nazar-pc/NPW-1.0/renders/2-complexity.png

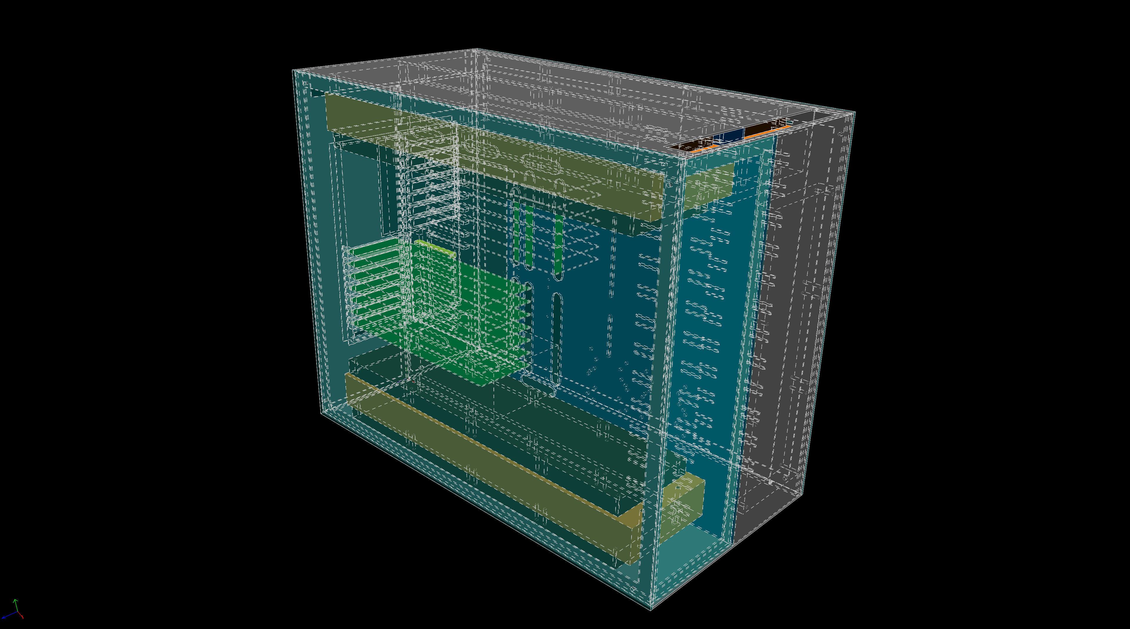
renders/2-complexity.png
