nazar-pc/NPW-1.0/renders/2-left.png

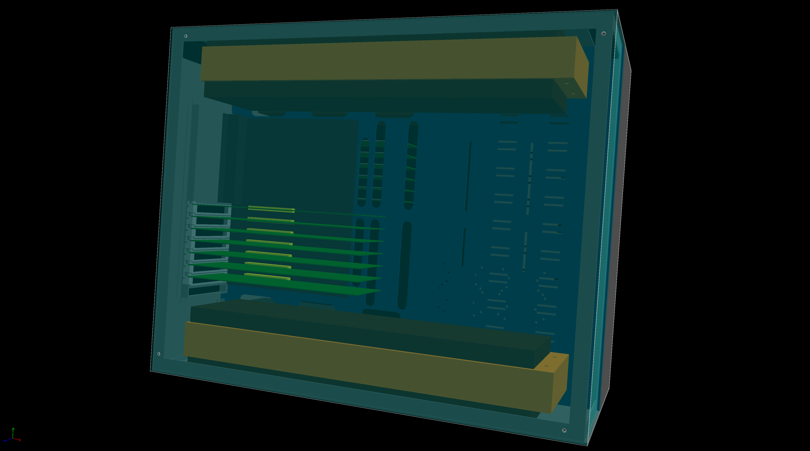
renders/2-left.png
