nazar-pc/NPW-1.0/renders/2-right.png

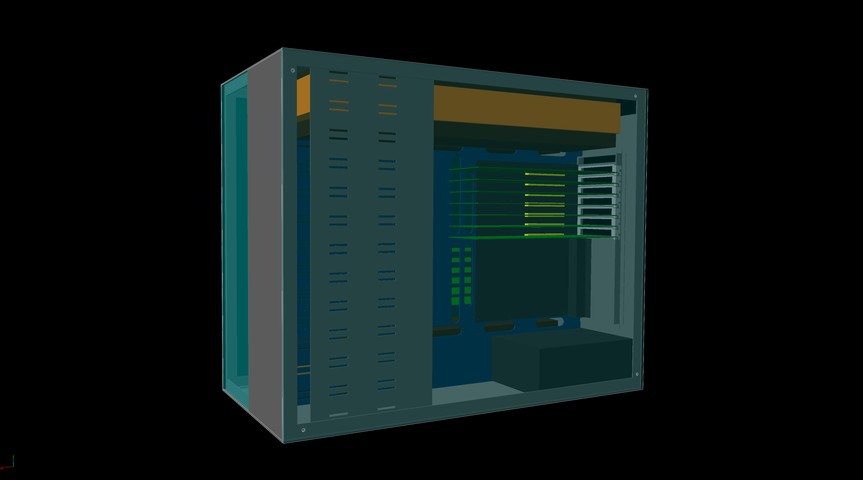
renders/2-right.png
