nazar-pc/NPW-1.0/renders/3-back-right.png

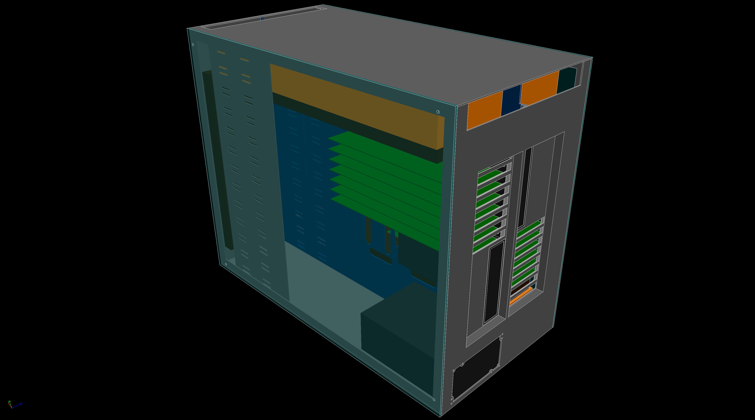
renders/3-back-right.png
