nazar-pc/NPW-1.0/renders/3-left.png

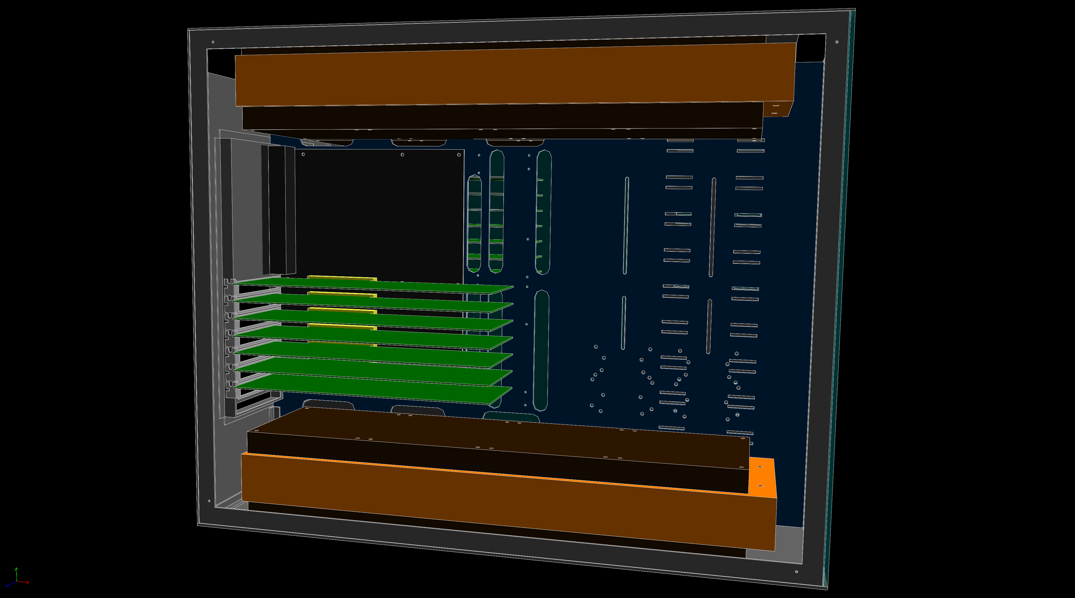
renders/3-left.png
