nazar-pc/NPW-1.0/renders/4-front-panel.png

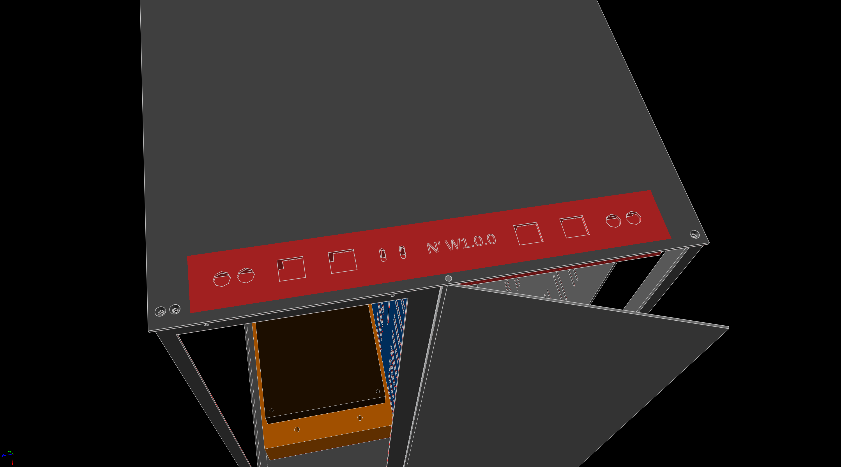
renders/4-front-panel.png
