nazar-pc/NPW-1.0/renders/5-back.png

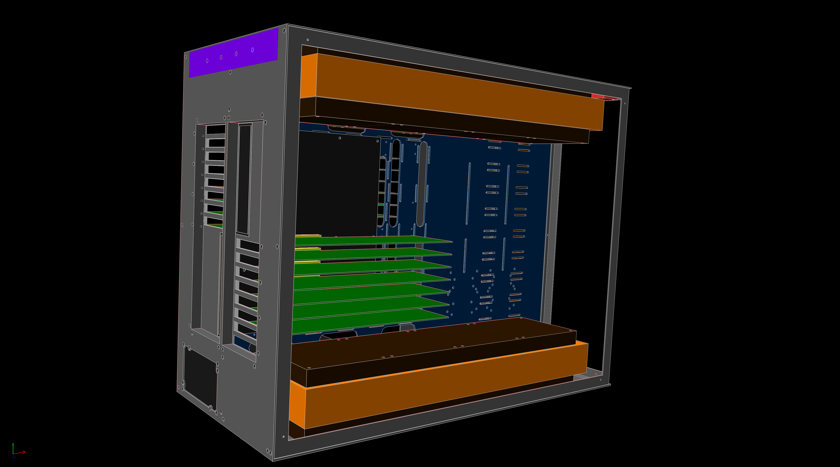
renders/5-back.png
