nazar-pc/NPW-1.0/renders/5-front.png

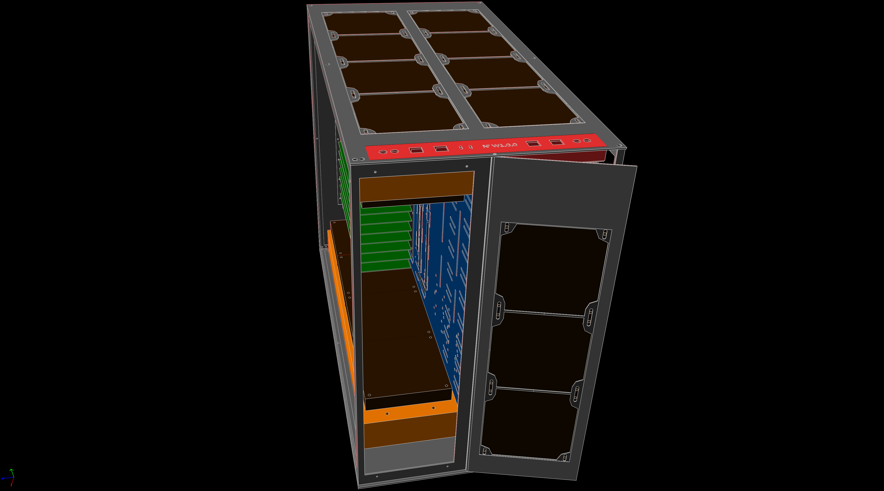
renders/5-front.png
