nazar-pc/NPW-1.0/renders/6-left-bottom.png

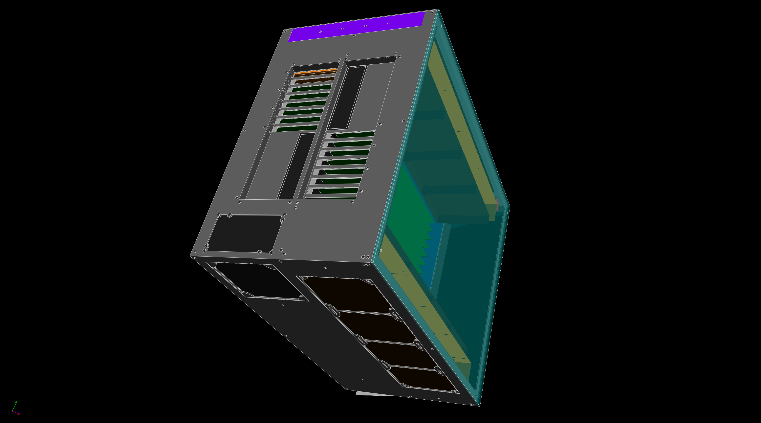
renders/6-left-bottom.png
