nazar-pc/NPW-1.0/renders/6-right-top.png

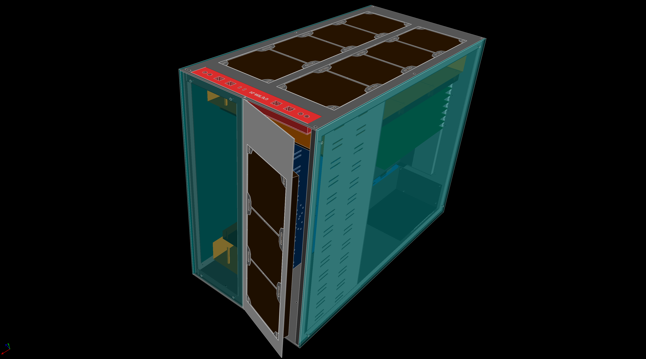
renders/6-right-top.png
