nazar-pc/NPW-1.0/renders/7-back-right.png

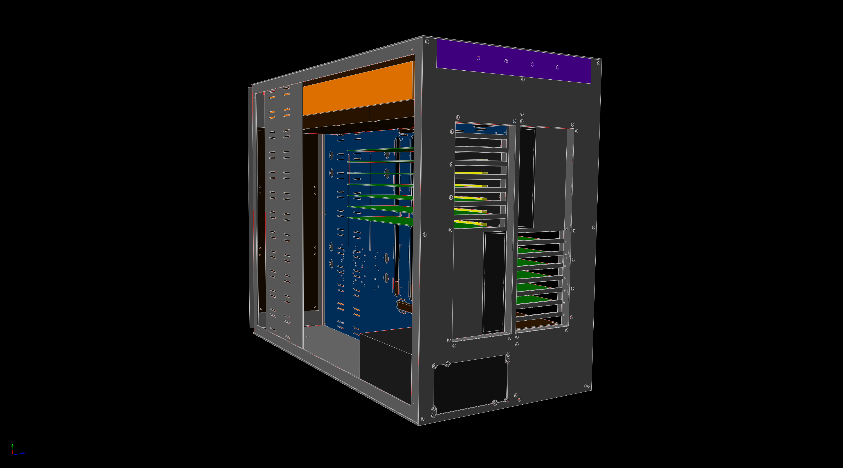
renders/7-back-right.png
