nazar-pc/NPW-1.0/renders/7-left-bottom.png

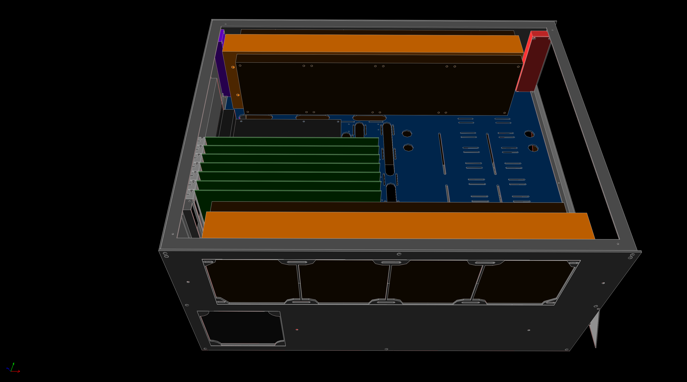
renders/7-left-bottom.png
