nazar-pc/NPW-1.0/renders/7-right-top.png

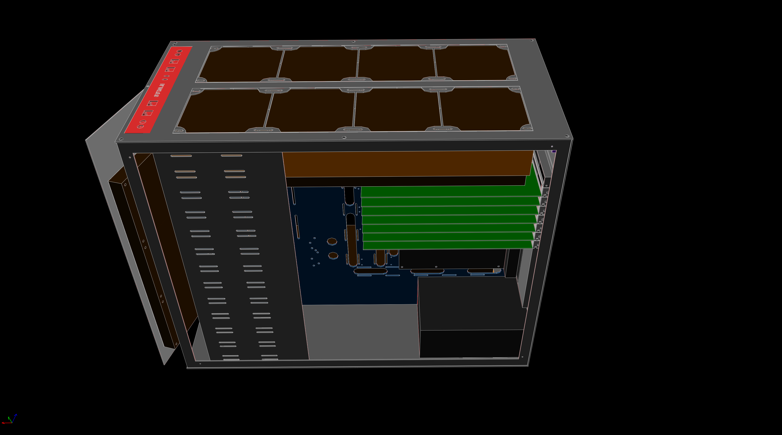
renders/7-right-top.png
