nazar-pc/NPW-1.0/renders/7-top-left.png

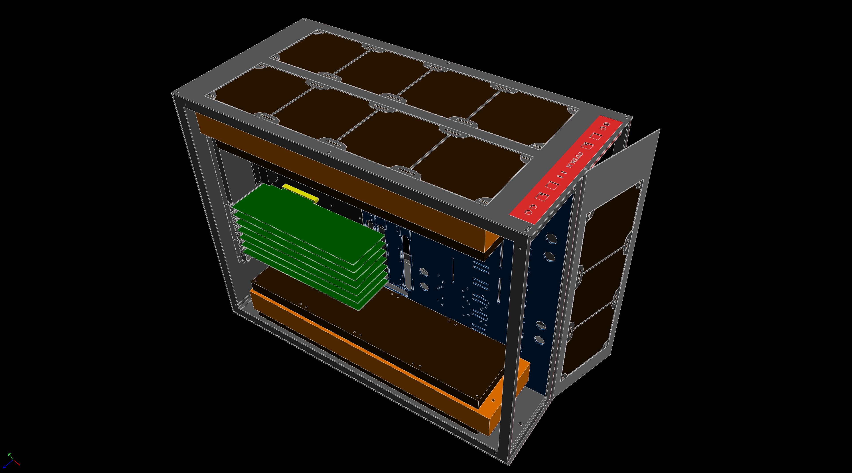
renders/7-top-left.png
