nazar-pc/NPW-1.0/renders/8-back-bottom.png

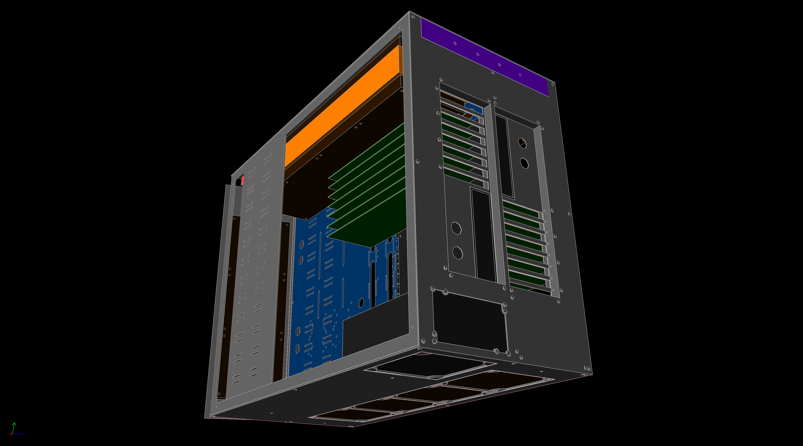
renders/8-back-bottom.png
