nazar-pc/NPW-1.0/renders/9-back-bottom.png

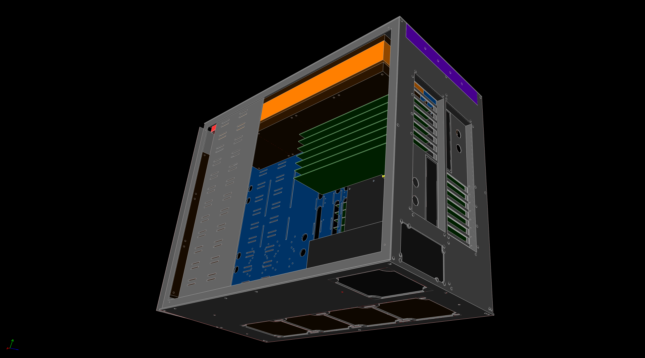
renders/9-back-bottom.png
