nazar-pc/NPW-1.0/renders/9-front-left.png

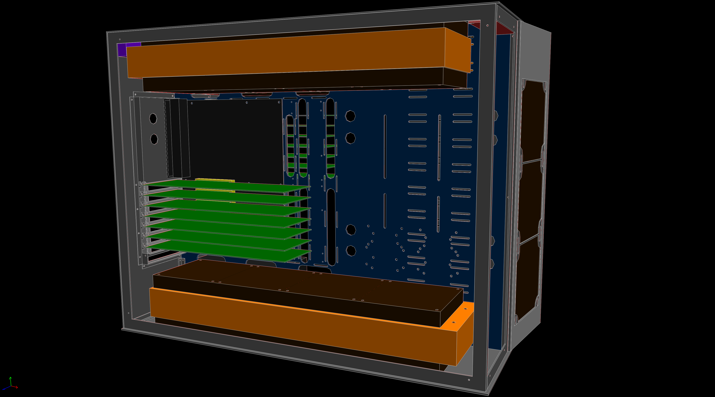
renders/9-front-left.png
