nazar-pc/NPW-1.0/renders/door-mounting-large-scale.png

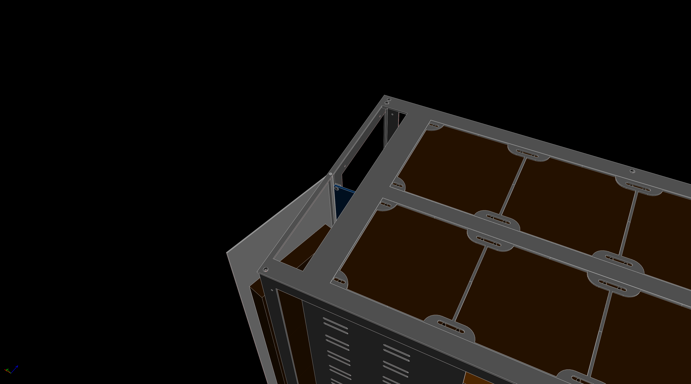
renders/door-mounting-large-scale.png
