nazar-pc/NPW-1.0/renders/door-mounting.png

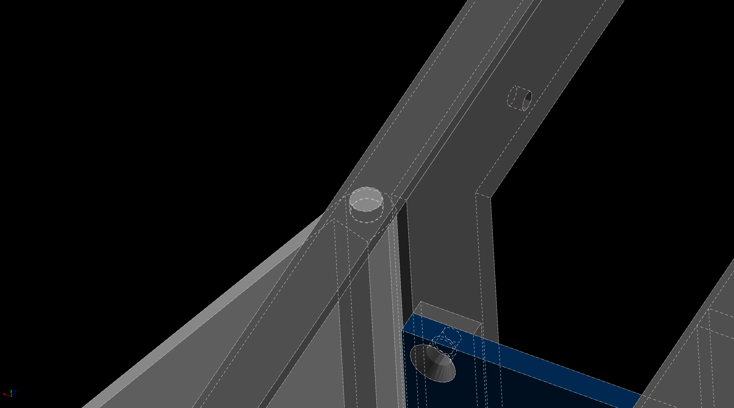
renders/door-mounting.png
