nazar-pc/NPW-1.0/renders/left-back.png

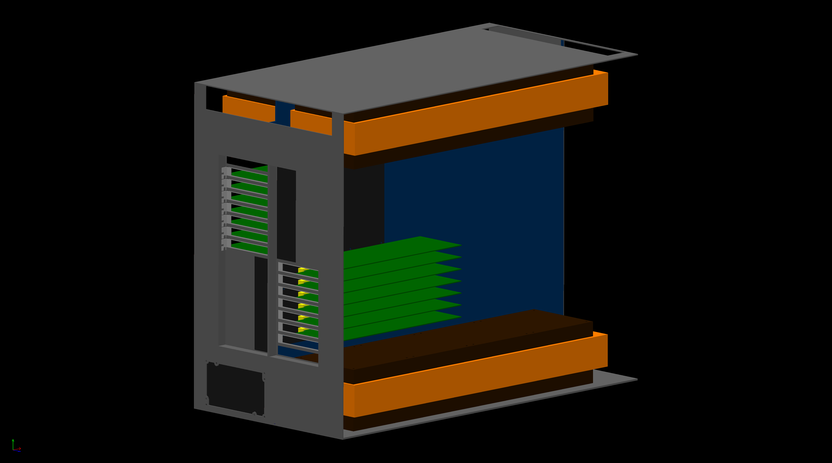
renders/left-back.png
