nazar-pc/NPW-1.0/renders/left-front.png

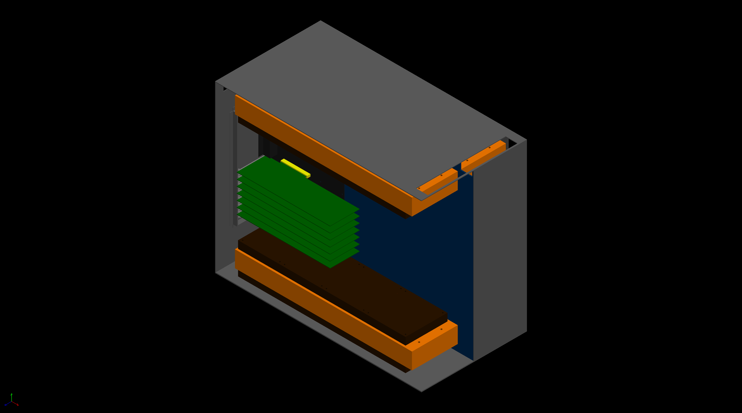
renders/left-front.png
