nazar-pc/NPW-1.0/renders/right-front.png

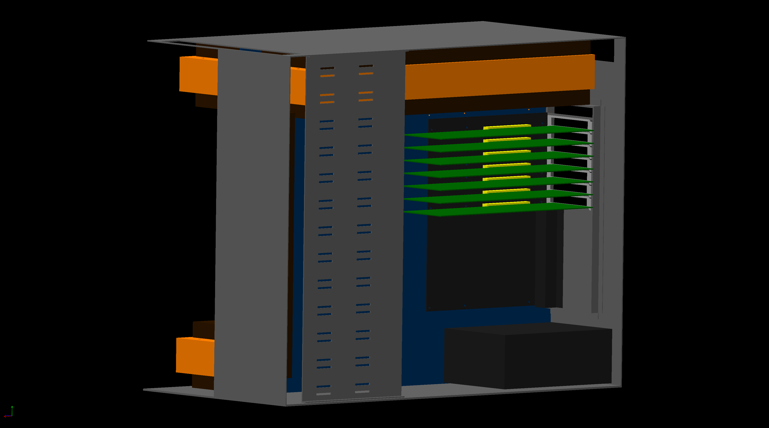
renders/right-front.png
