nazar-pc/NPW-1.0/manufacturing/random-stuff/3D convertion results/back-frame.step

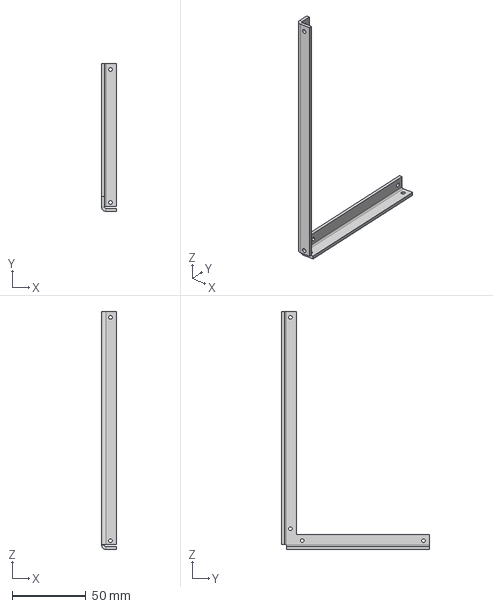
[picture p40: CAD file, 2022-12-24]
manufacturing/random-stuff/3D convertion results/back-frame.step
10.0 x 100.0 x 161.0 mm
