nazar-pc/NPW-1.0/manufacturing/random-stuff/3d-print/top.step

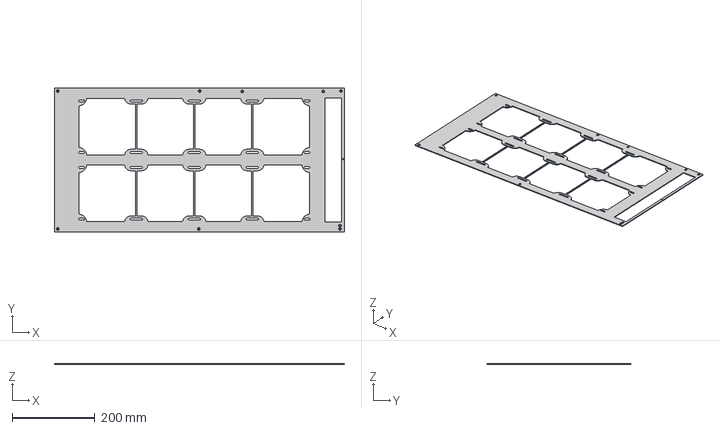
[picture p41: CAD file, 2022-12-24]
manufacturing/random-stuff/3d-print/top.step
700.0 x 347.0 x 2.00 mm
