nazar-pc/NPW-1.0/manufacturing/random-stuff/Assembly -2019.03.23/right-frame.SLDPRT

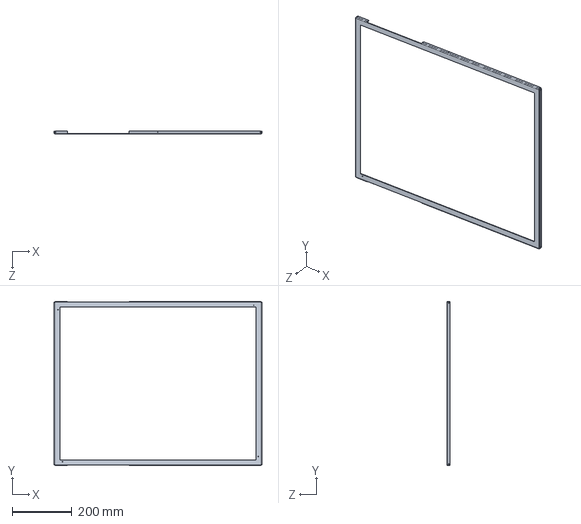
[picture p42: CAD file, 2022-12-24]
manufacturing/random-stuff/Assembly -2019.03.23/right-frame.SLDPRT
695.5 x 550.0 x 10.0 mm
