nazar-pc/NPW-1.0/manufacturing/random-stuff/Dual MB PC Case - sheet metal/Flat pattern - back.DXF

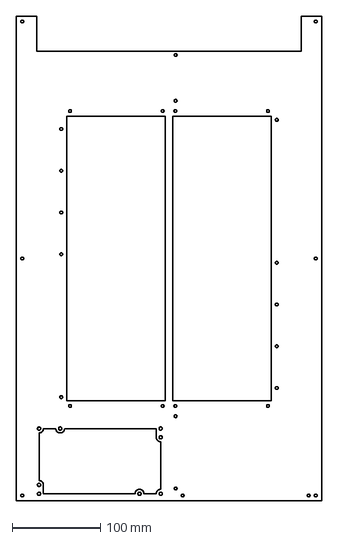
[picture p43: CAD file, 2022-12-24]
manufacturing/random-stuff/Dual MB PC Case - sheet metal/Flat pattern - back.DXF
347.0 x 550.0 mm
