nazar-pc/NPW-1.0/manufacturing/random-stuff/Dual MB PC Case - sheet metal/pc-case.dxf/3mm-bottom.DXF

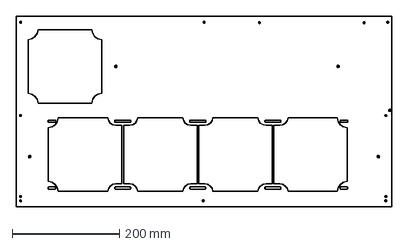
[picture p44: CAD file, 2022-12-24]
manufacturing/random-stuff/Dual MB PC Case - sheet metal/pc-case.dxf/3mm-bottom.DXF
700.0 x 355.0 mm
