nazar-pc/NPW-1.0/manufacturing/random-stuff/Dual mobo PC case full set/step/front-metal.step

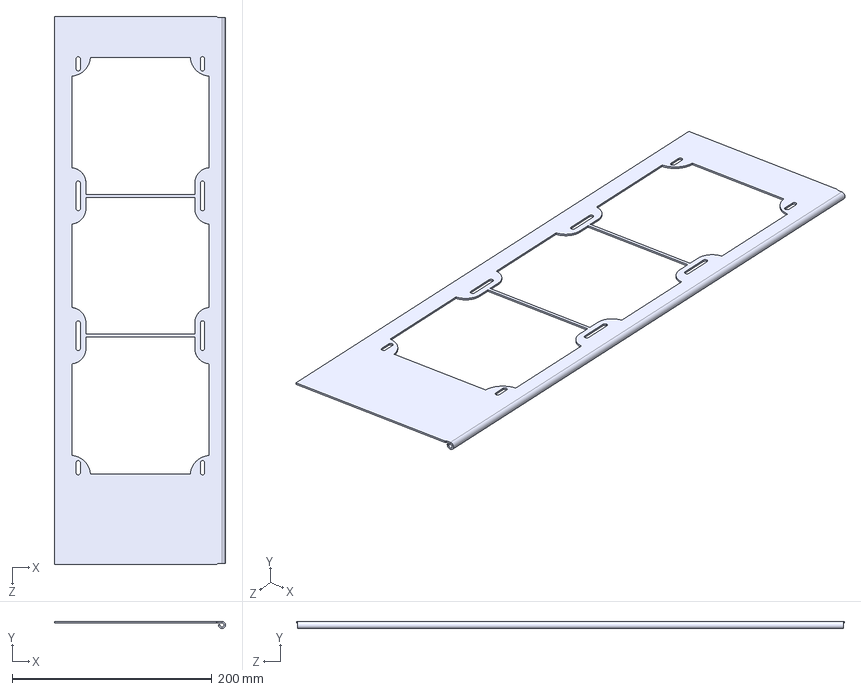
[picture p45: CAD file, 2022-12-24]
manufacturing/random-stuff/Dual mobo PC case full set/step/front-metal.step
171.2 x 7.00 x 549.0 mm
