nazar-pc/NPW-1.0/manufacturing/random-stuff/Hinge with hole.STL

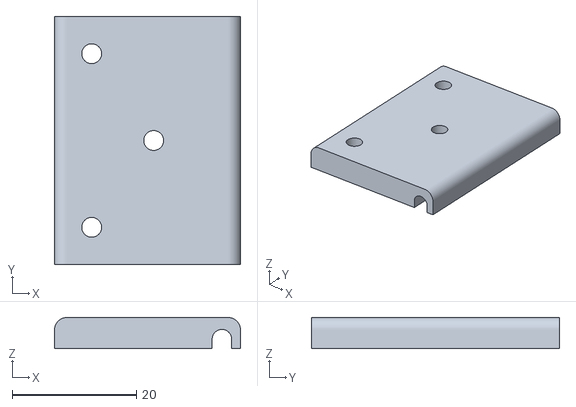
[picture p46: CAD file, 2022-12-24]
manufacturing/random-stuff/Hinge with hole.STL
30.0 x 40.0 x 5.00
