nazar-pc/NPW-1.0/manufacturing/random-stuff/laser-cut/fan-filter.dxf

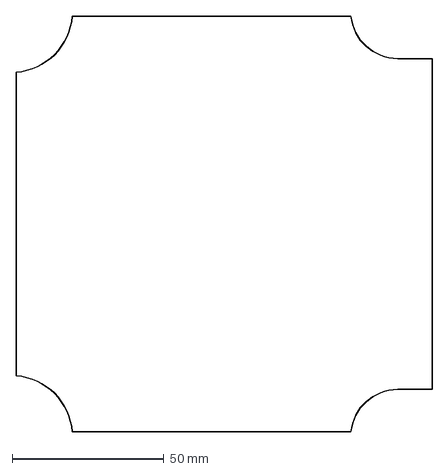
[picture p47: CAD file, 2022-12-24]
manufacturing/random-stuff/laser-cut/fan-filter.dxf
137.0 x 137.0 mm
