nazar-pc/NPW-1.0/manufacturing/step/back-frame-top.step

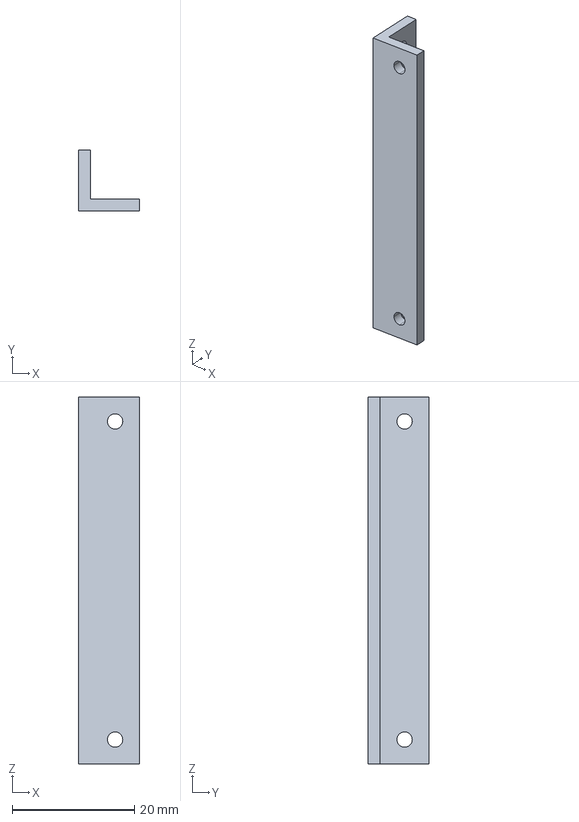
[picture p48: CAD file, 2022-12-24]
manufacturing/step/back-frame-top.step
10.0 x 10.0 x 60.0 mm
