nazar-pc/NPW-1.0/manufacturing/dxf/3d-odd-bay-side.dxf

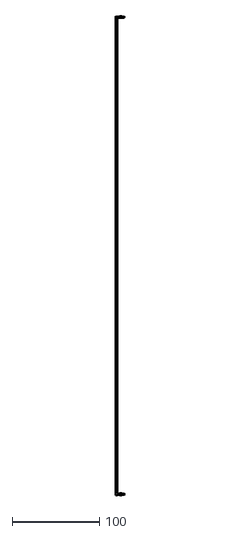
[picture p49: CAD file, 2022-12-24]
manufacturing/dxf/3d-odd-bay-side.dxf
10.0 x 550.0
