nazar-pc/NPW-1.0/manufacturing/random-stuff/3D convertion results/back-frame-top.step

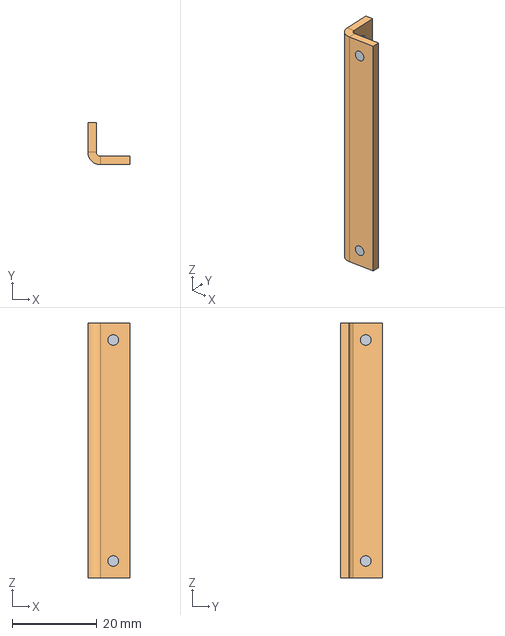
[picture p50: CAD file, 2022-12-24]
manufacturing/random-stuff/3D convertion results/back-frame-top.step
10.0 x 10.0 x 60.0 mm
