nazar-pc/NPW-1.0/manufacturing/random-stuff/3d-print/front-panel-top-base.stl

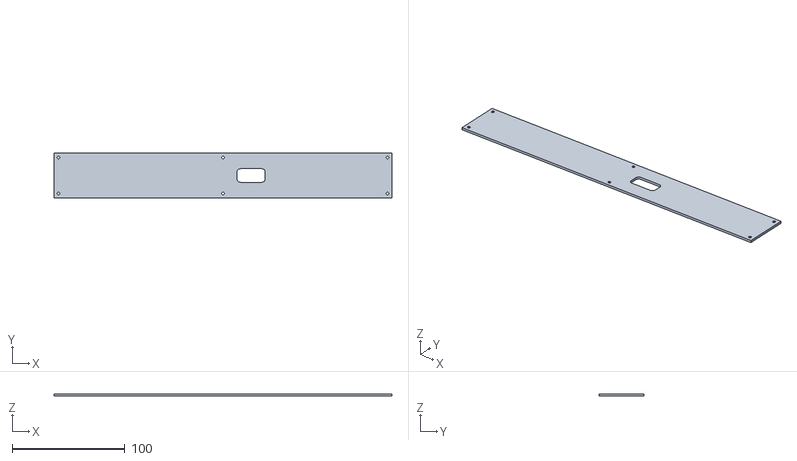
[picture p51: CAD file, 2022-12-24]
manufacturing/random-stuff/3d-print/front-panel-top-base.stl
300.0 x 40.0 x 2.00
