nazar-pc/NPW-1.0/manufacturing/random-stuff/Dual MB PC Case - sheet metal/pc-case.dxf/2mm-odd-bay-side.DXF

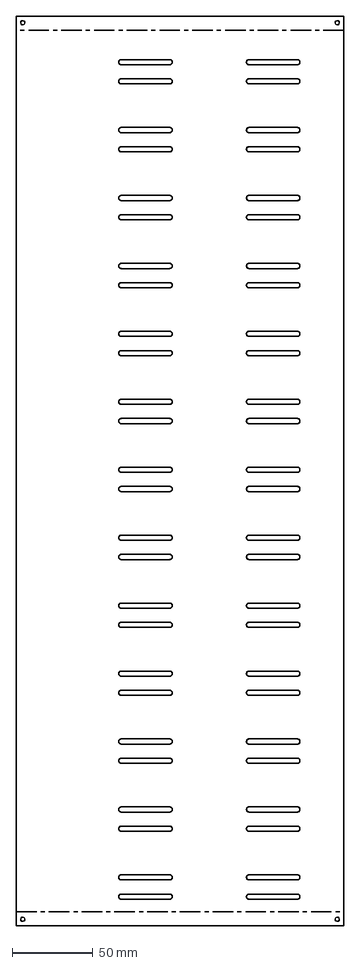
[picture p52: CAD file, 2022-12-24]
manufacturing/random-stuff/Dual MB PC Case - sheet metal/pc-case.dxf/2mm-odd-bay-side.DXF
203.2 x 564.3 mm
