nazar-pc/NPW-1.0/manufacturing/random-stuff/Dual mobo PC case full set/step/bottom.step

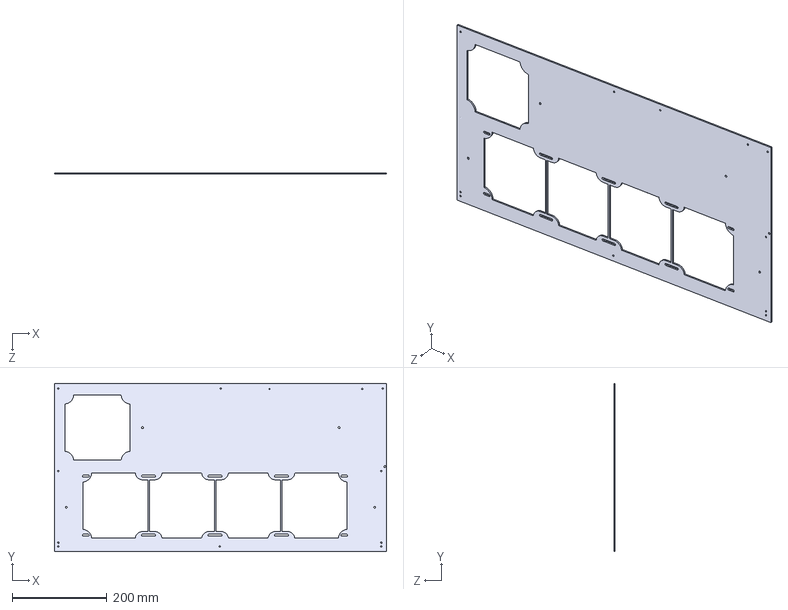
[picture p53: CAD file, 2022-12-24]
manufacturing/random-stuff/Dual mobo PC case full set/step/bottom.step
700.0 x 355.0 x 3.00 mm
