nazar-pc/NPW-1.0/manufacturing/random-stuff/laser-cut/fan-filter-middle.dxf

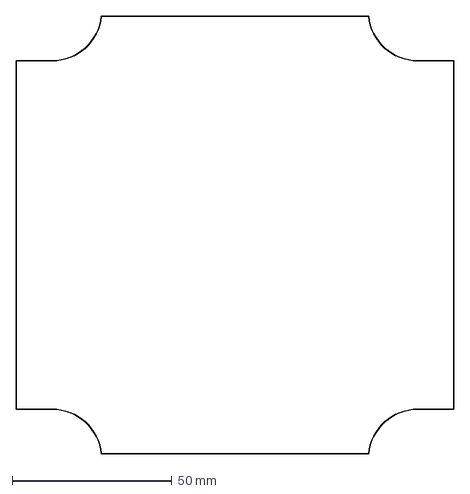
[picture p54: CAD file, 2022-12-24]
manufacturing/random-stuff/laser-cut/fan-filter-middle.dxf
137.0 x 137.0 mm
