nazar-pc/NPW-1.0/manufacturing/step/front-metal.step

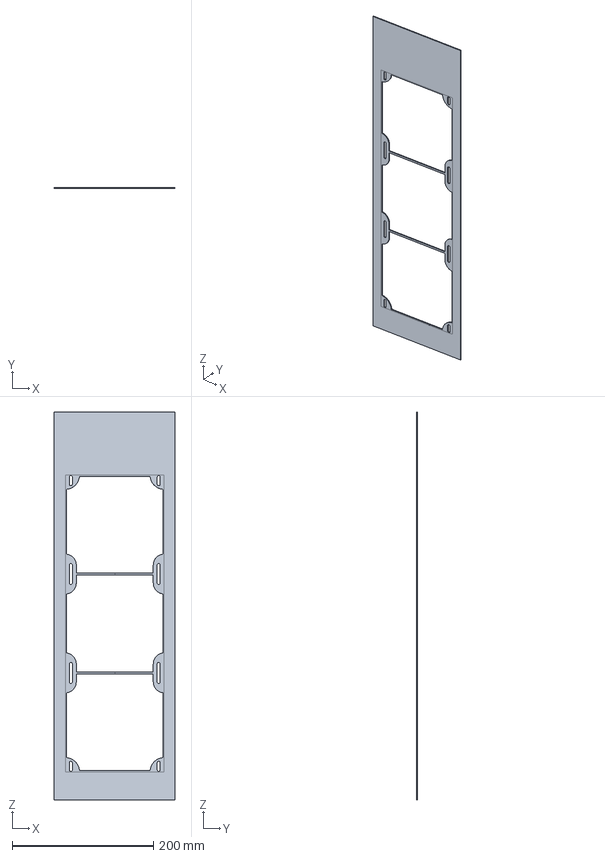
[picture p55: CAD file, 2022-12-24]
manufacturing/step/front-metal.step
171.2 x 1.50 x 549.5 mm
