nazar-pc/NPW-1.0/manufacturing/dxf/3mm-motherboard-tray.dxf

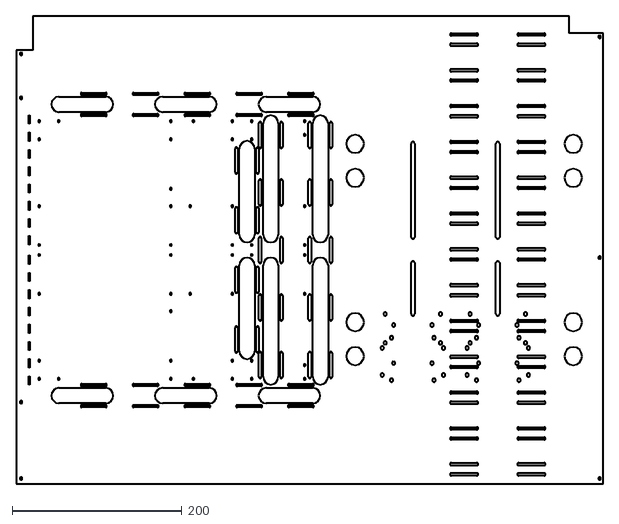
[picture p56: CAD file, 2022-12-24]
manufacturing/dxf/3mm-motherboard-tray.dxf
691.0 x 550.0
