nazar-pc/NPW-1.0/manufacturing/random-stuff/3D convertion results/front-frame.step

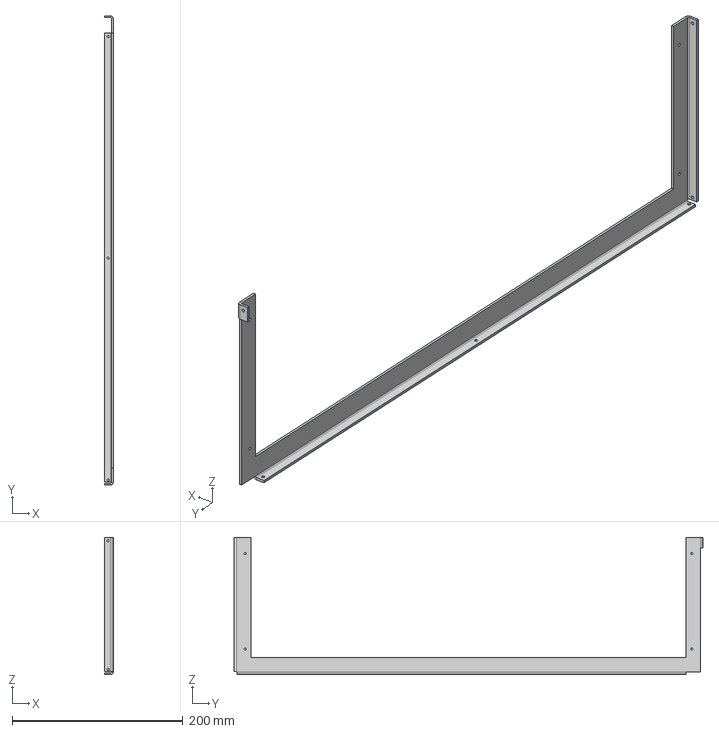
[picture p57: CAD file, 2022-12-24]
manufacturing/random-stuff/3D convertion results/front-frame.step
10.0 x 550.0 x 161.0 mm
