nazar-pc/NPW-1.0/manufacturing/random-stuff/left.step

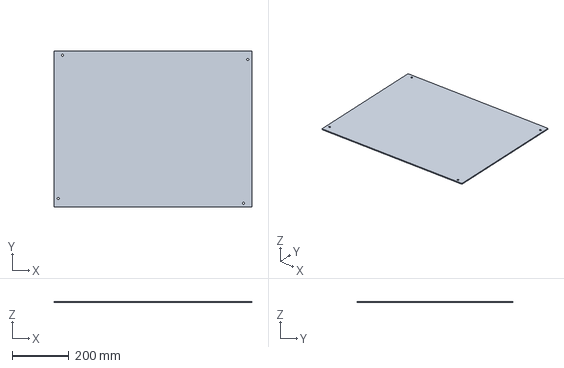
[picture p59: CAD file, 2022-12-24]
manufacturing/random-stuff/left.step
700.0 x 551.0 x 4.00 mm
