nazar-pc/NPW-1.0/manufacturing/step/right-frame.step

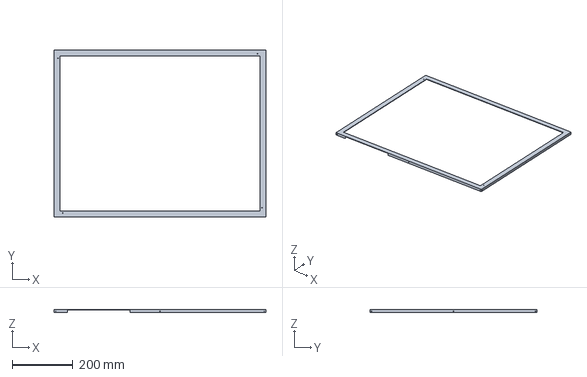
[picture p60: CAD file, 2022-12-24]
manufacturing/step/right-frame.step
696.5 x 550.0 x 10.0 mm
