nazar-pc/NPW-1.0/manufacturing/dxf/2mm-top.dxf

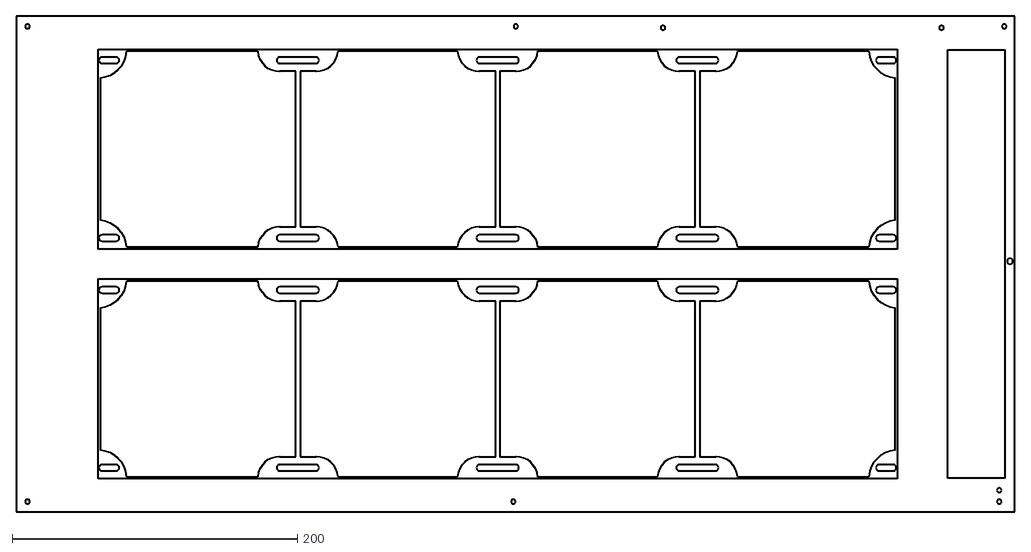
[picture p61: CAD file, 2022-12-24]
manufacturing/dxf/2mm-top.dxf
700.0 x 347.0
