nazar-pc/NPW-1.0/manufacturing/random-stuff/Assembly -2019.03.23/bottom.SLDPRT

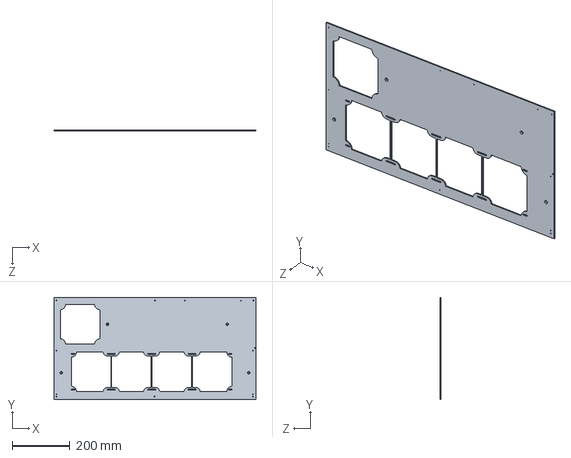
[picture p63: CAD file, 2022-12-24]
manufacturing/random-stuff/Assembly -2019.03.23/bottom.SLDPRT
700.0 x 355.0 x 3.00 mm
