nazar-pc/NPW-1.0/manufacturing/random-stuff/Dual MB PC Case - sheet metal/back.STEP

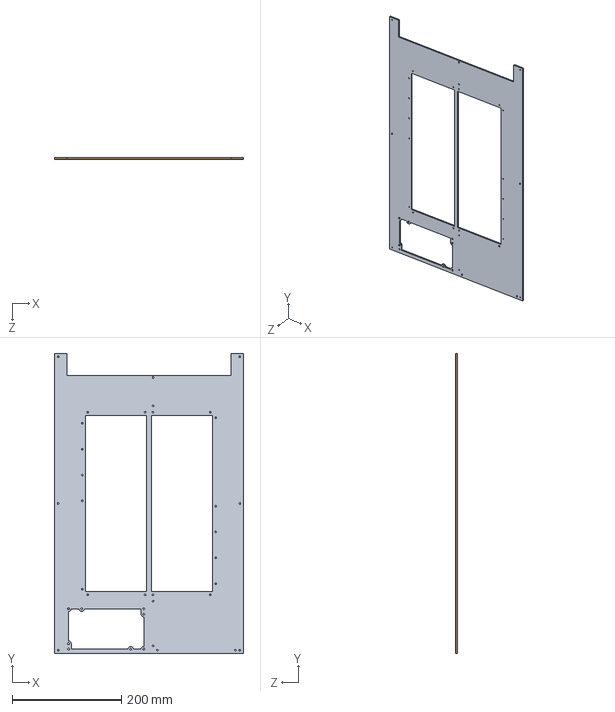
[picture p64: CAD file, 2022-12-24]
manufacturing/random-stuff/Dual MB PC Case - sheet metal/back.STEP
347.0 x 550.0 x 3.00 mm
