nazar-pc/NPW-1.0/manufacturing/random-stuff/Dual mobo PC case full set/step/odd-bay-side.step

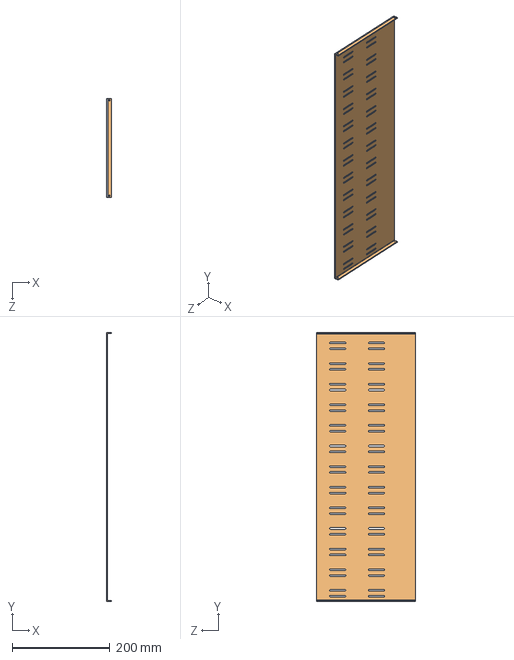
[picture p65: CAD file, 2022-12-24]
manufacturing/random-stuff/Dual mobo PC case full set/step/odd-bay-side.step
10.0 x 550.0 x 203.2 mm
