nazar-pc/NPW-1.0/manufacturing/step/odd-bay-side.step

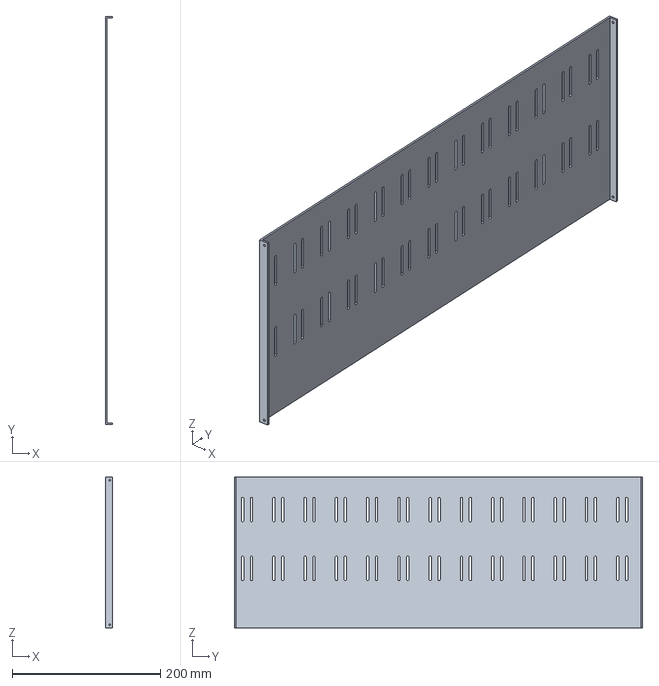
[picture p66: CAD file, 2022-12-24]
manufacturing/step/odd-bay-side.step
10.0 x 550.0 x 203.2 mm
