nazar-pc/NPW-1.0/manufacturing/dxf/2mm-back.dxf

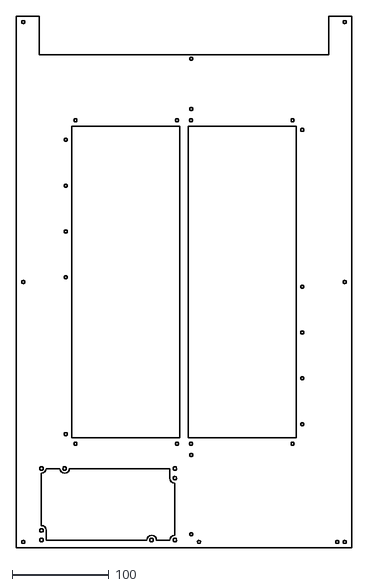
[picture p67: CAD file, 2022-12-24]
manufacturing/dxf/2mm-back.dxf
347.0 x 550.0
