nazar-pc/NPW-1.0/manufacturing/random-stuff/Assembly -2019.03.23/back.SLDPRT

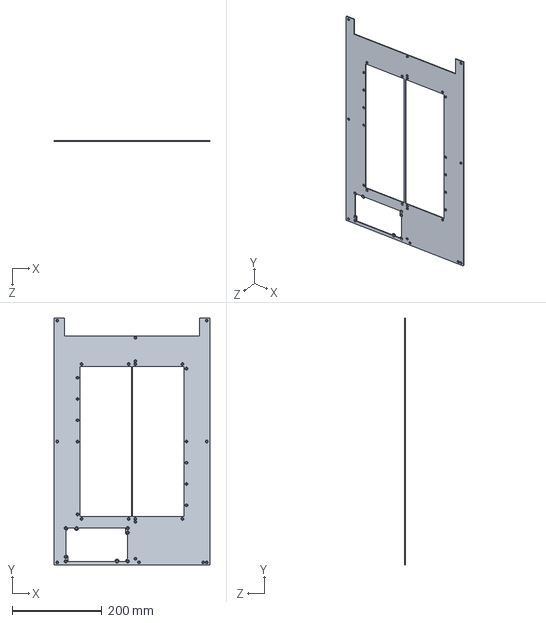
[picture p69: CAD file, 2022-12-24]
manufacturing/random-stuff/Assembly -2019.03.23/back.SLDPRT
347.0 x 550.0 x 2.00 mm
