nazar-pc/NPW-1.0/manufacturing/random-stuff/Dual MB PC Case - sheet metal/pc-case.dxf/1.5mm-front-metal.DXF

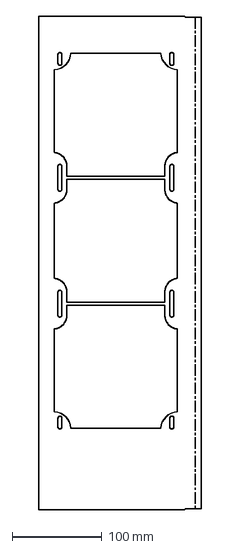
[picture p70: CAD file, 2022-12-24]
manufacturing/random-stuff/Dual MB PC Case - sheet metal/pc-case.dxf/1.5mm-front-metal.DXF
181.2 x 549.0 mm
