nazar-pc/NPW-1.0/manufacturing/step/bottom.step

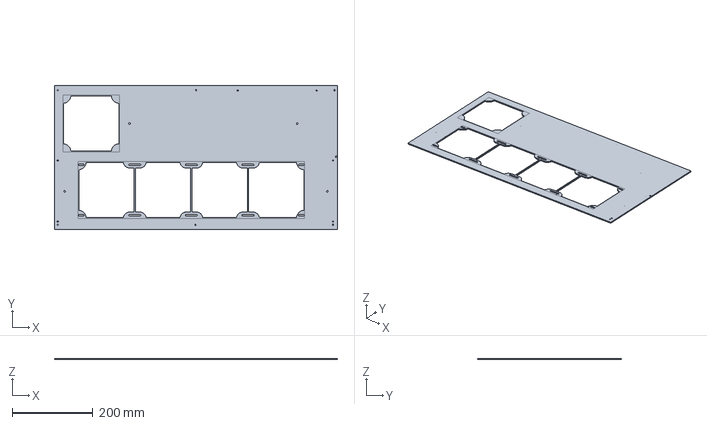
[picture p71: CAD file, 2022-12-24]
manufacturing/step/bottom.step
700.0 x 355.0 x 3.00 mm
