nazar-pc/NPW-1.0/manufacturing/dxf/3d-io-tray-x2.dxf

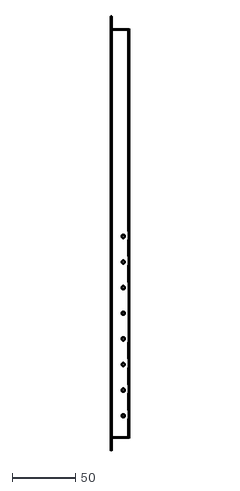
[picture p72: CAD file, 2022-12-24]
manufacturing/dxf/3d-io-tray-x2.dxf
15.0 x 344.8
