nazar-pc/NPW-1.0/manufacturing/random-stuff/3d-print/fan-hole-insert-3mm.step

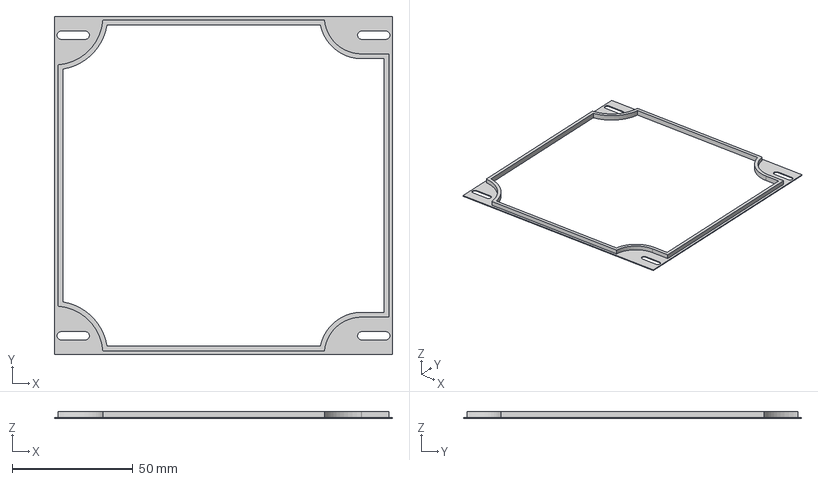
[picture p73: CAD file, 2022-12-24]
manufacturing/random-stuff/3d-print/fan-hole-insert-3mm.step
140.0 x 140.0 x 3.00 mm
