nazar-pc/NPW-1.0/manufacturing/random-stuff/Assembly -2019.03.23/back-frame-top.SLDPRT

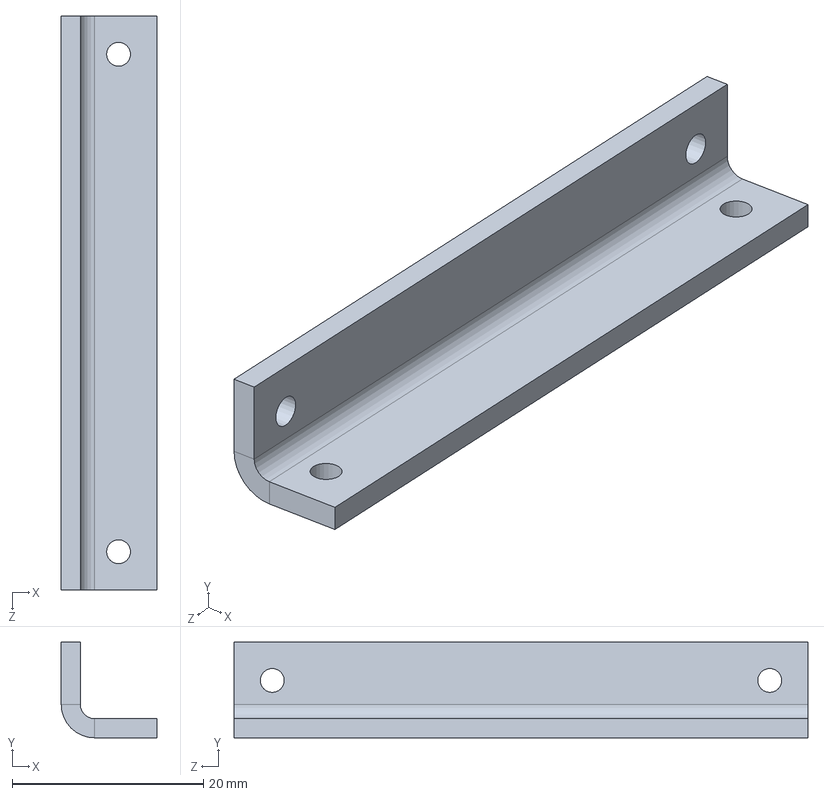
[picture p74: CAD file, 2022-12-24]
manufacturing/random-stuff/Assembly -2019.03.23/back-frame-top.SLDPRT
10.0 x 10.0 x 60.0 mm
