nazar-pc/NPW-1.0/manufacturing/random-stuff/Dual MB PC Case - sheet metal/pc-case.dxf/1mm-io-tray-x2.DXF

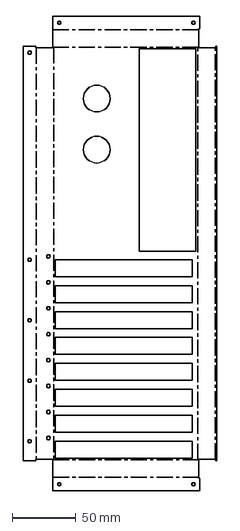
[picture p75: CAD file, 2022-12-24]
manufacturing/random-stuff/Dual MB PC Case - sheet metal/pc-case.dxf/1mm-io-tray-x2.DXF
151.7 x 371.4 mm
