nazar-pc/NPW-1.0/manufacturing/random-stuff/3d-print/fan-hole-insert-2mm-middle v2.step

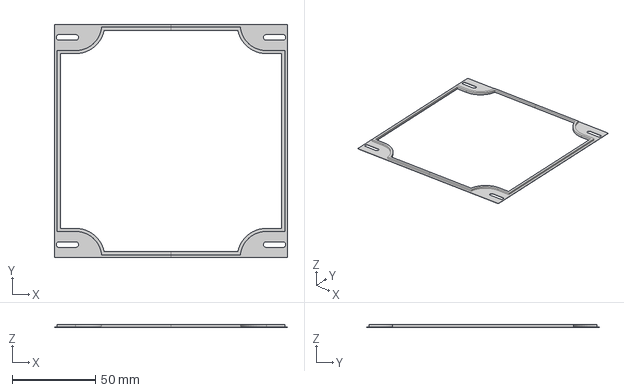
[picture p76: CAD file, 2022-12-24]
manufacturing/random-stuff/3d-print/fan-hole-insert-2mm-middle v2.step
140.0 x 140.0 x 2.00 mm
