nazar-pc/NPW-1.0/manufacturing/random-stuff/Assembly -2019.03.23/IO-frame.SLDPRT

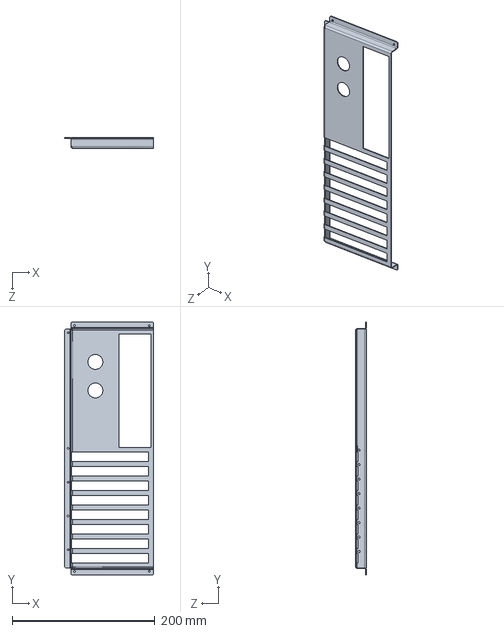
[picture p77: CAD file, 2022-12-24]
manufacturing/random-stuff/Assembly -2019.03.23/IO-frame.SLDPRT
124.8 x 354.8 x 15.0 mm
