nazar-pc/NPW-1.0/manufacturing/random-stuff/Hinge.STL

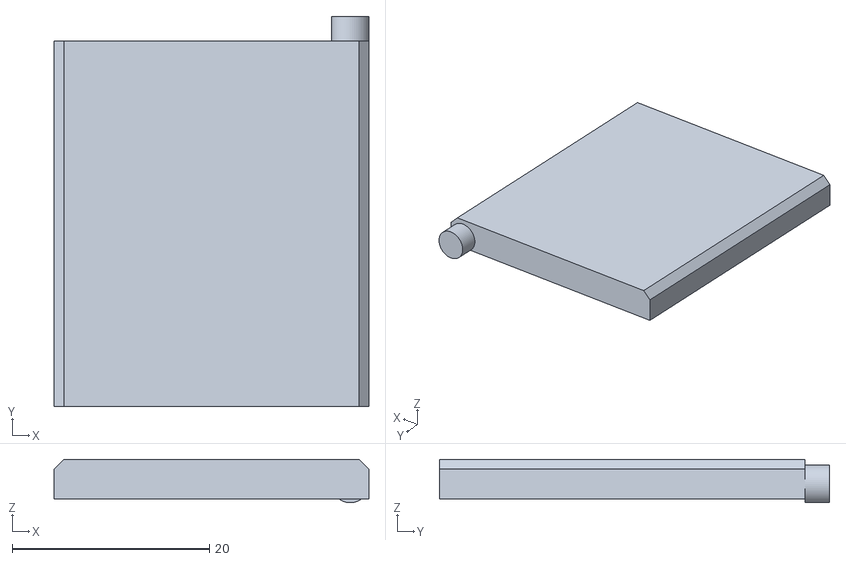
[picture p78: CAD file, 2022-12-24]
manufacturing/random-stuff/Hinge.STL
31.9 x 39.5 x 4.40
