nazar-pc/NPW-1.0/manufacturing/random-stuff/3d-print/3mm insert.step

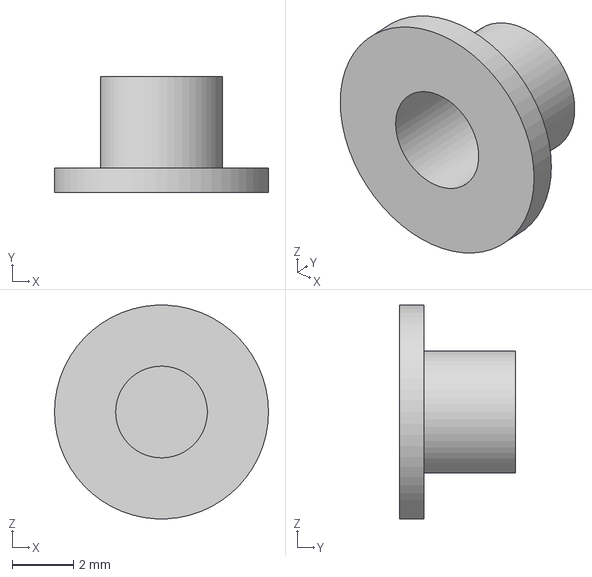
[picture p79: CAD file, 2022-12-24]
manufacturing/random-stuff/3d-print/3mm insert.step
7.00 x 3.80 x 6.99 mm
