nazar-pc/NPW-1.0/manufacturing/step/top.step

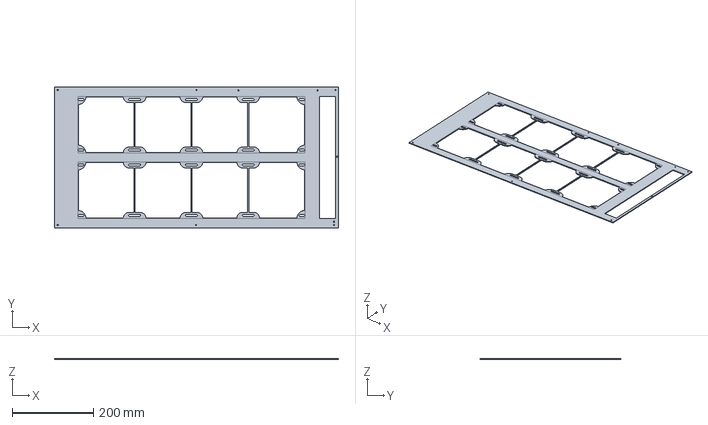
[picture p80: CAD file, 2022-12-24]
manufacturing/step/top.step
700.0 x 347.0 x 2.00 mm
