nazar-pc/NPW-1.0/manufacturing/random-stuff/3d-print/glass-mount-top.step

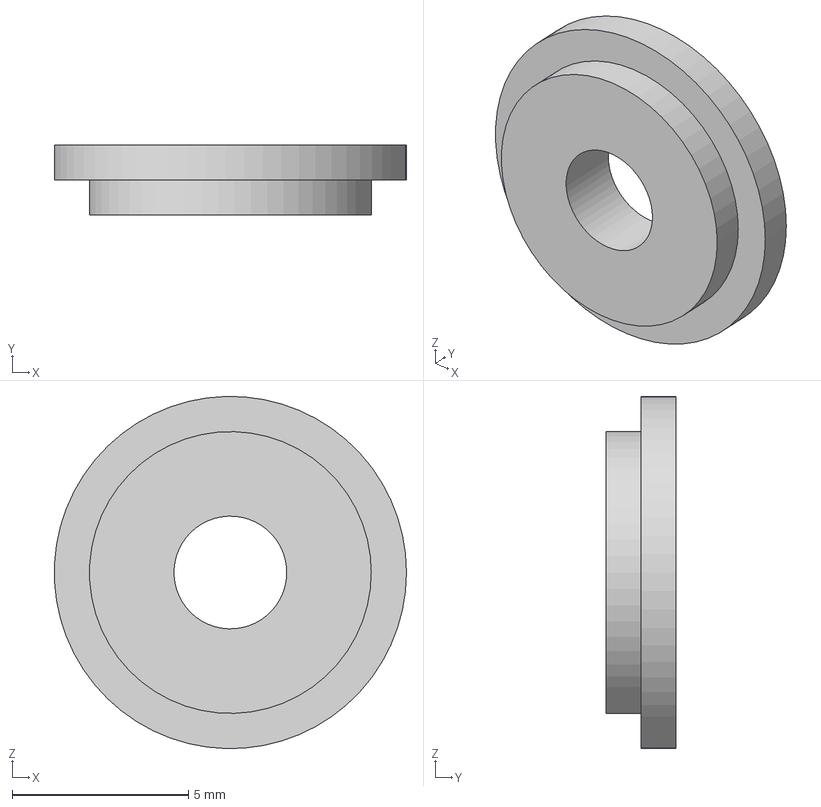
[picture p81: CAD file, 2022-12-24]
manufacturing/random-stuff/3d-print/glass-mount-top.step
9.99 x 2.00 x 10.00 mm
