nazar-pc/NPW-1.0/manufacturing/random-stuff/Assembly -2019.03.23/io-tray-x2_SM.SLDPRT

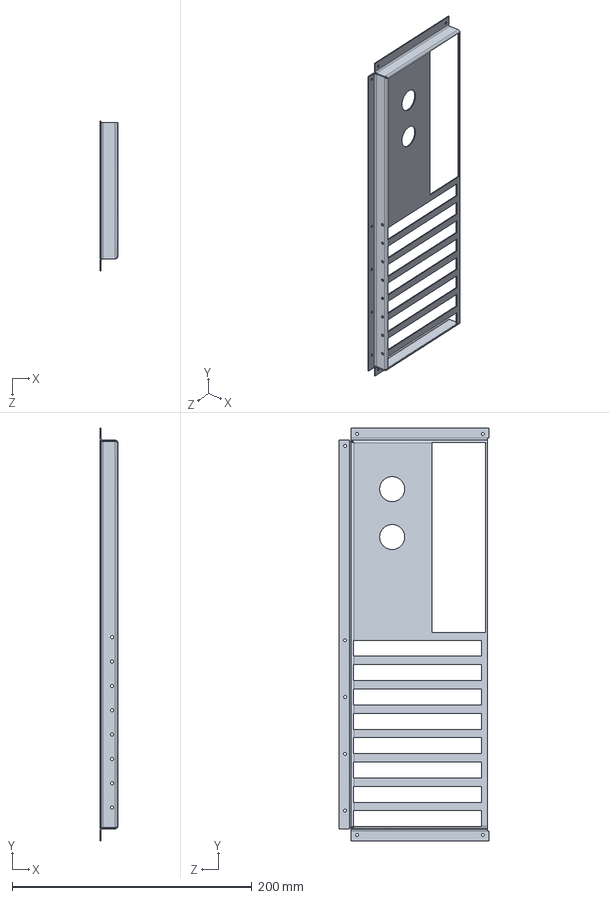
[picture p82: CAD file, 2022-12-24]
manufacturing/random-stuff/Assembly -2019.03.23/io-tray-x2_SM.SLDPRT
15.0 x 344.8 x 125.1 mm
