nazar-pc/NPW-1.0/manufacturing/random-stuff/glass-mount-v2.stl

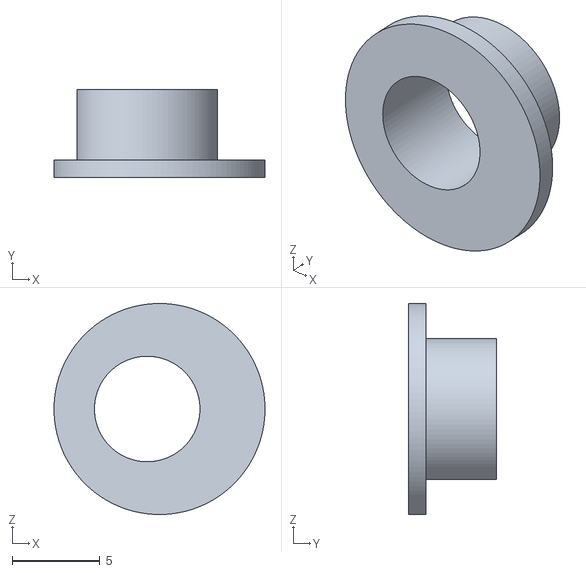
[picture p83: CAD file, 2022-12-24]
manufacturing/random-stuff/glass-mount-v2.stl
12.0 x 5.00 x 12.0
