nazar-pc/NPW-1.0/manufacturing/random-stuff/multi-ssd-cage-7x.stl

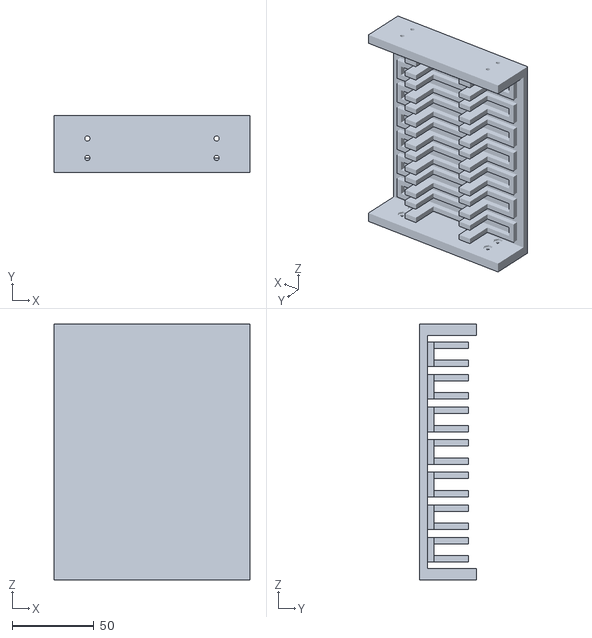
[picture p84: CAD file, 2022-12-24]
manufacturing/random-stuff/multi-ssd-cage-7x.stl
120.0 x 35.0 x 157.1
