nazar-pc/NPW-1.0/manufacturing/random-stuff/3d-print/front-panel-lock.step

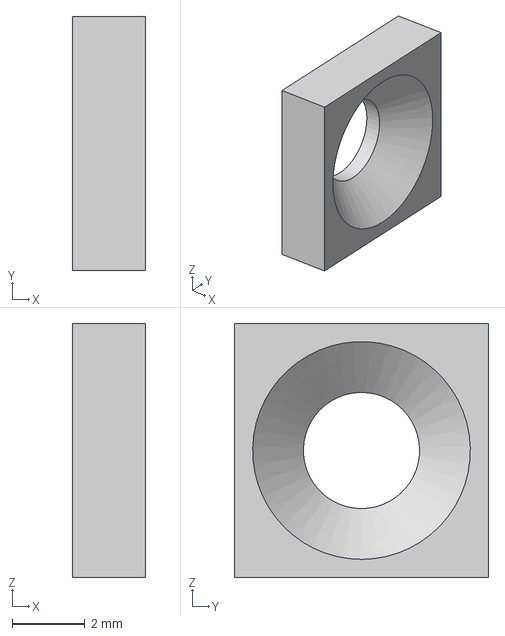
[picture p85: CAD file, 2022-12-24]
manufacturing/random-stuff/3d-print/front-panel-lock.step
2.00 x 7.00 x 7.00 mm
