nazar-pc/NPW-1.0/manufacturing/random-stuff/Assembly -2019.03.23/front-metal.SLDPRT

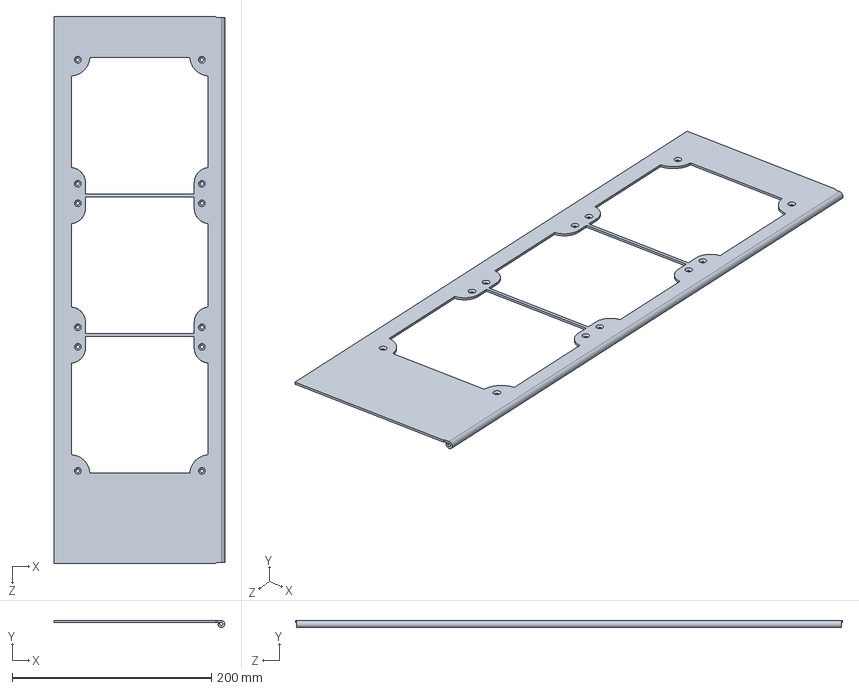
[picture p86: CAD file, 2022-12-24]
manufacturing/random-stuff/Assembly -2019.03.23/front-metal.SLDPRT
171.2 x 6.99 x 549.0 mm
