nazar-pc/NPW-1.0/manufacturing/random-stuff/side.dxf

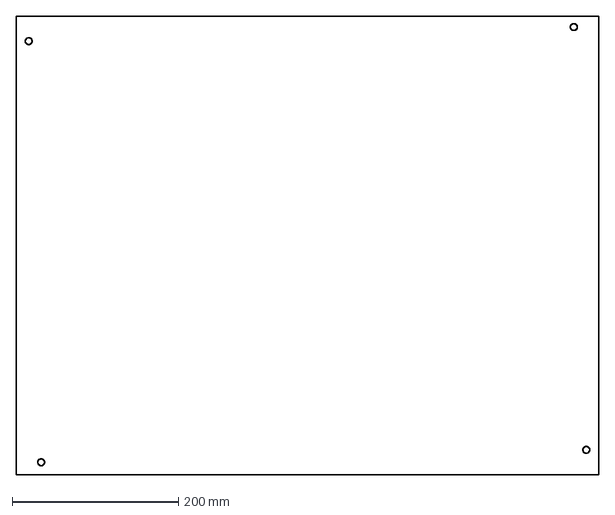
[picture p87: CAD file, 2022-12-24]
manufacturing/random-stuff/side.dxf
700.0 x 551.0 mm
