nazar-pc/NPW-1.0/manufacturing/random-stuff/front-glass.dxf

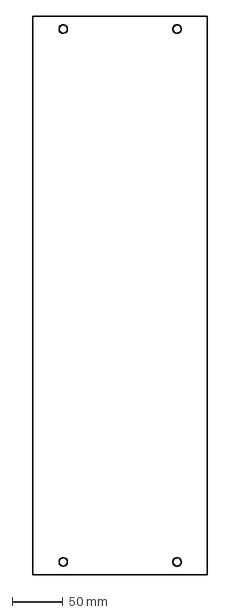
[picture p88: CAD file, 2022-12-24]
manufacturing/random-stuff/front-glass.dxf
171.8 x 549.5 mm
