nazar-pc/NPW-1.0/manufacturing/random-stuff/front-metal.step

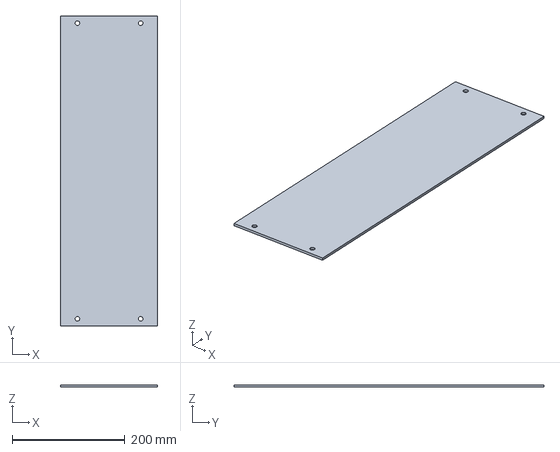
[picture p89: CAD file, 2022-12-24]
manufacturing/random-stuff/front-metal.step
171.8 x 549.5 x 4.00 mm
