nazar-pc/NPW-1.0/manufacturing/pdf/odd-bay-side.pdf

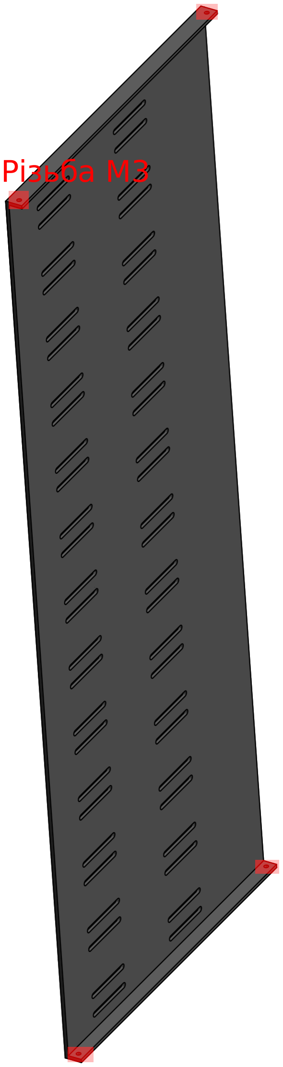
[picture p96: page 1]

Різьба М3
