nazar-pc/NPW-1.0/manufacturing/pdf/right-frame.pdf

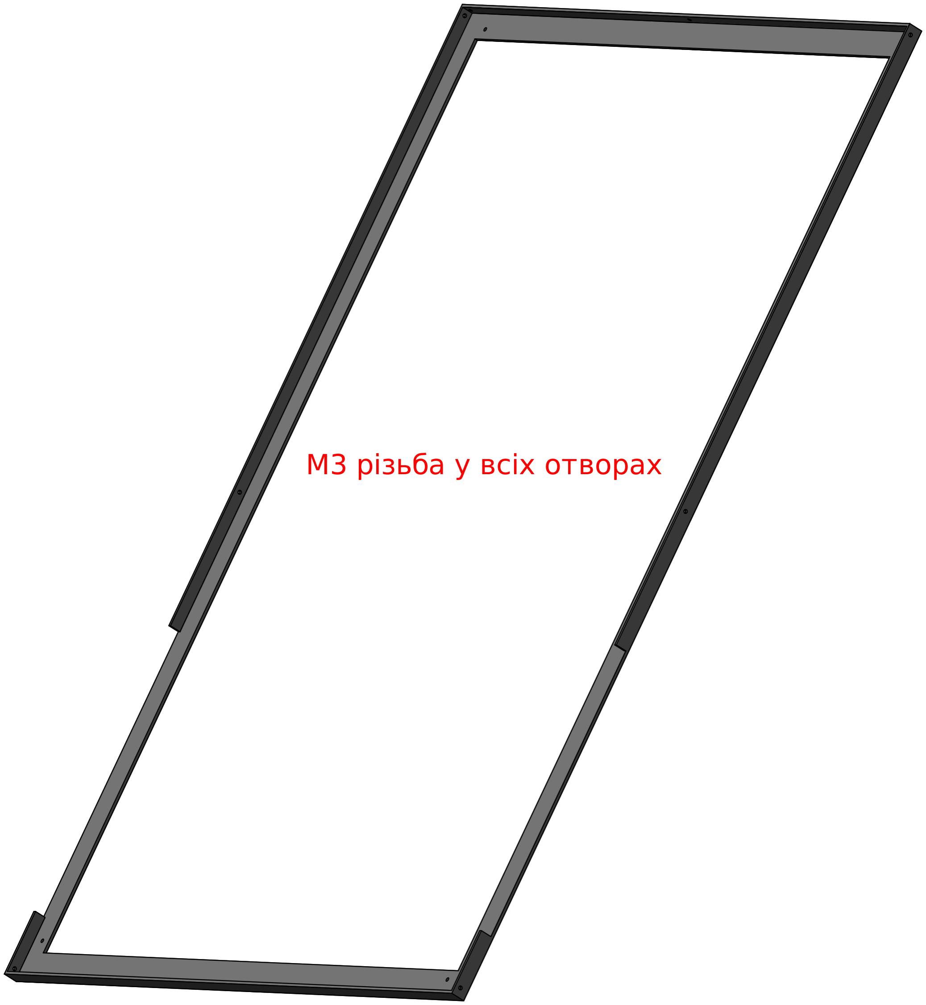
[picture p97: page 1]

М3 різьба у всіх отворах
