nazar-pc/NPW-1.0/manufacturing/pdf/top.pdf

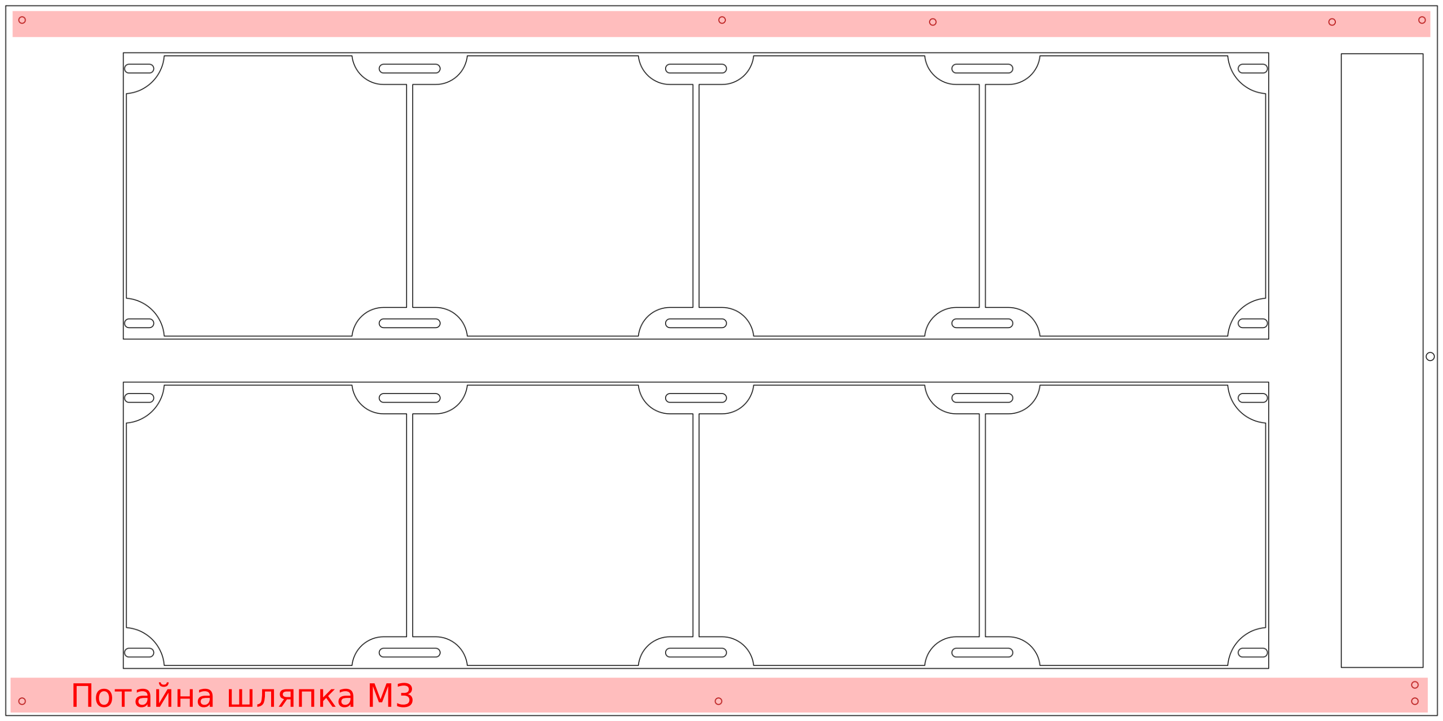
[picture p98: page 1]

Потайна шляпка М3
