nazar-pc/NPW-1.0/initial-build-pictures/IMG_20191107_225444.jpg

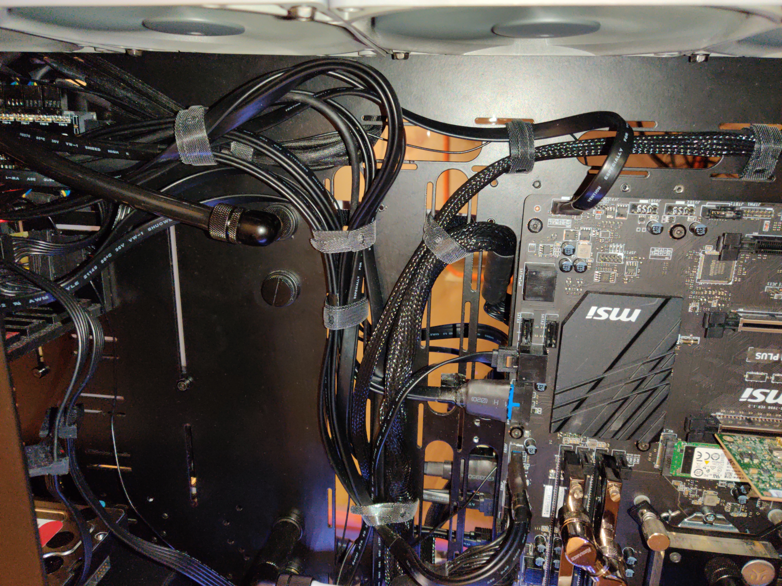
initial-build-pictures/IMG_20191107_225444.jpg
