nazar-pc/NPW-1.0/initial-build-pictures/IMG_20191107_230017.jpg

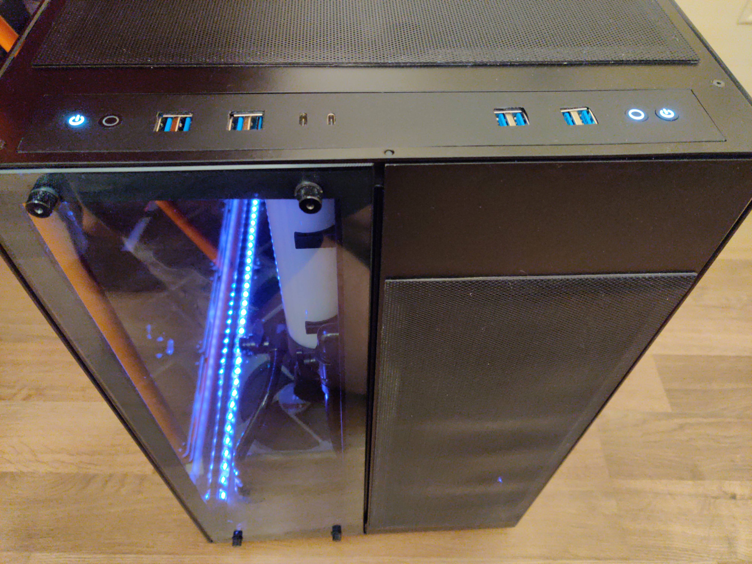
initial-build-pictures/IMG_20191107_230017.jpg
