nazar-pc/NPW-1.0/manufacturing/random-stuff/Assembly.SLDASM.png

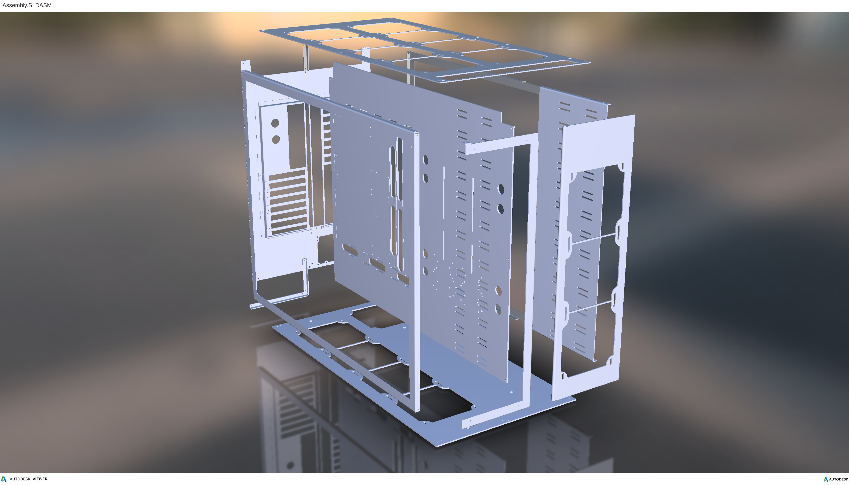
manufacturing/random-stuff/Assembly.SLDASM.png
