nazar-pc/NPW-1.0/manufacturing/random-stuff/Dual MB PC Case - sheet metal/Screenshots/2018-10-27_163635.png

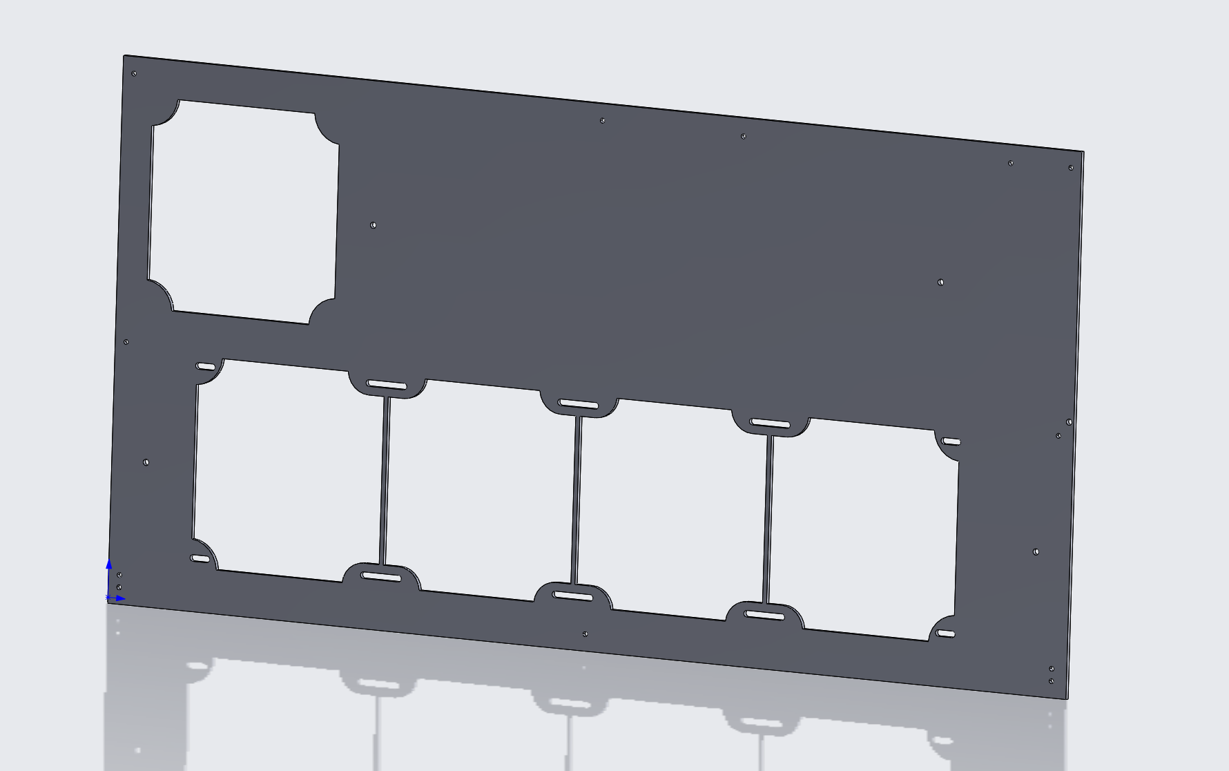
manufacturing/random-stuff/Dual MB PC Case - sheet metal/Screenshots/2018-10-27_163635.png
