nazar-pc/NPW-1.0/manufacturing/random-stuff/DualMB sheet metal drawings 2019.01.16.PDF

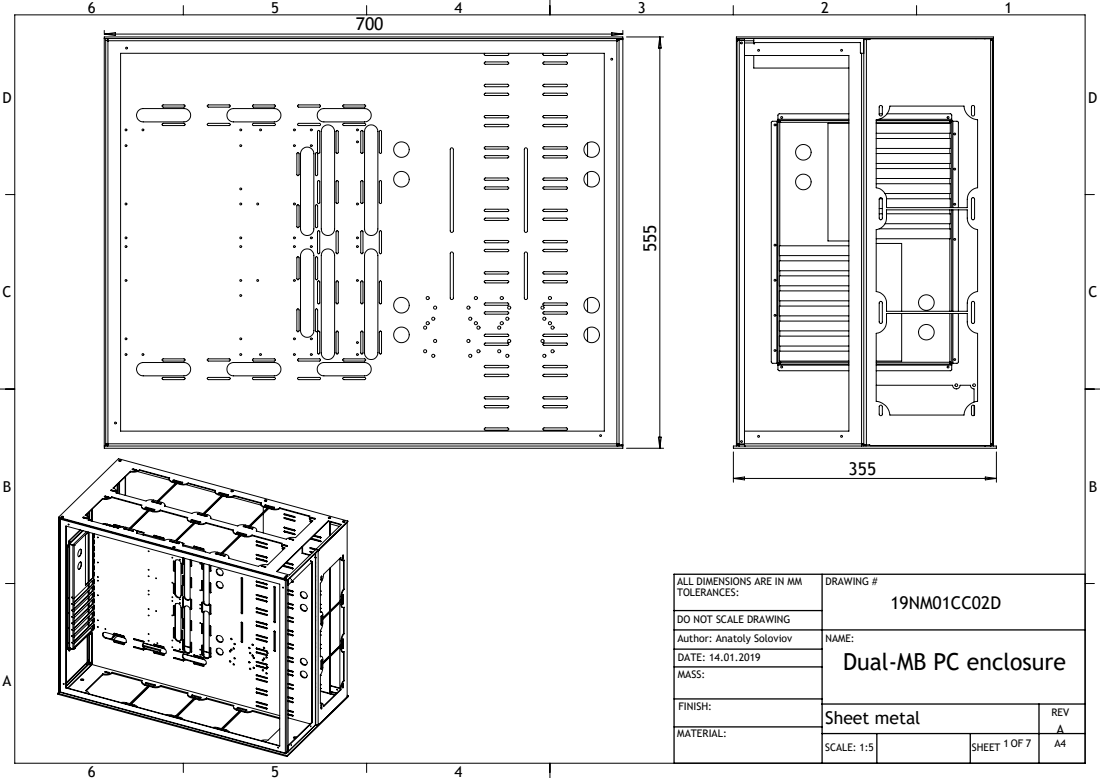
[picture p136: page 1]
SCALE: 1:5; SHEET; Sheet metal

ALL DIMENSIONS ARE IN MM
TOLERANCES:

DRAWING #
Dual-MB PC enclosure

DO NOT SCALE DRAWING
Author: Anatoly Soloviov
DATE: 14.01.2019
MASS:

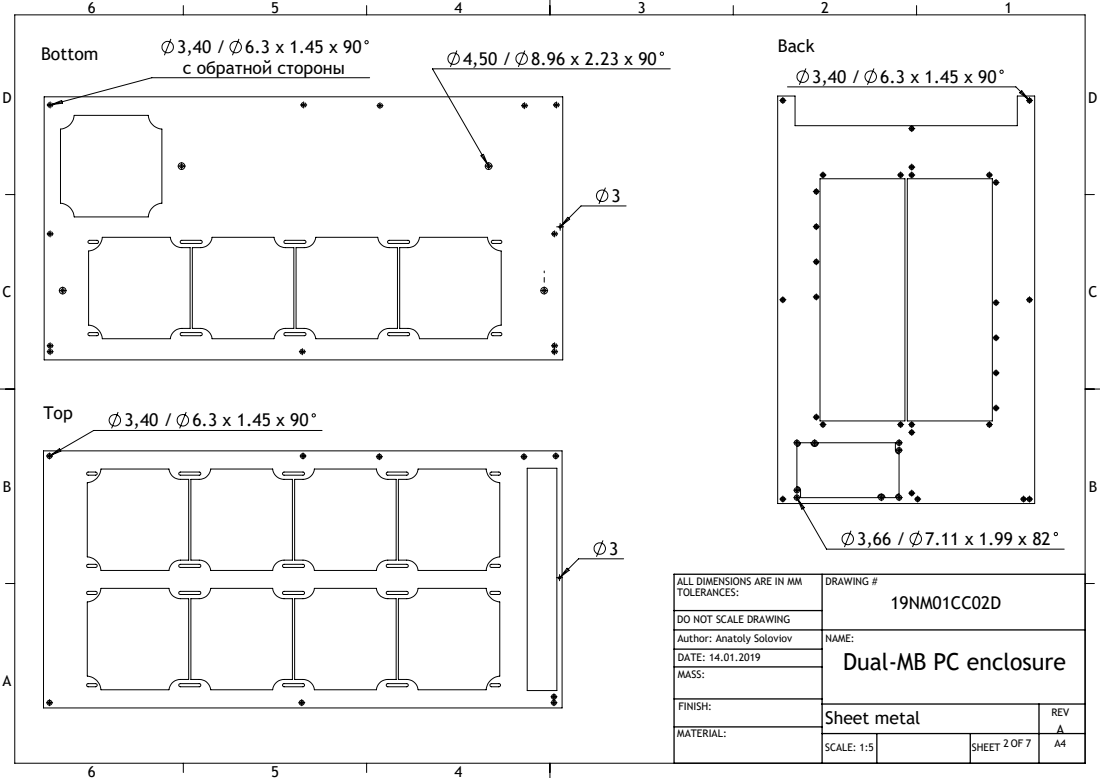
[picture p137: page 2]
Back; с обратной стороны; Sheet metal

ALL DIMENSIONS ARE IN MM
TOLERANCES:

DRAWING #
Dual-MB PC enclosure

DO NOT SCALE DRAWING
Author: Anatoly Soloviov
DATE: 14.01.2019
MASS:

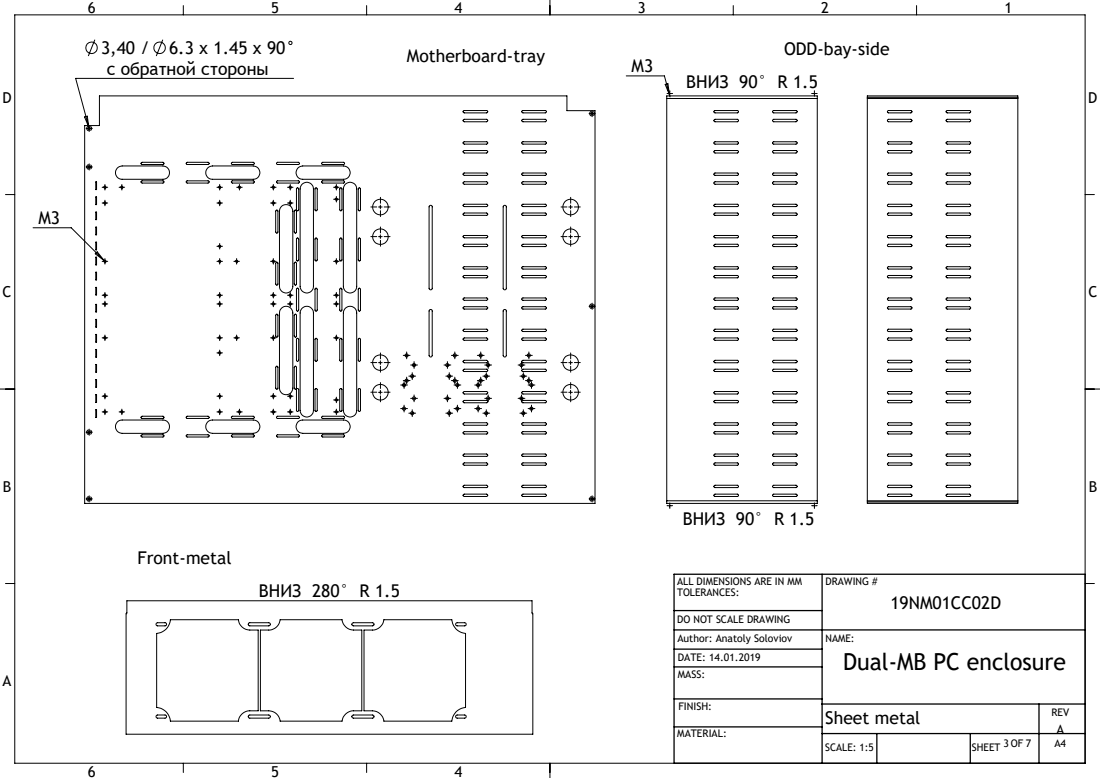
[picture p138: page 3]
3,40 / 6.3 х 1.45 x 90 с обратной стороны; ВНИЗ 280° R 1.5; ВНИЗ 90° R 1.5; Sheet metal

ODD-bay-side

ALL DIMENSIONS ARE IN MM
TOLERANCES:

DRAWING #
Dual-MB PC enclosure

DO NOT SCALE DRAWING
Author: Anatoly Soloviov
DATE: 14.01.2019
MASS:

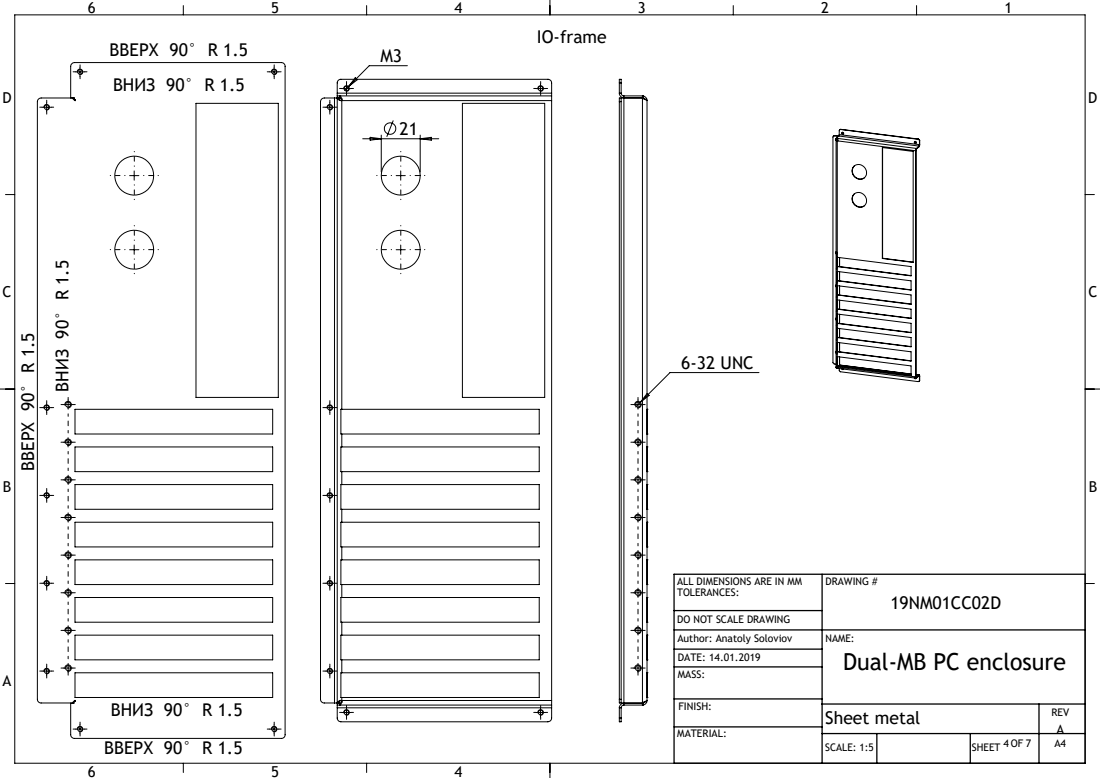
[picture p139: page 4]
ВВЕРХ 90° R 1.5; ВНИЗ 90° R 1.5; 6-32 UNC; Sheet metal

ALL DIMENSIONS ARE IN MM
TOLERANCES:

DRAWING #
Dual-MB PC enclosure

DO NOT SCALE DRAWING
Author: Anatoly Soloviov
DATE: 14.01.2019
MASS:

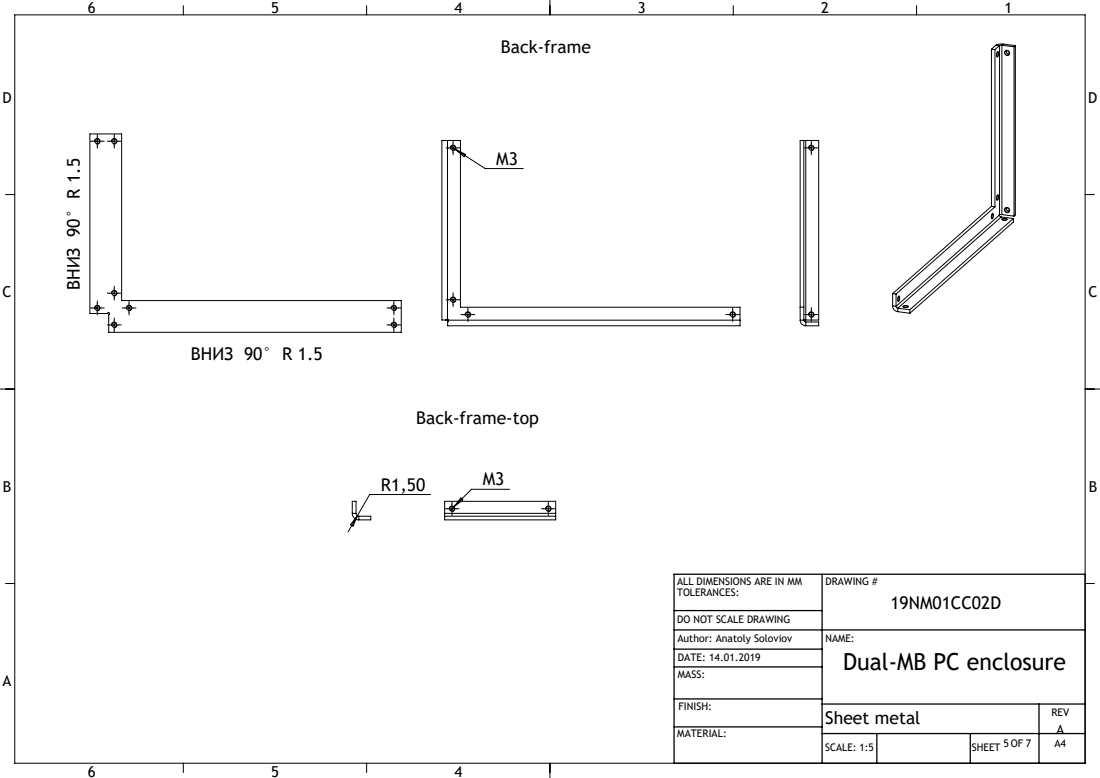
[picture p140: page 5]
ВНИЗ 90° R 1.5; Sheet metal

Back-frame-top

ALL DIMENSIONS ARE IN MM
TOLERANCES:

DRAWING #
Dual-MB PC enclosure

DO NOT SCALE DRAWING
Author: Anatoly Soloviov
DATE: 14.01.2019
MASS:

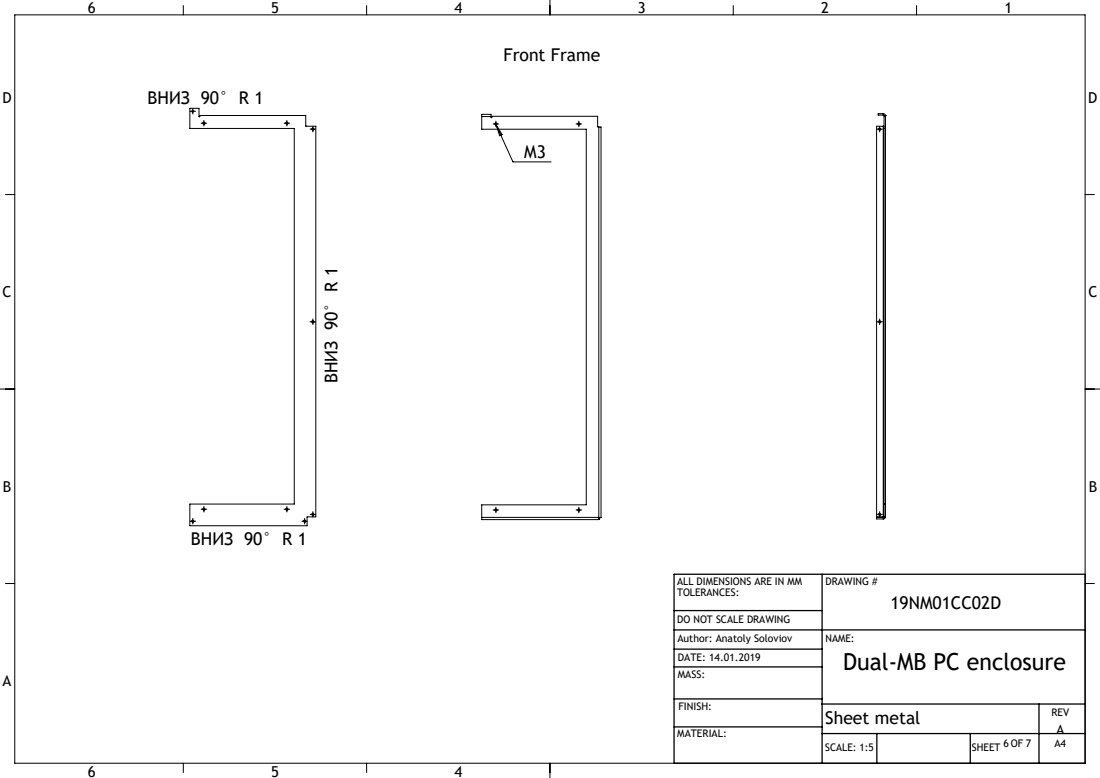
[picture p141: page 6]
ВНИЗ 90° R 1; Front Frame; Sheet metal

ALL DIMENSIONS ARE IN MM
TOLERANCES:

DRAWING #
Dual-MB PC enclosure

DO NOT SCALE DRAWING
Author: Anatoly Soloviov
DATE: 14.01.2019
MASS:

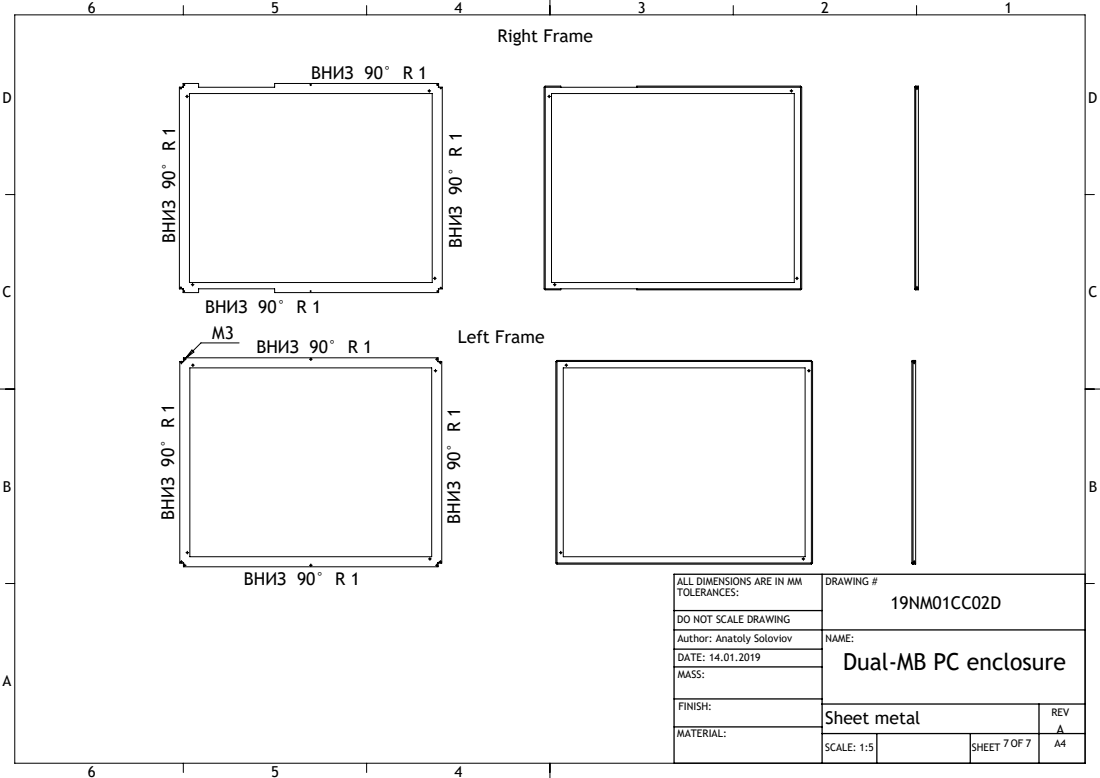
[picture p142: page 7]
ВНИЗ 90° R 1; Right Frame; Left Frame; Sheet metal

ALL DIMENSIONS ARE IN MM
TOLERANCES:

DRAWING #
Dual-MB PC enclosure

DO NOT SCALE DRAWING
Author: Anatoly Soloviov
DATE: 14.01.2019
MASS:
