nazar-pc/NPW-1.0/manufacturing/random-stuff/DualMB sheet metal drawings 2019.01.30.PDF

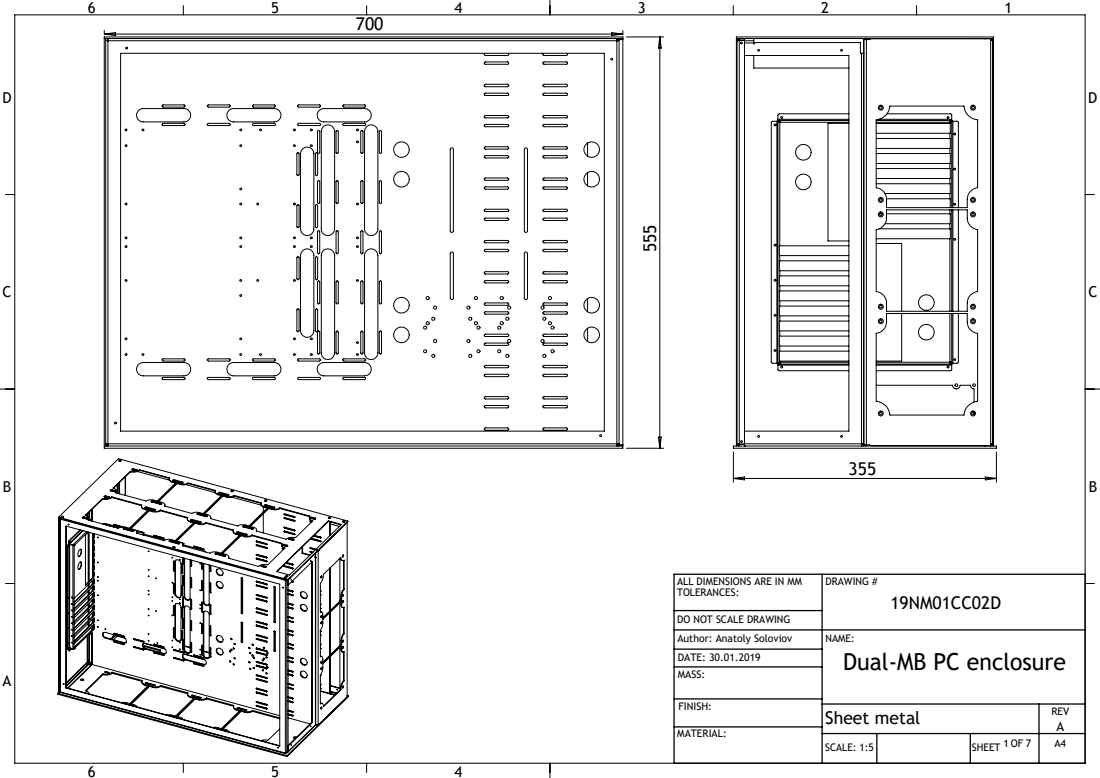
[picture p143: page 1]

ALL DIMENSIONS ARE IN MM
TOLERANCES:

DRAWING #
Dual-MB PC enclosure

DO NOT SCALE DRAWING
Author: Anatoly Soloviov
DATE: 30.01.2019
MASS:

Sheet metal | REV A MATERIAL:

SCALE: 1:5 | | 1 OF 7 SHEET | A4

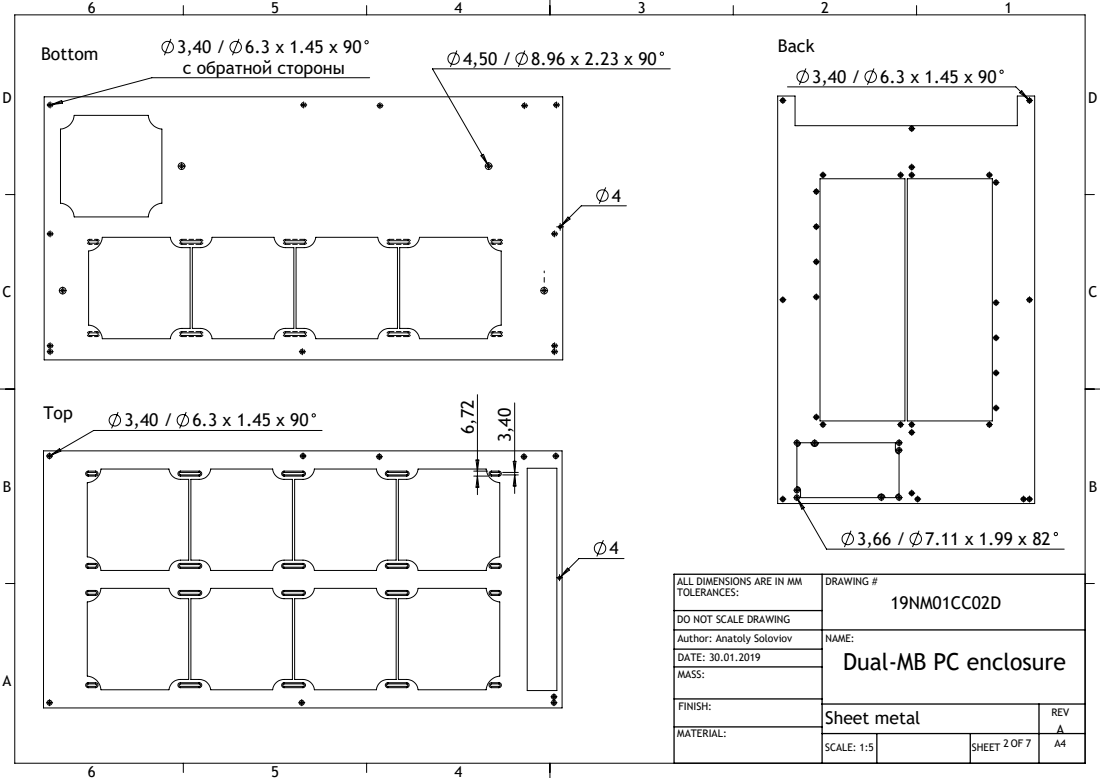
[picture p144: page 2]
Back; с обратной стороны; Sheet metal

ALL DIMENSIONS ARE IN MM
TOLERANCES:

DRAWING #
Dual-MB PC enclosure

DO NOT SCALE DRAWING
Author: Anatoly Soloviov
DATE: 30.01.2019
MASS:

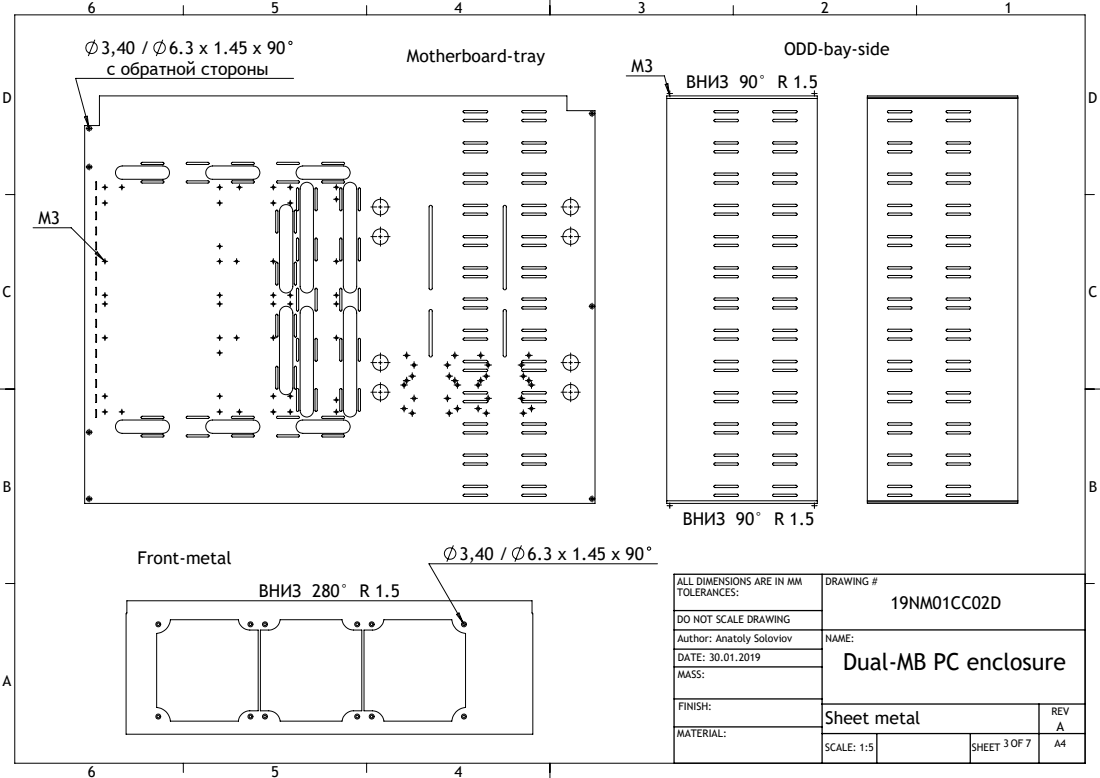
[picture p145: page 3]
3,40 / 6.3 х 1.45 x 90 с обратной стороны; ВНИЗ 280° R 1.5; ВНИЗ 90° R 1.5; Sheet metal

ODD-bay-side

ALL DIMENSIONS ARE IN MM
TOLERANCES:

DRAWING #
Dual-MB PC enclosure

DO NOT SCALE DRAWING
Author: Anatoly Soloviov
DATE: 30.01.2019
MASS:

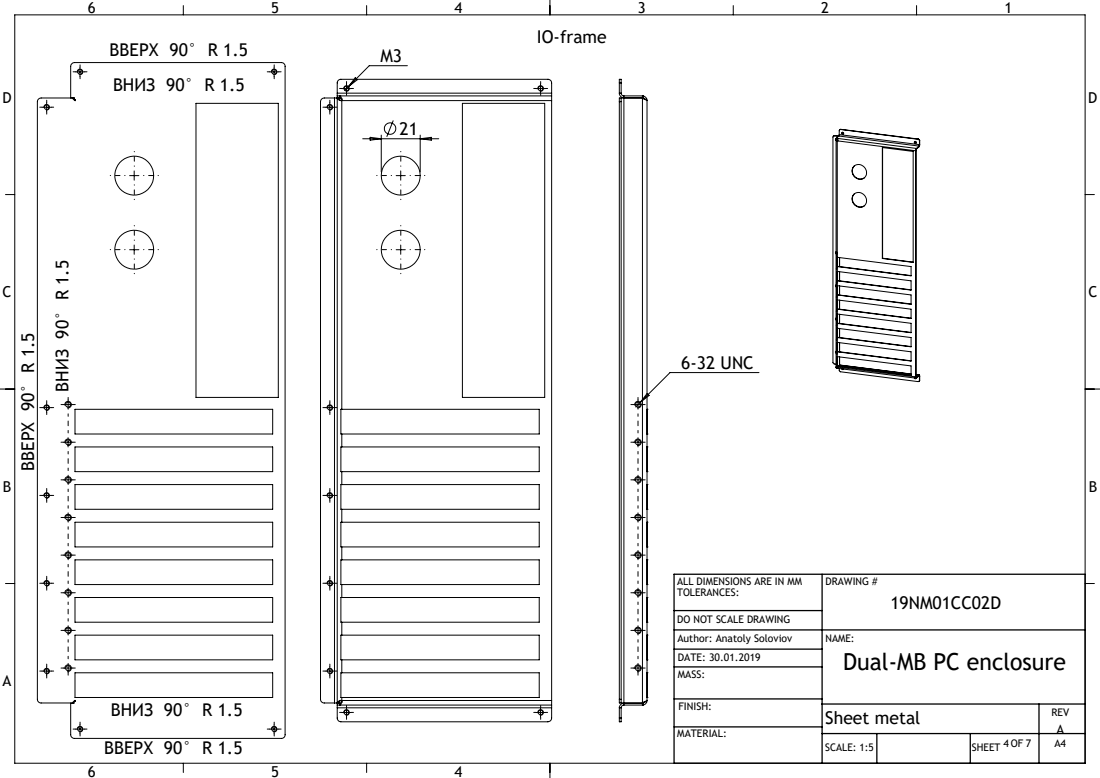
[picture p146: page 4]
ВВЕРХ 90° R 1.5; ВНИЗ 90° R 1.5; 6-32 UNC; Sheet metal

ALL DIMENSIONS ARE IN MM
TOLERANCES:

DRAWING #
Dual-MB PC enclosure

DO NOT SCALE DRAWING
Author: Anatoly Soloviov
DATE: 30.01.2019
MASS:

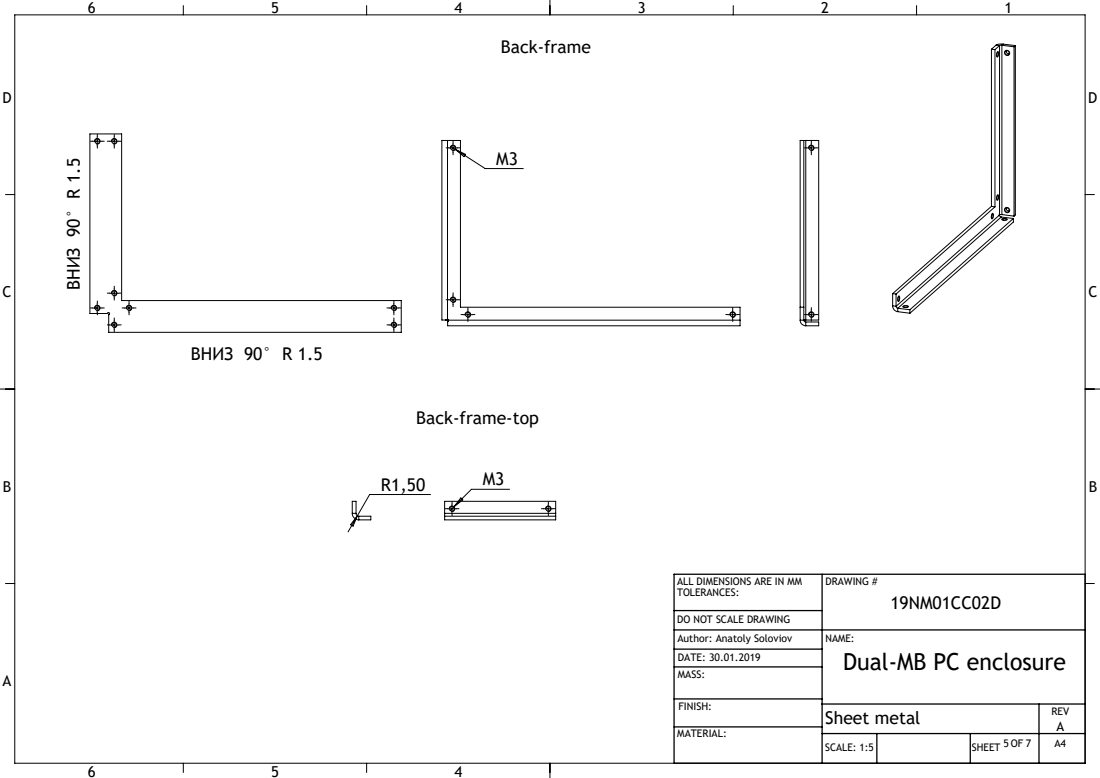
[picture p147: page 5]
ВНИЗ 90° R 1.5; Sheet metal

Back-frame-top

ALL DIMENSIONS ARE IN MM
TOLERANCES:

DRAWING #
Dual-MB PC enclosure

DO NOT SCALE DRAWING
Author: Anatoly Soloviov
DATE: 30.01.2019
MASS:

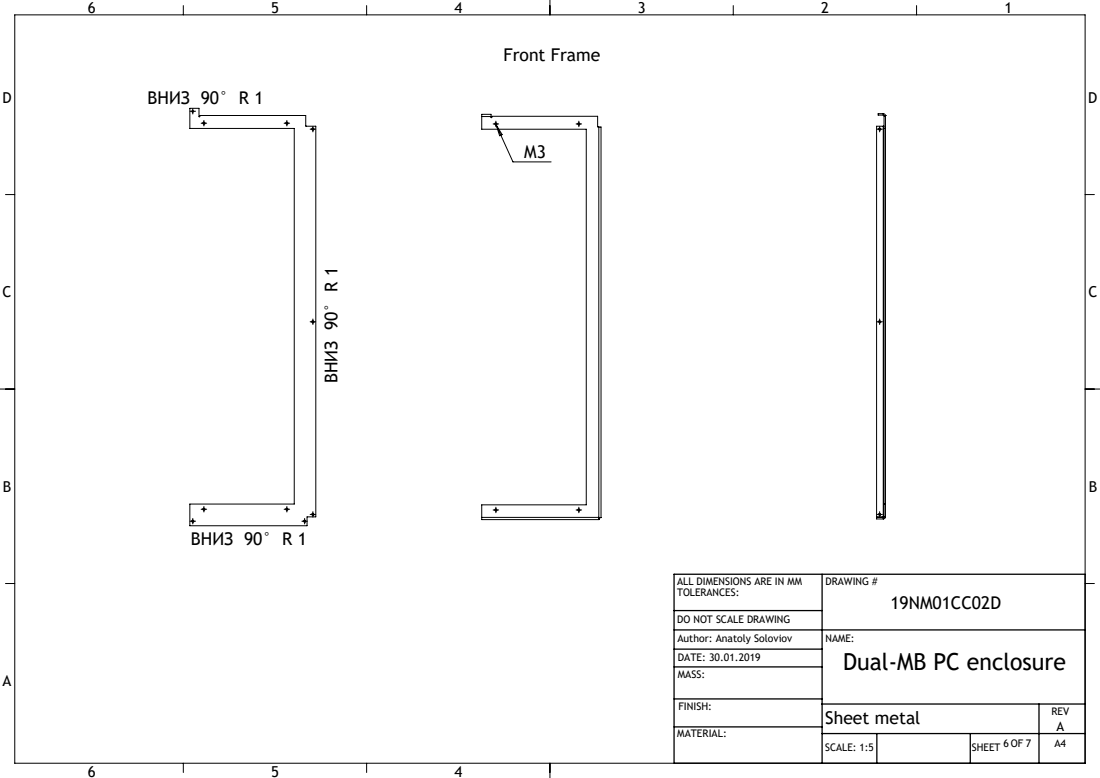
[picture p148: page 6]
ВНИЗ 90° R 1; Front Frame; Sheet metal

ALL DIMENSIONS ARE IN MM
TOLERANCES:

DRAWING #
Dual-MB PC enclosure

DO NOT SCALE DRAWING
Author: Anatoly Soloviov
DATE: 30.01.2019
MASS:

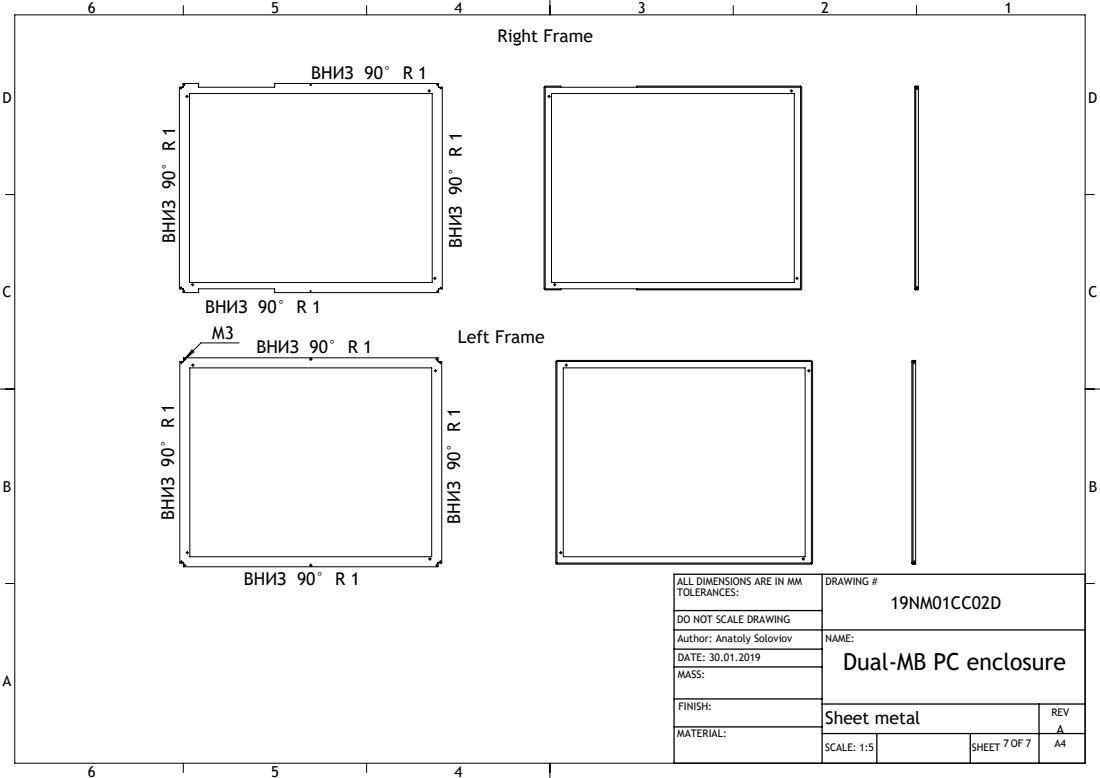
[picture p149: page 7]
ВНИЗ 90° R 1; Right Frame; Left Frame; Sheet metal

ALL DIMENSIONS ARE IN MM
TOLERANCES:

DRAWING #
Dual-MB PC enclosure

DO NOT SCALE DRAWING
Author: Anatoly Soloviov
DATE: 30.01.2019
MASS:
