nazar-pc/NPW-1.0/manufacturing/random-stuff/front-metal.pdf

D | D

6

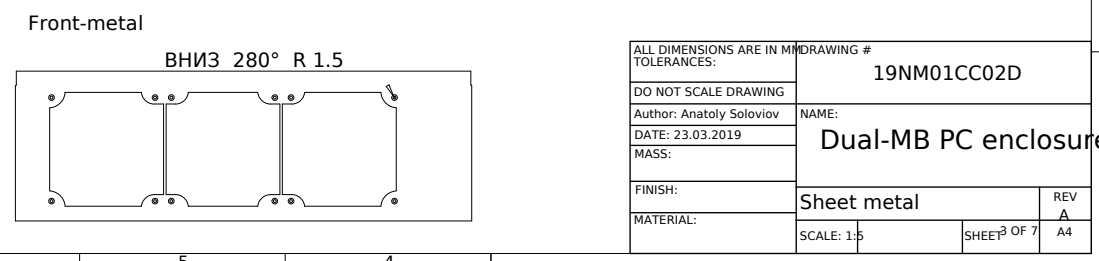
[picture p157: page 1]
ВНИЗ 280° R 1.5; Front-metal; SCALE: 1:5; SHEET; DRAWING #; REV; MATERIAL:; FINISH:; Sheet metal

ALL DIMENSIONS ARE IN MM
TOLERANCES:

DO NOT SCALE DRAWING
Author: Anatoly Soloviov
DATE: 23.03.2019
MASS:

NAME:
Dual-MB PC enclosure
