nazar-pc/NPW-1.0/manufacturing/random-stuff/left-frame-3d.pdf

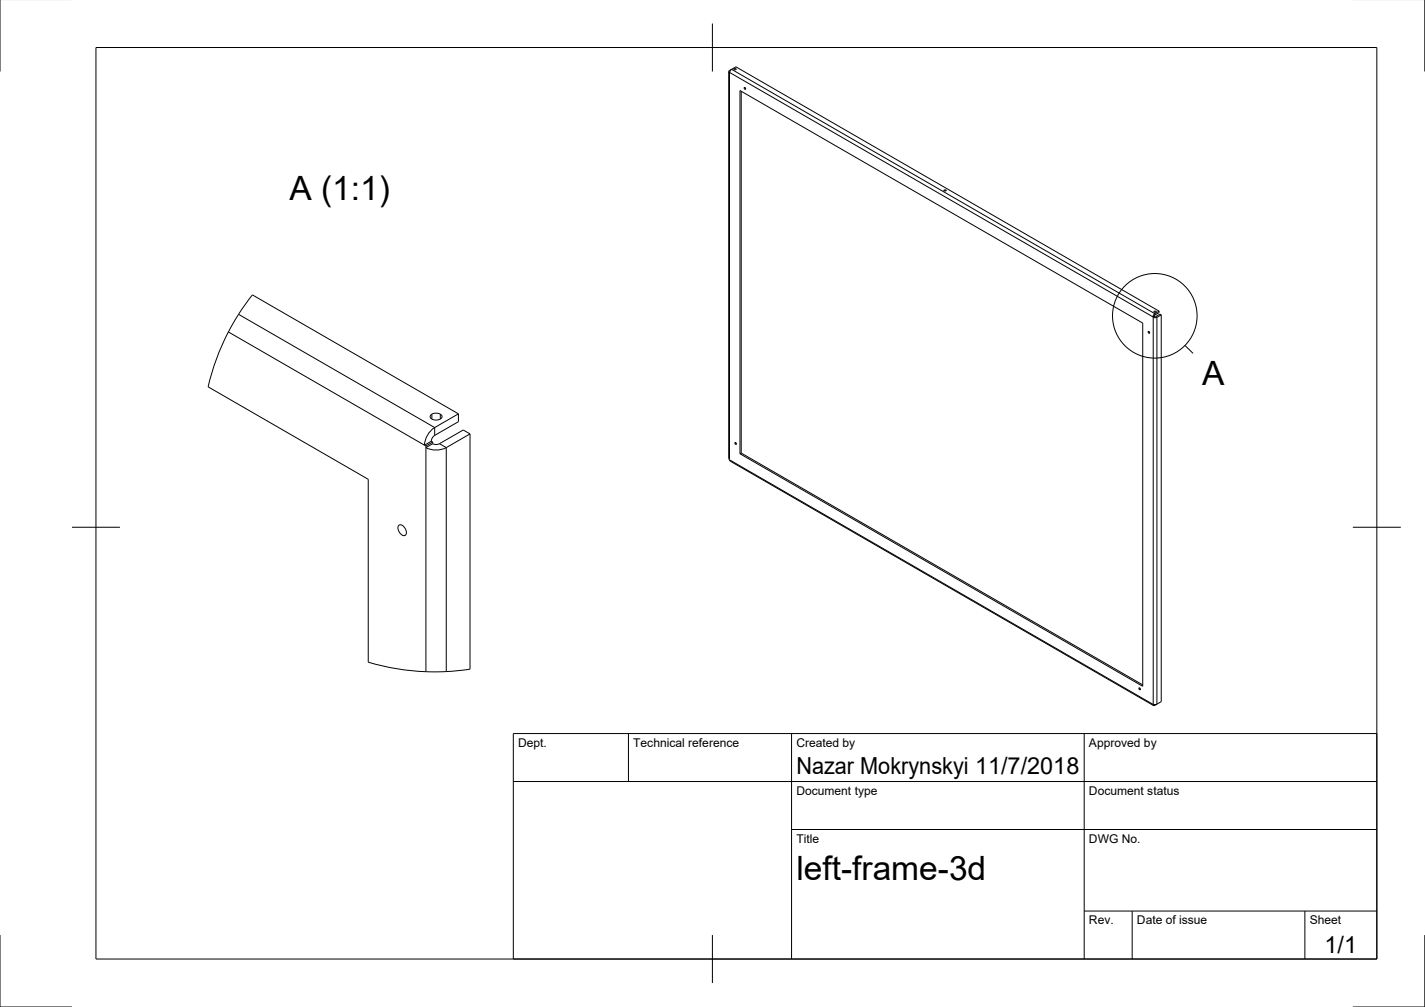
[picture p158: page 1]

Dept. | Technical reference | Created by Nazar Mokrynskyi 11/7/2018 | Approved by

Document type | Document status

Title left-frame-3d | DWG No.

Rev. | Date of issue | Sheet 1/1
