nazar-pc/NPW-1.0/manufacturing/random-stuff/left-frame.pdf

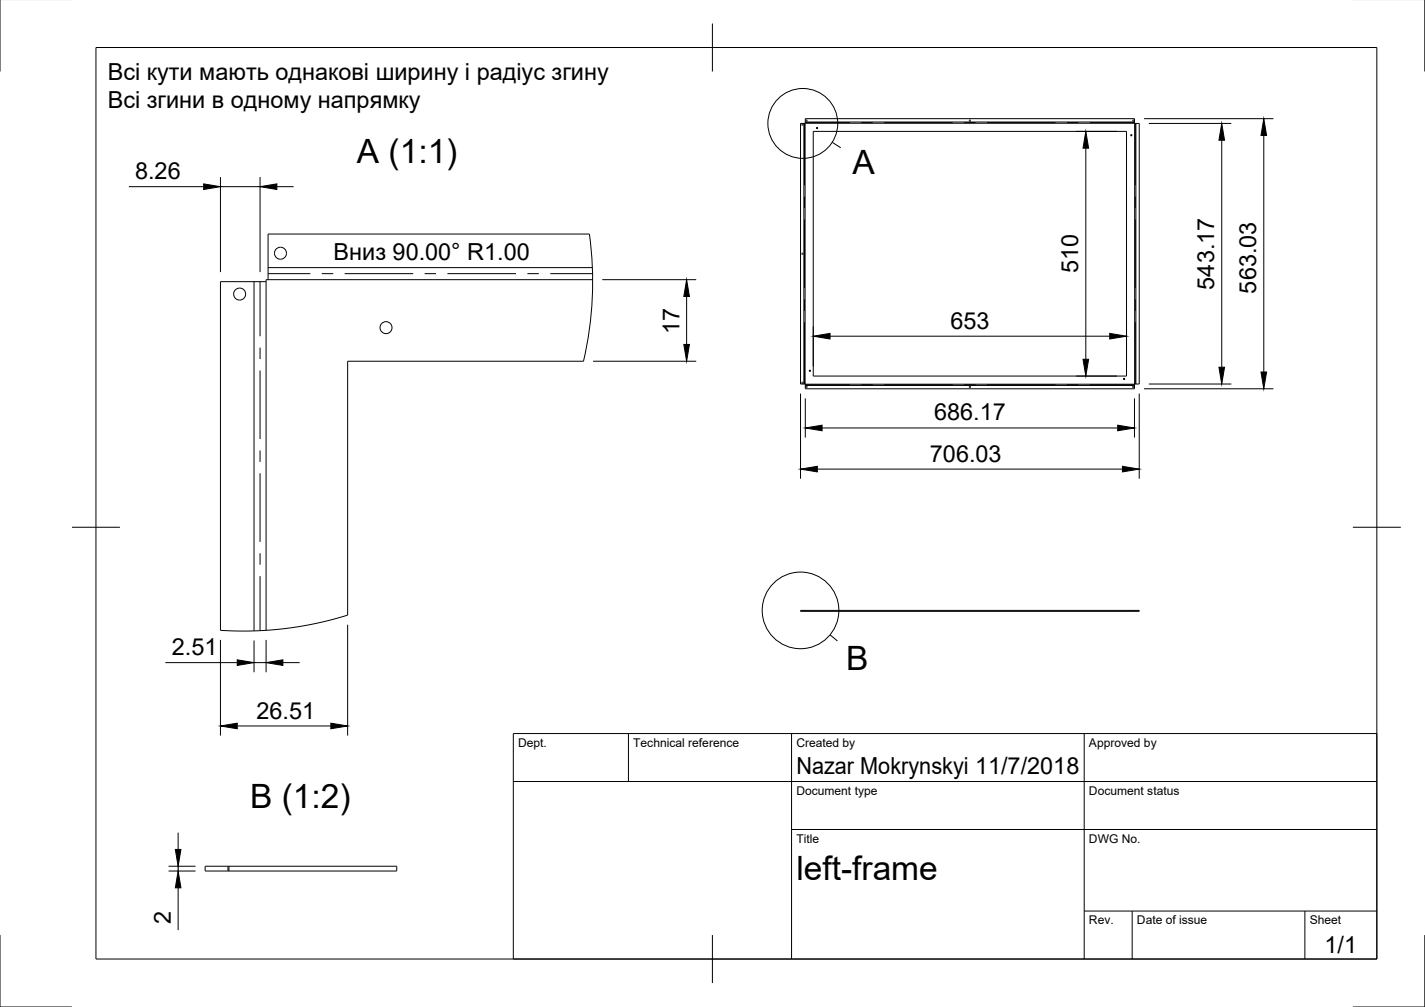
[picture p159: page 1]
543.17 Вниз 90.00° R1.00

Всі кути мають однакові ширину і радіус згину
Всі згини в одному напрямку

Dept. | Technical reference | Created by Nazar Mokrynskyi 11/7/2018 | Approved by

Document type | Document status

Title left-frame | DWG No.

Rev. | Date of issue | Sheet 1/1
