nazar-pc/NPW-1.0/manufacturing/random-stuff/3D convertion results/back-frame-top.pdf

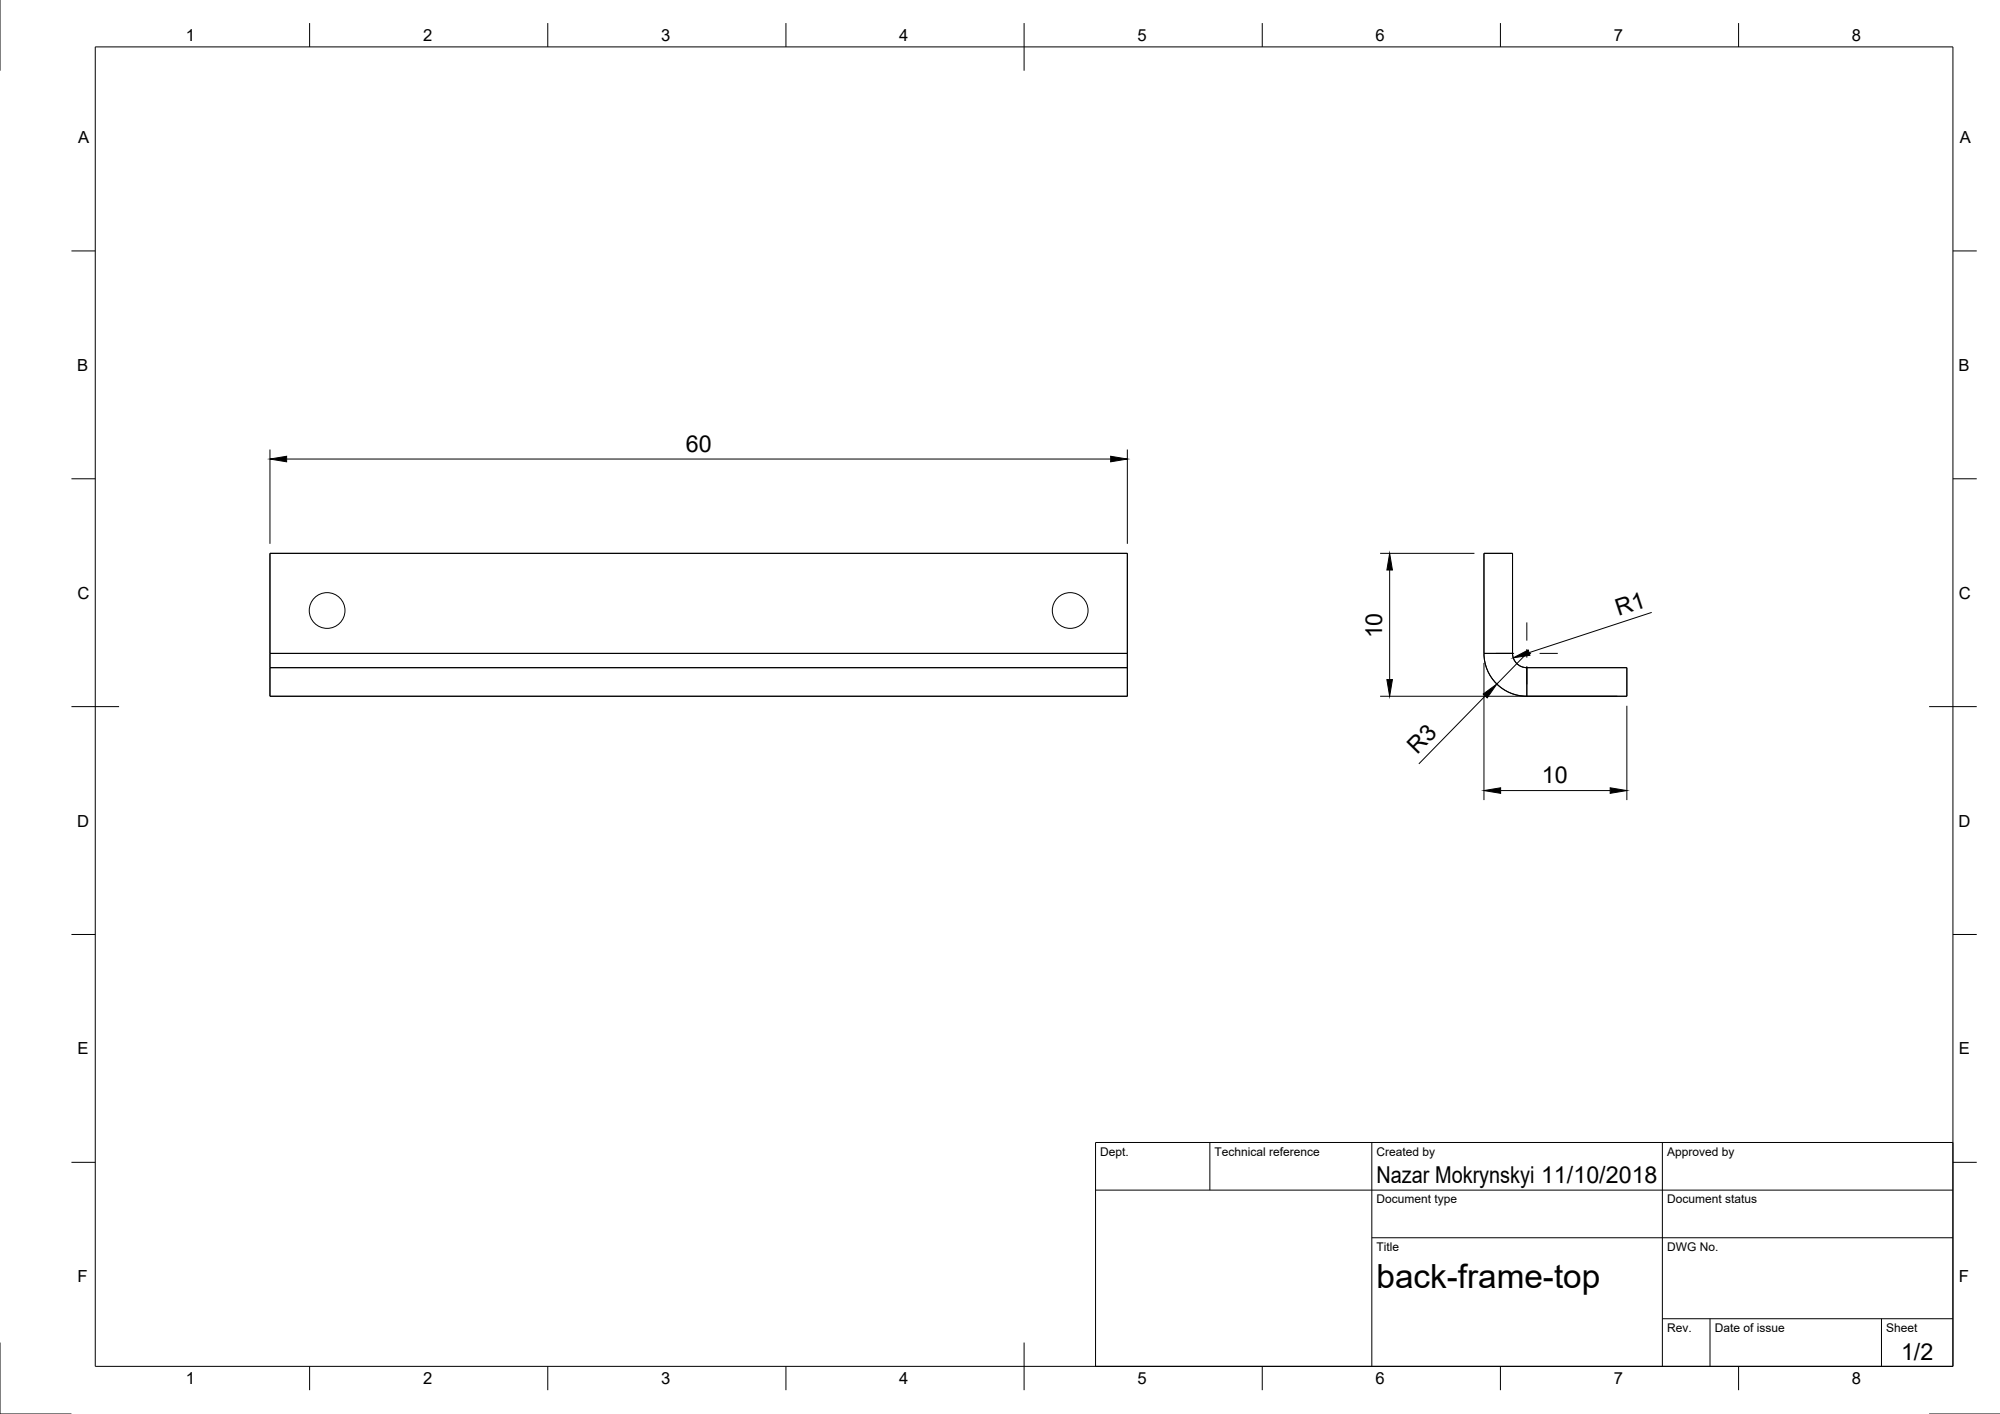
[picture p160: page 1]
Nazar Mokrynskyi 10

Dept. | Technical reference | Created by 11/10/2018 | Approved by

Document type | Document status

Title back-frame-top | DWG No.

Rev. | Date of issue | Sheet 1/2

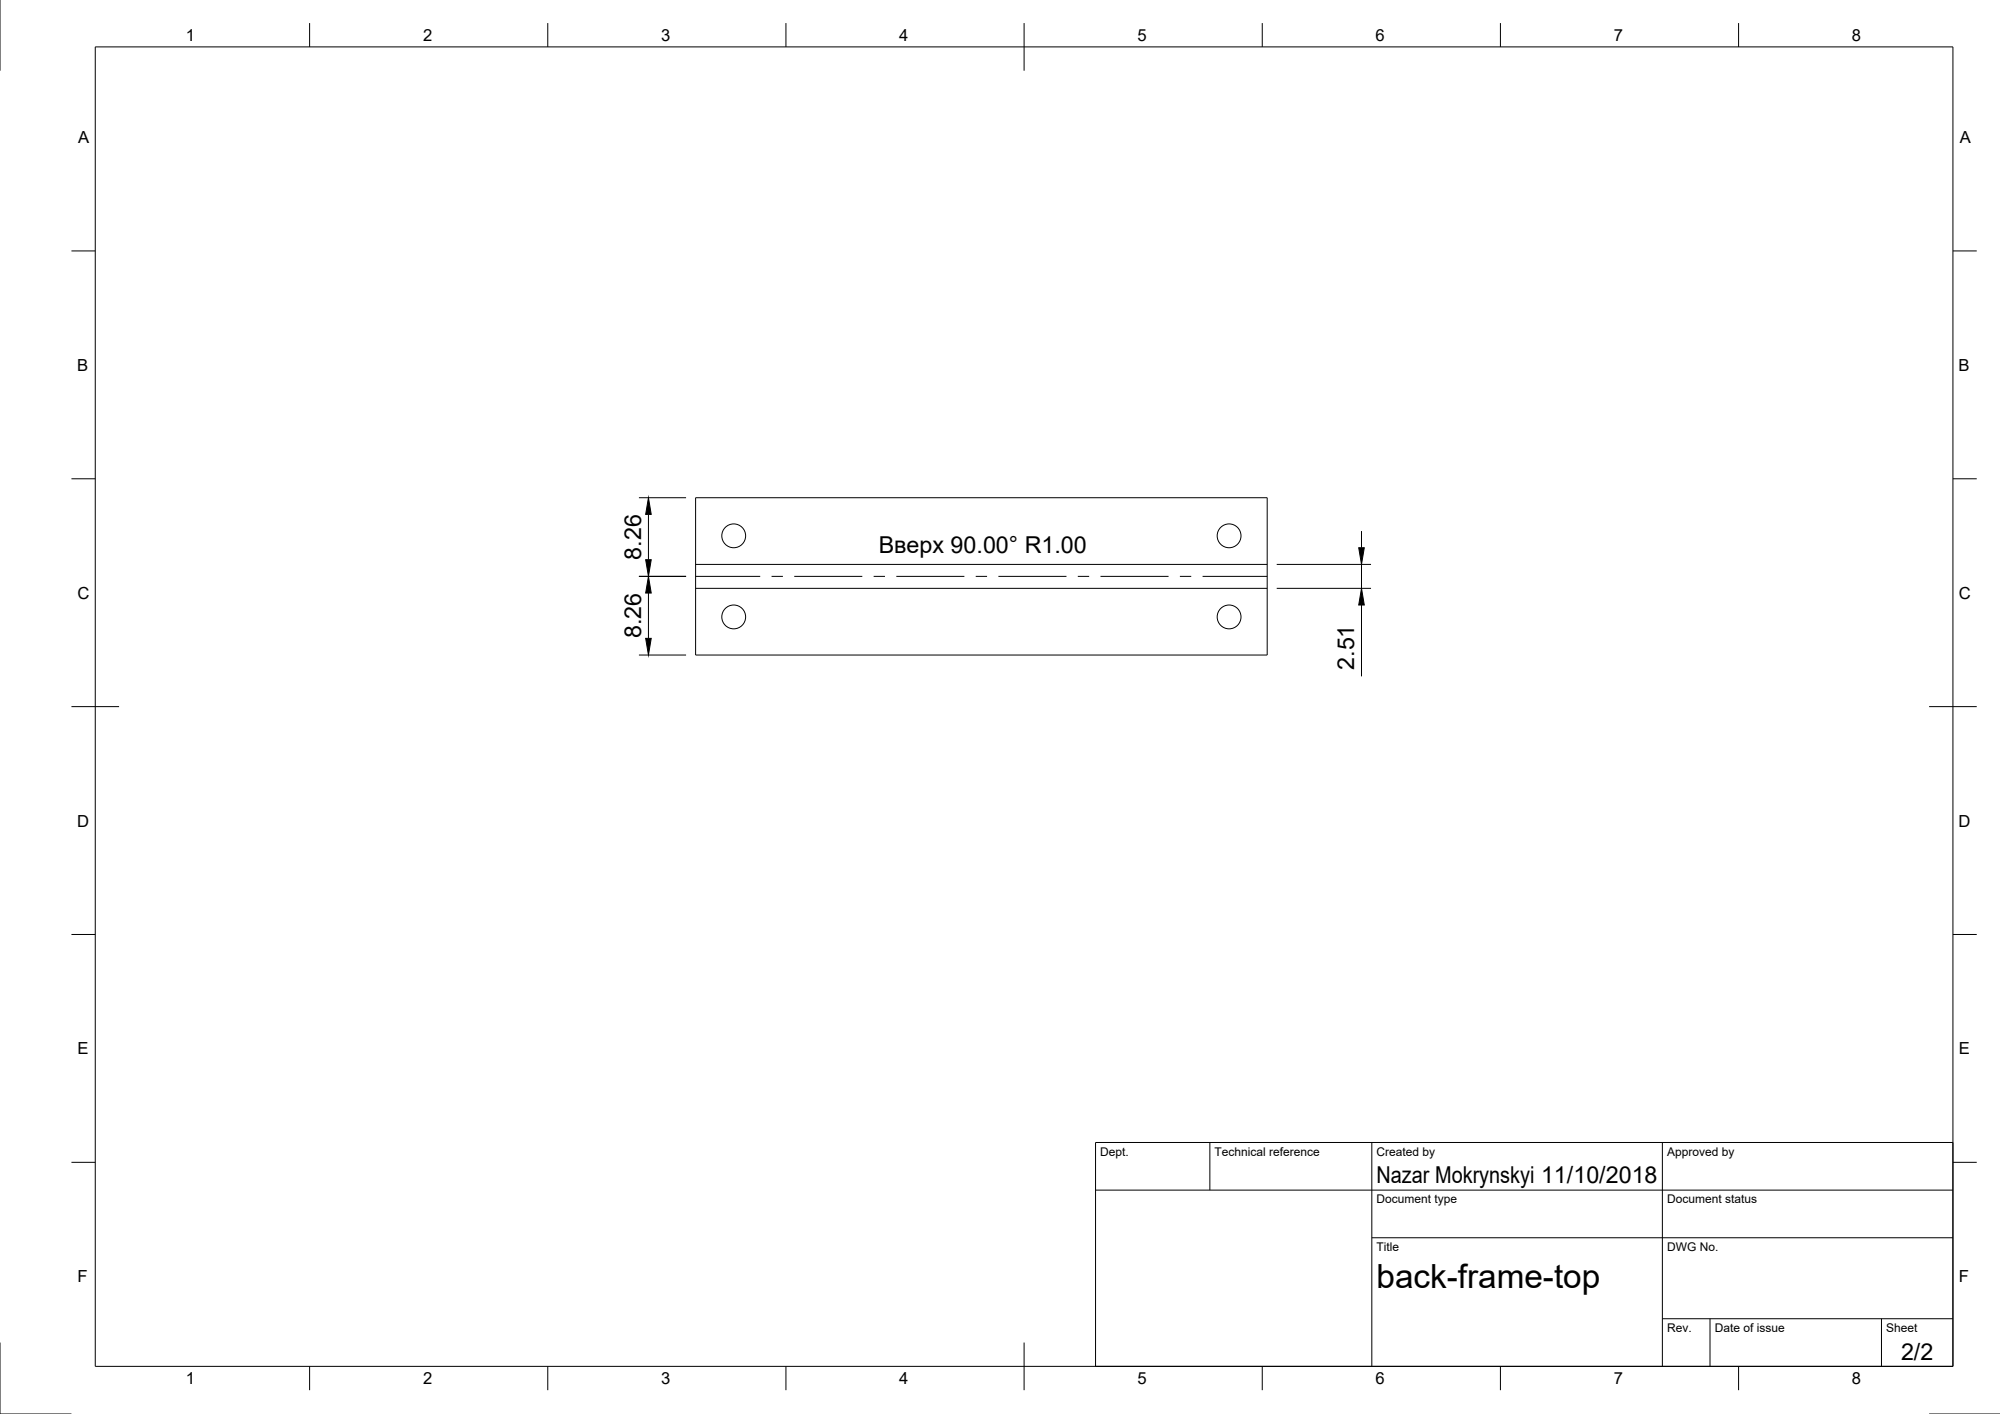
[picture p161: page 2]
Вверх 90.00° R1.00

Dept. | Technical reference | Created by Nazar Mokrynskyi 11/10/2018 | Approved by

Document type | Document status

Title back-frame-top | DWG No.

Rev. | Date of issue | Sheet 2/2
