nazar-pc/NPW-1.0/manufacturing/random-stuff/3D convertion results/main-frame.pdf

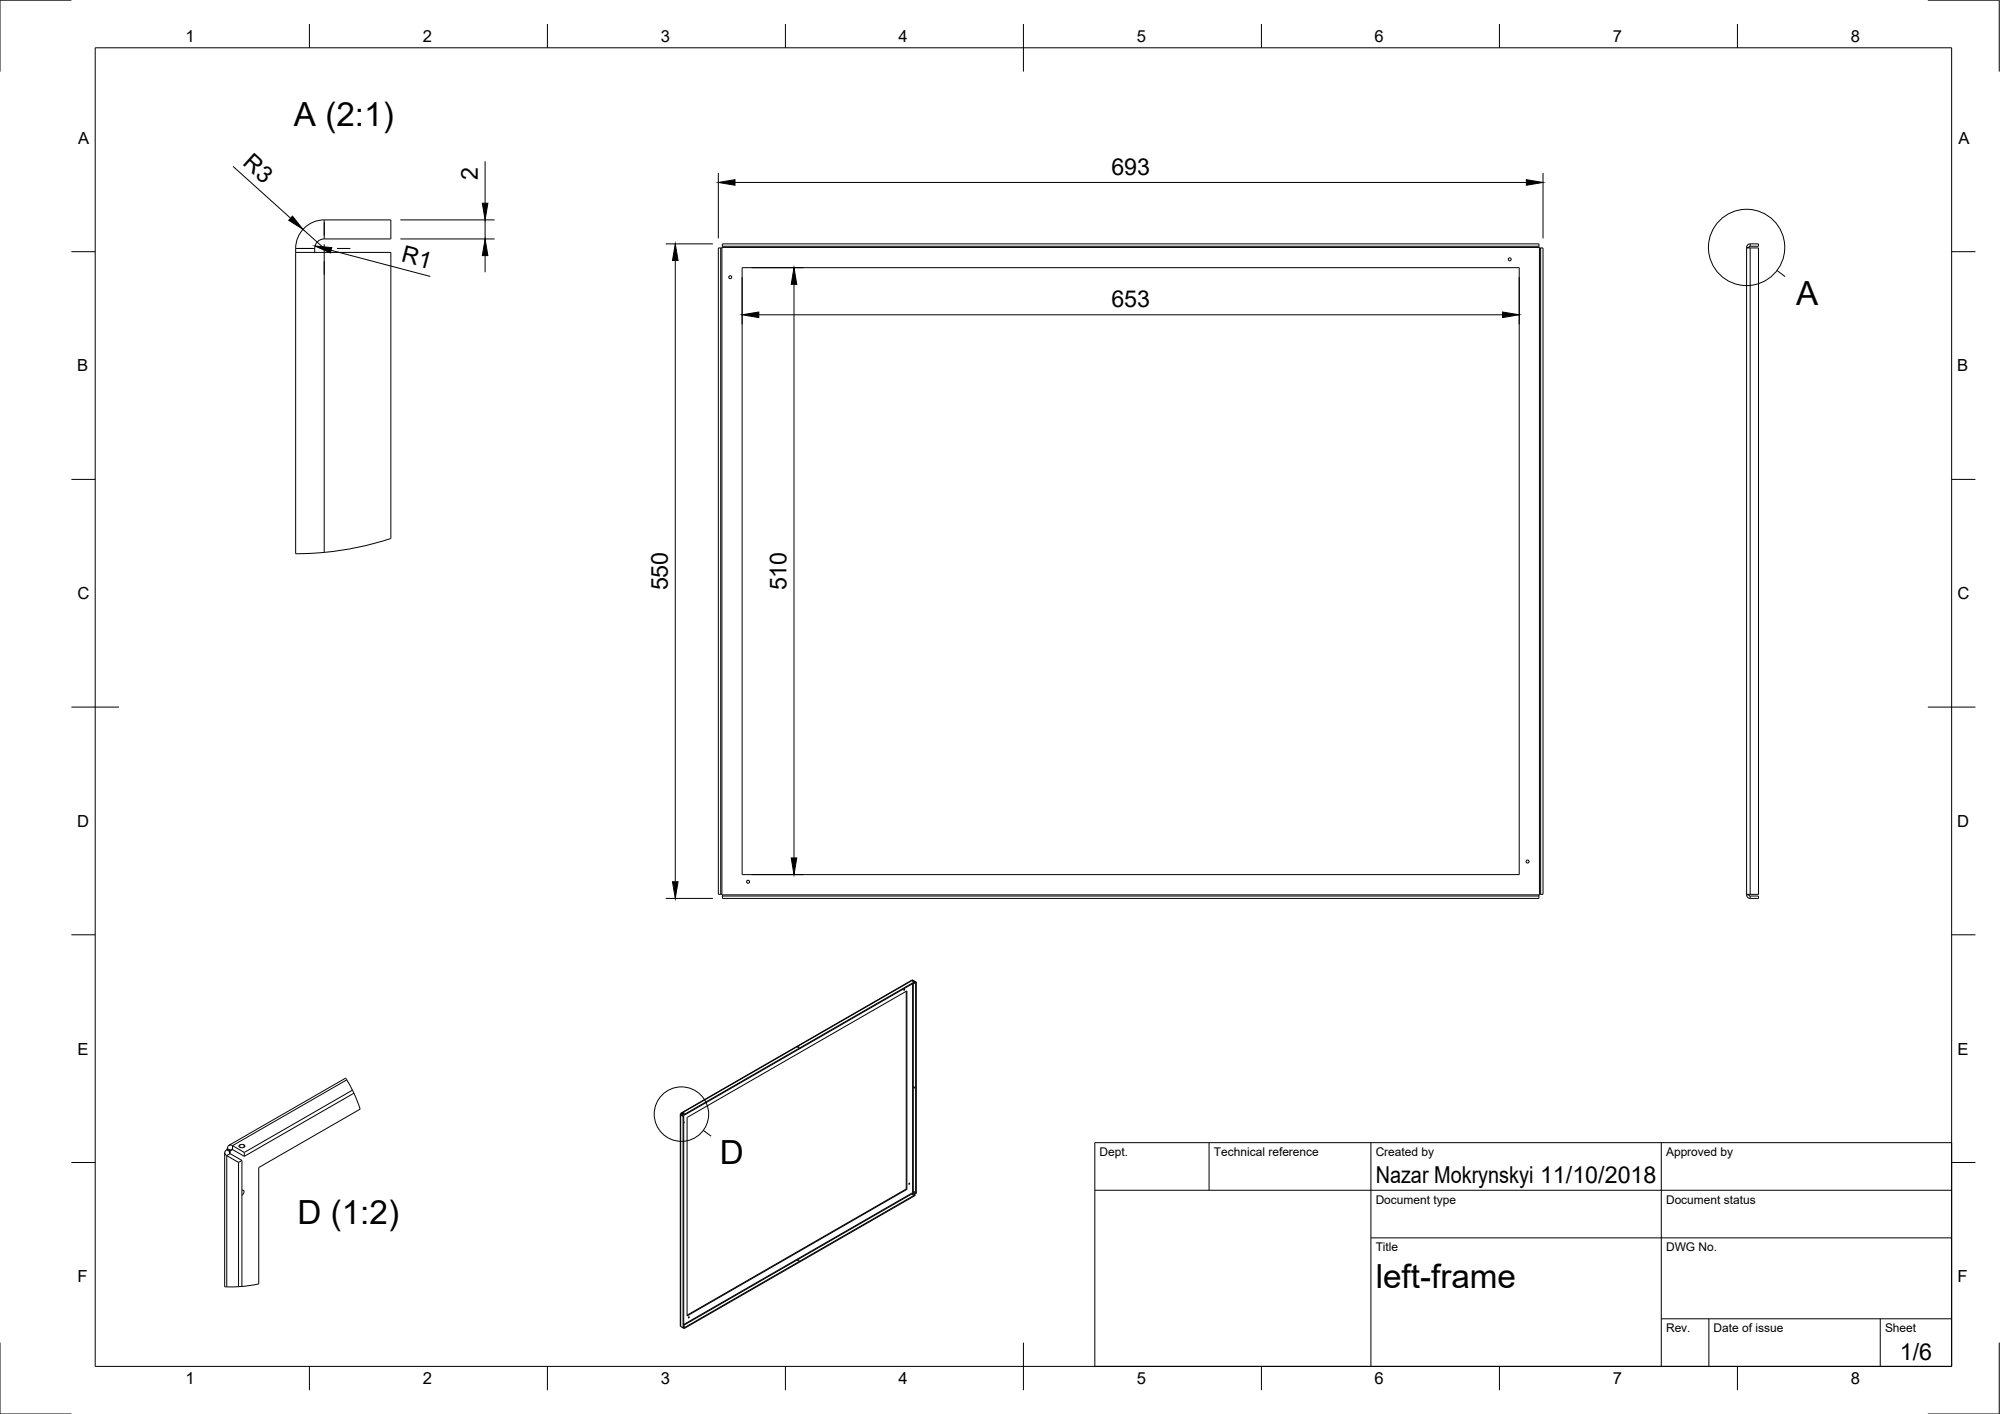
[picture p162: page 1]

Dept. | Technical reference | Created by Nazar Mokrynskyi 11/10/2018 | Approved by

Document type | Document status

Title left-frame | DWG No.

Rev. | Date of issue | Sheet

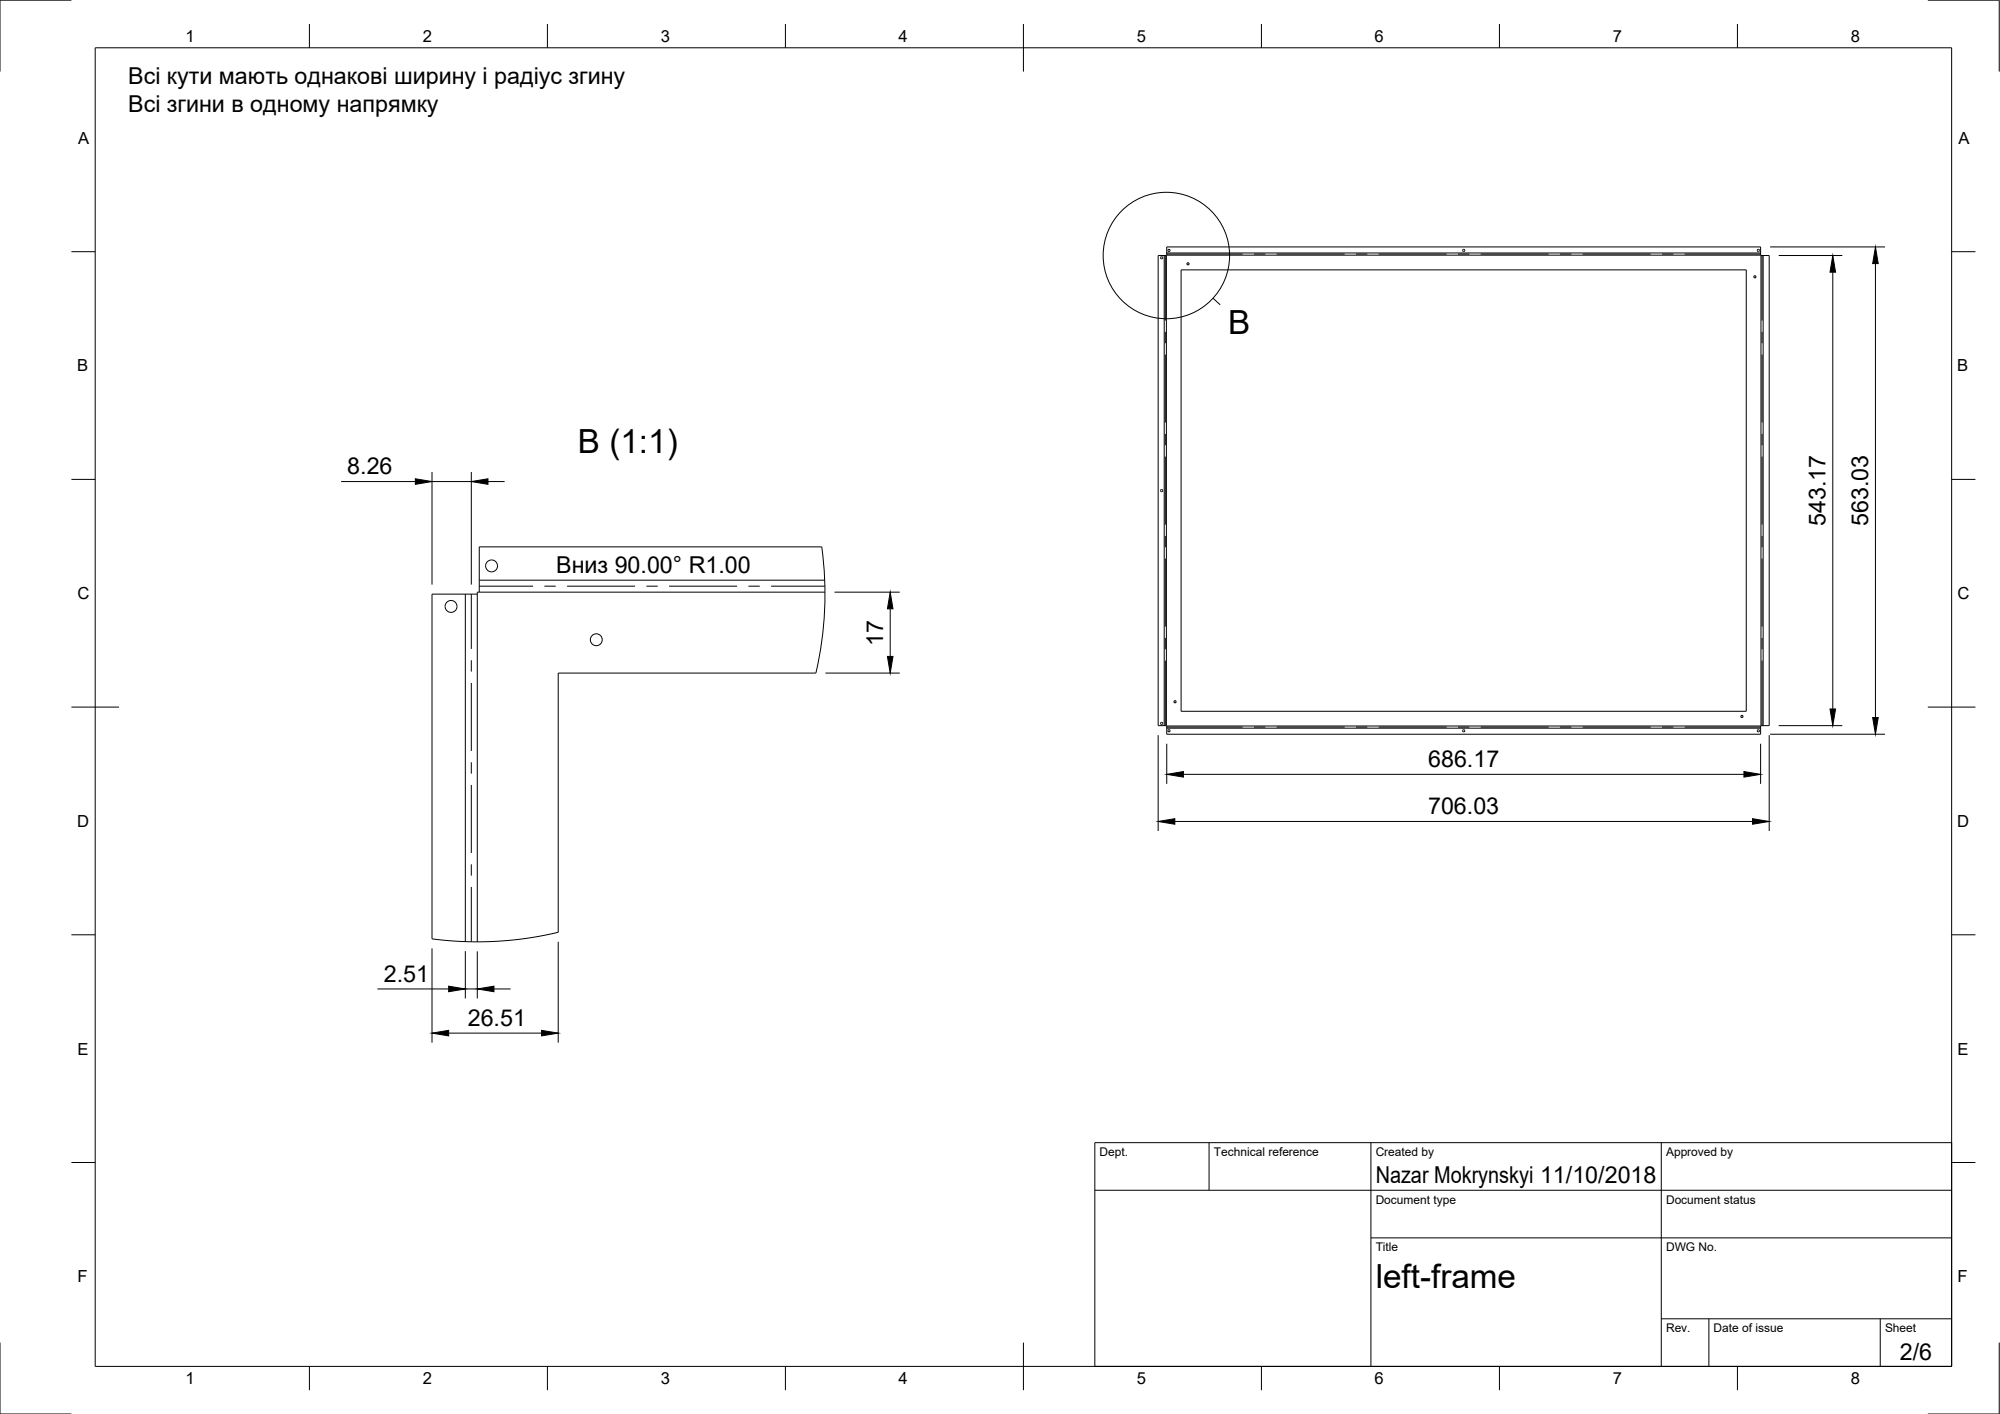
[picture p163: page 2]
Вниз 90.00° R1.00

Всі кути мають однакові ширину і радіус згину
Всі згини в одному напрямку

Dept. | Technical reference | Created by Nazar Mokrynskyi 11/10/2018 | Approved by

Document type | Document status

Title left-frame | DWG No.

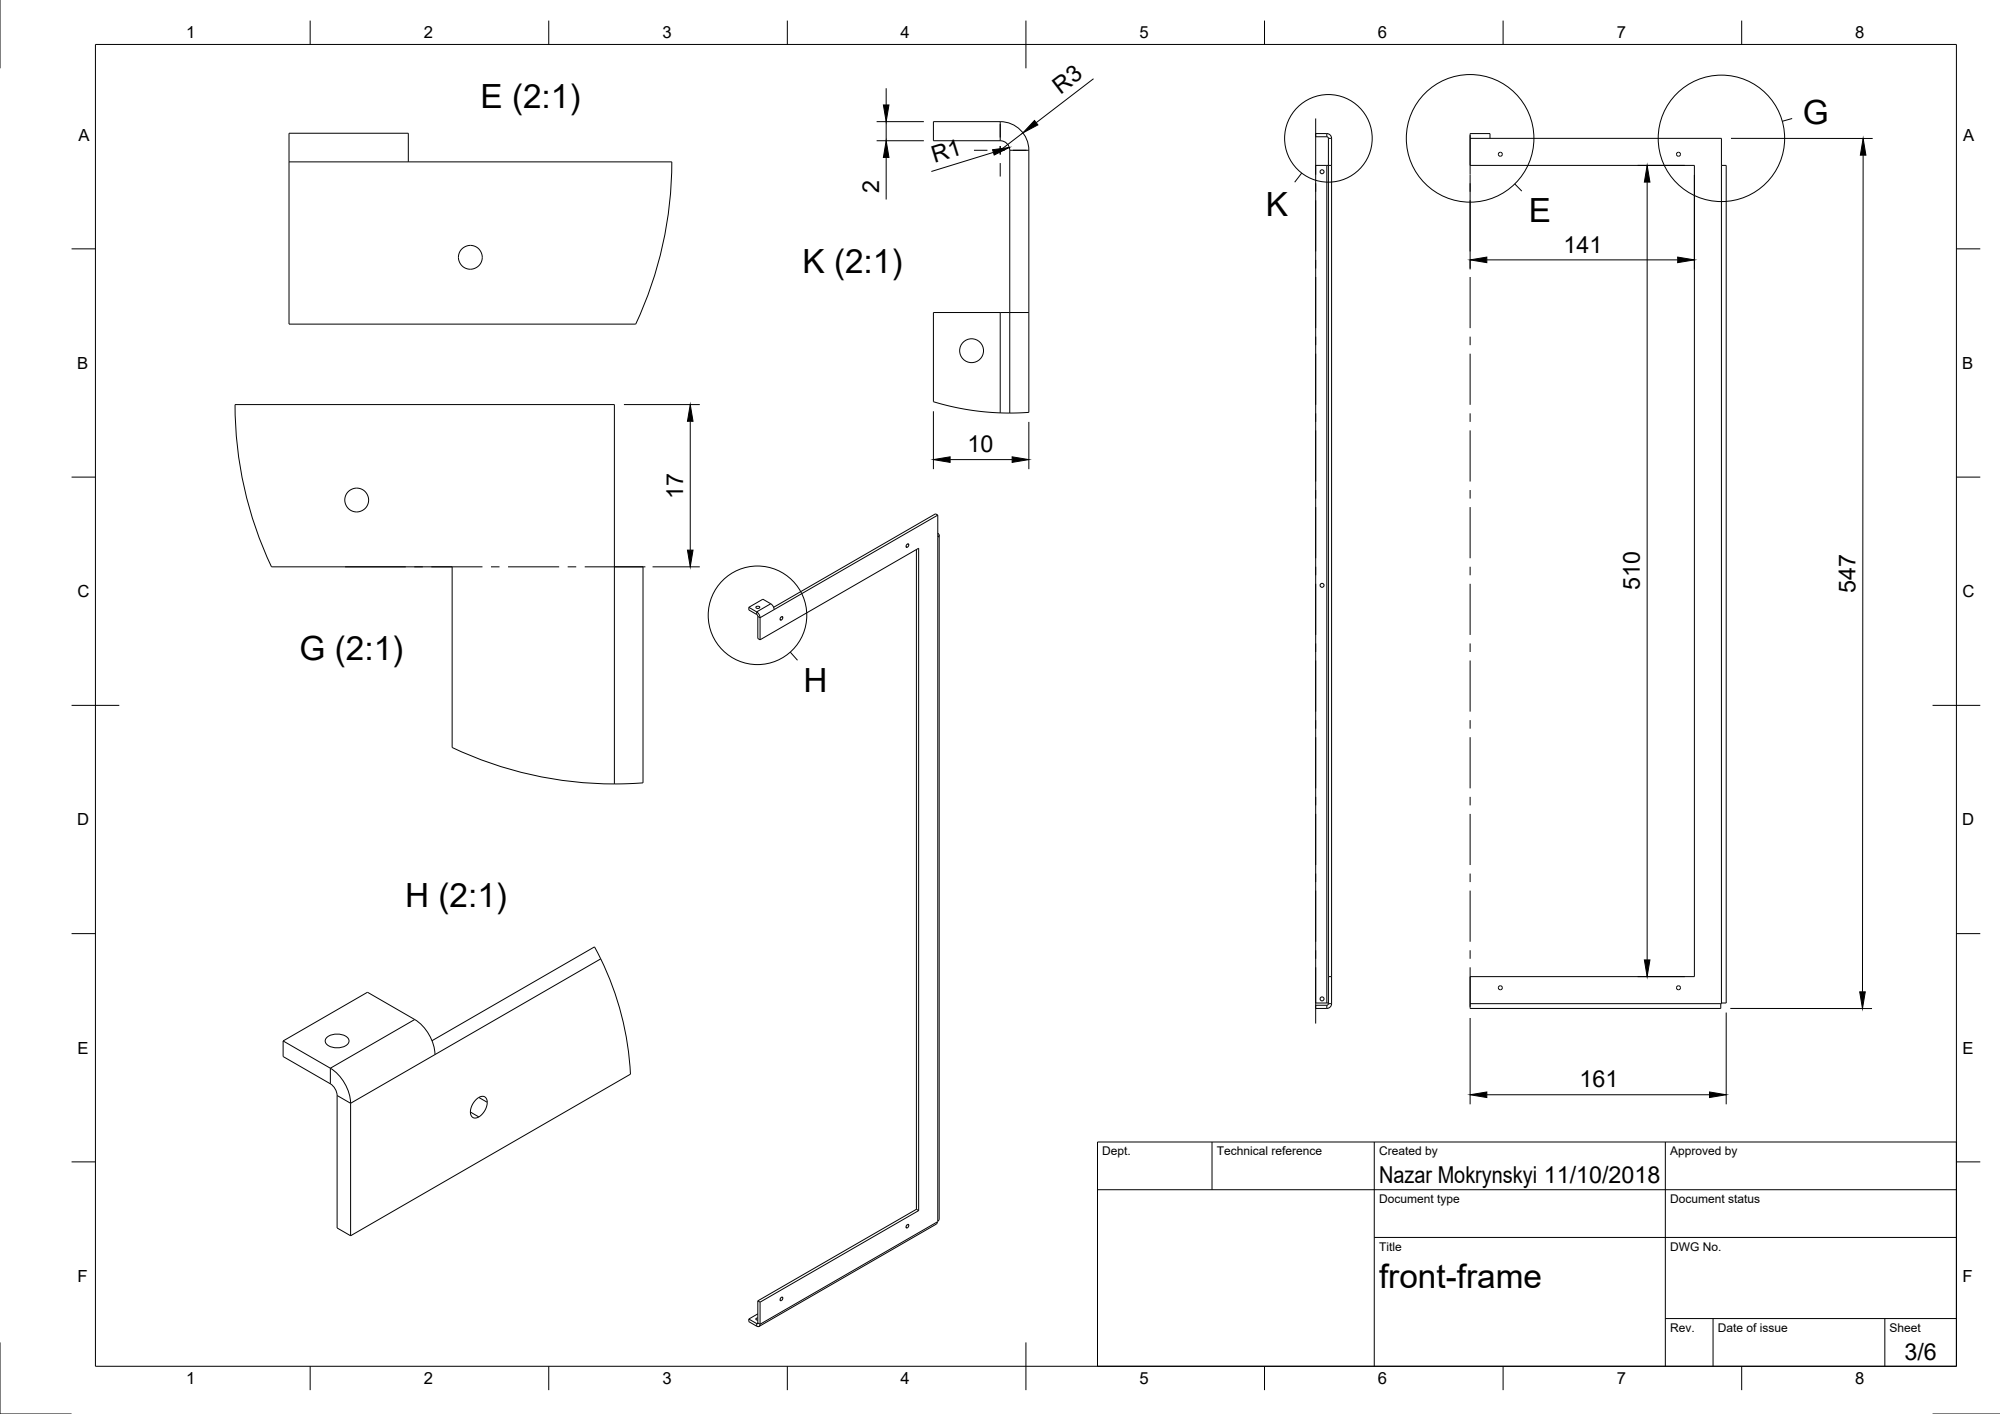
[picture p164: page 3]

Dept. | Technical reference | Created by Nazar Mokrynskyi 11/10/2018 | Approved by

Document type | Document status

Title front-frame | DWG No.

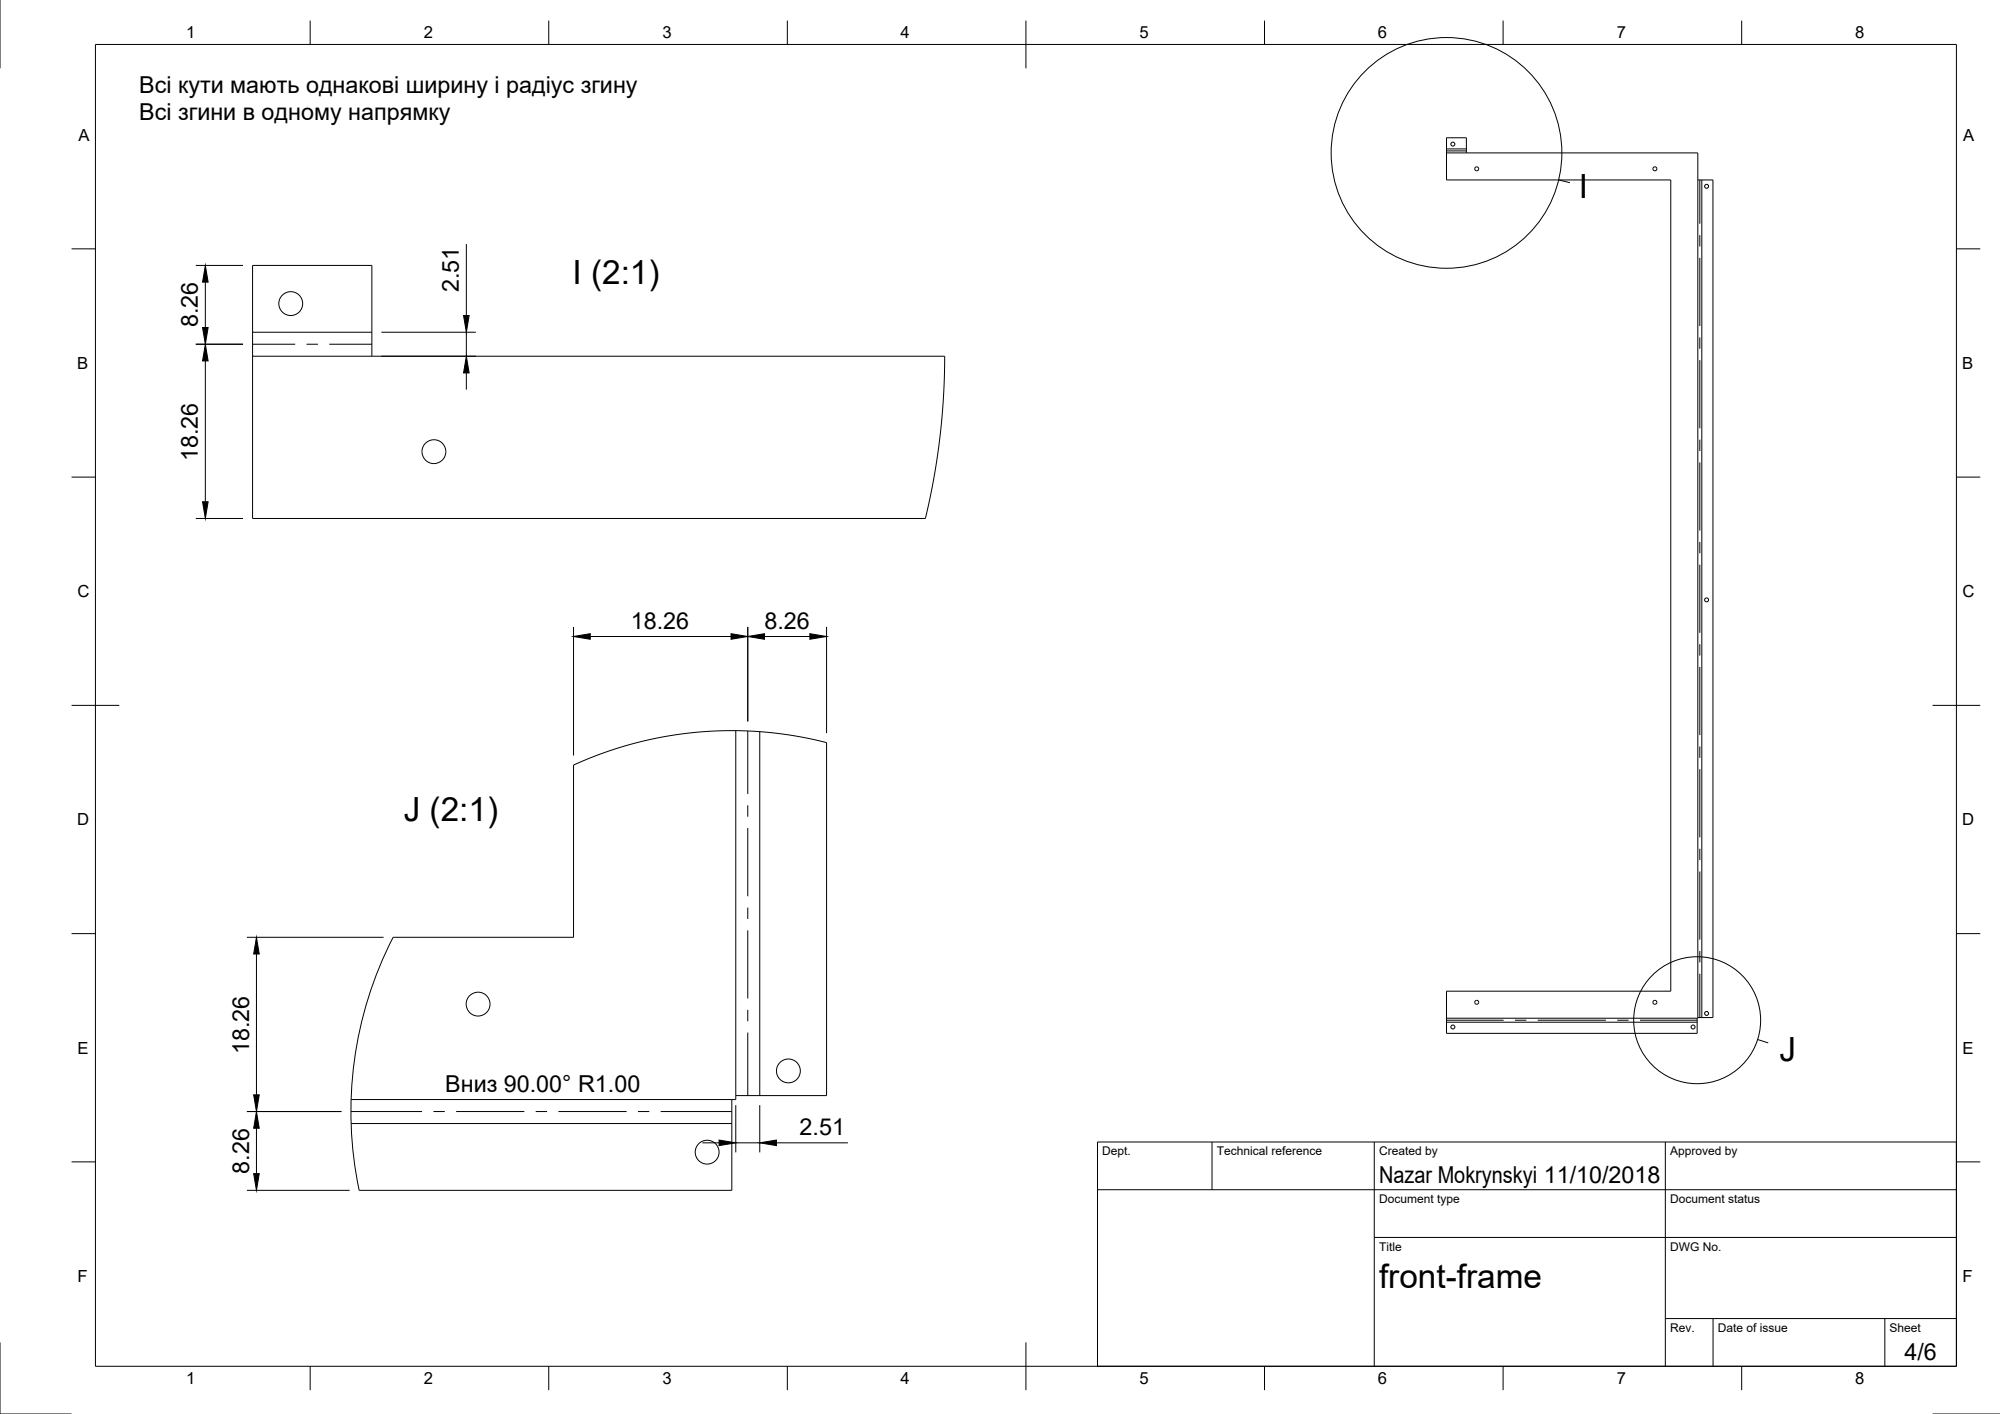
[picture p165: page 4]
Вниз 90.00° R1.00

Dept. | Technical reference | Created by Nazar Mokrynskyi 11/10/2018 | Approved by

Document type | Document status

Title front-frame | DWG No.

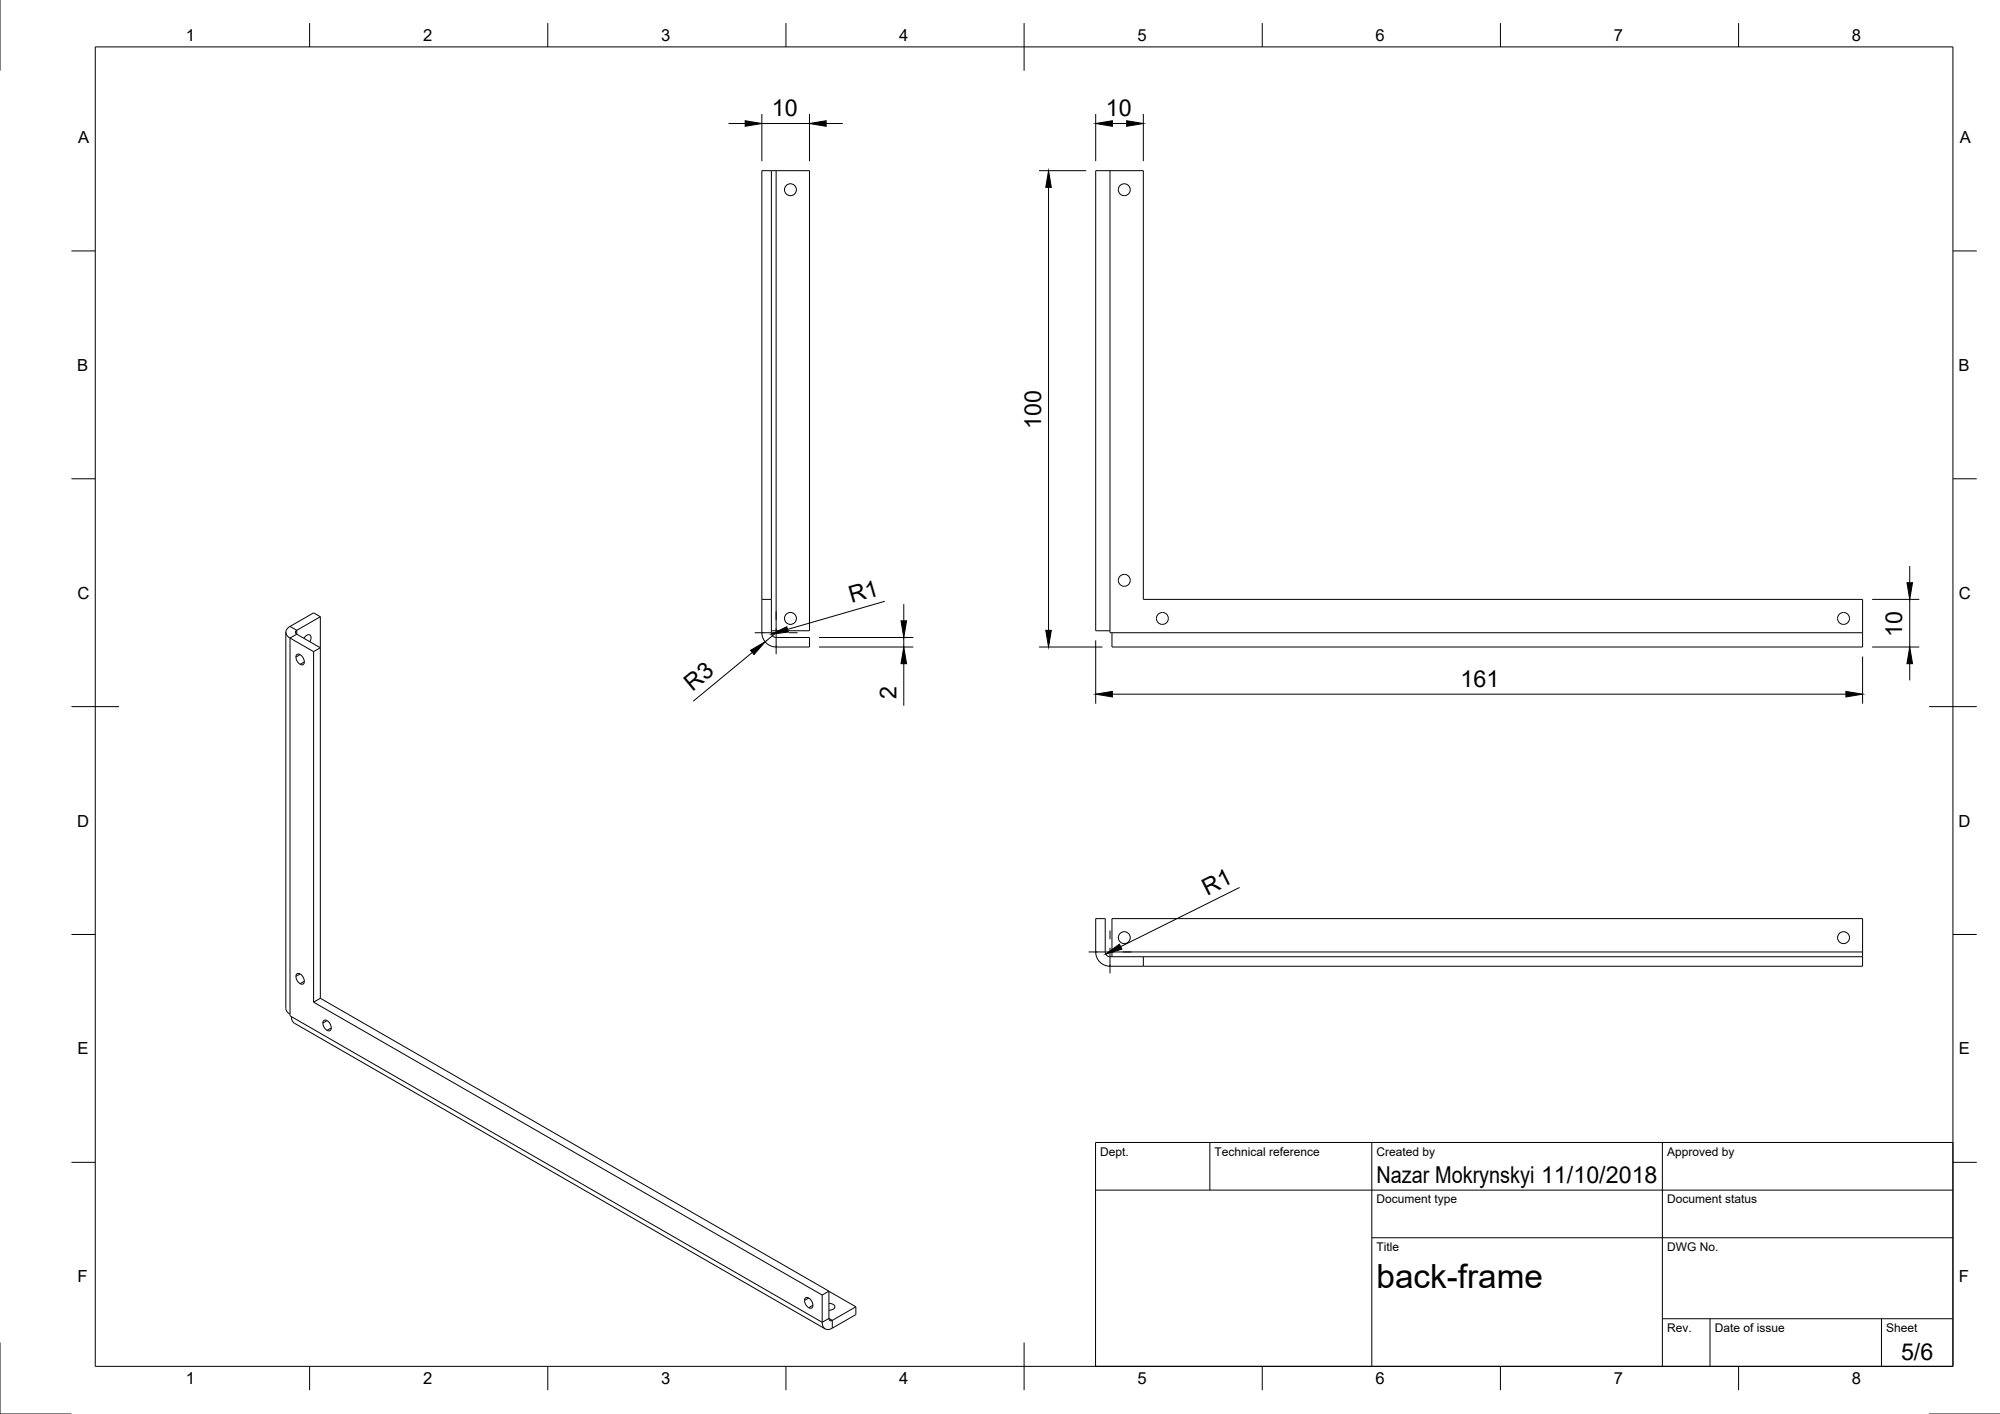
[picture p166: page 5]

Dept. | Technical reference | Created by Nazar Mokrynskyi 11/10/2018 | Approved by

Document type | Document status

Title back-frame | DWG No.

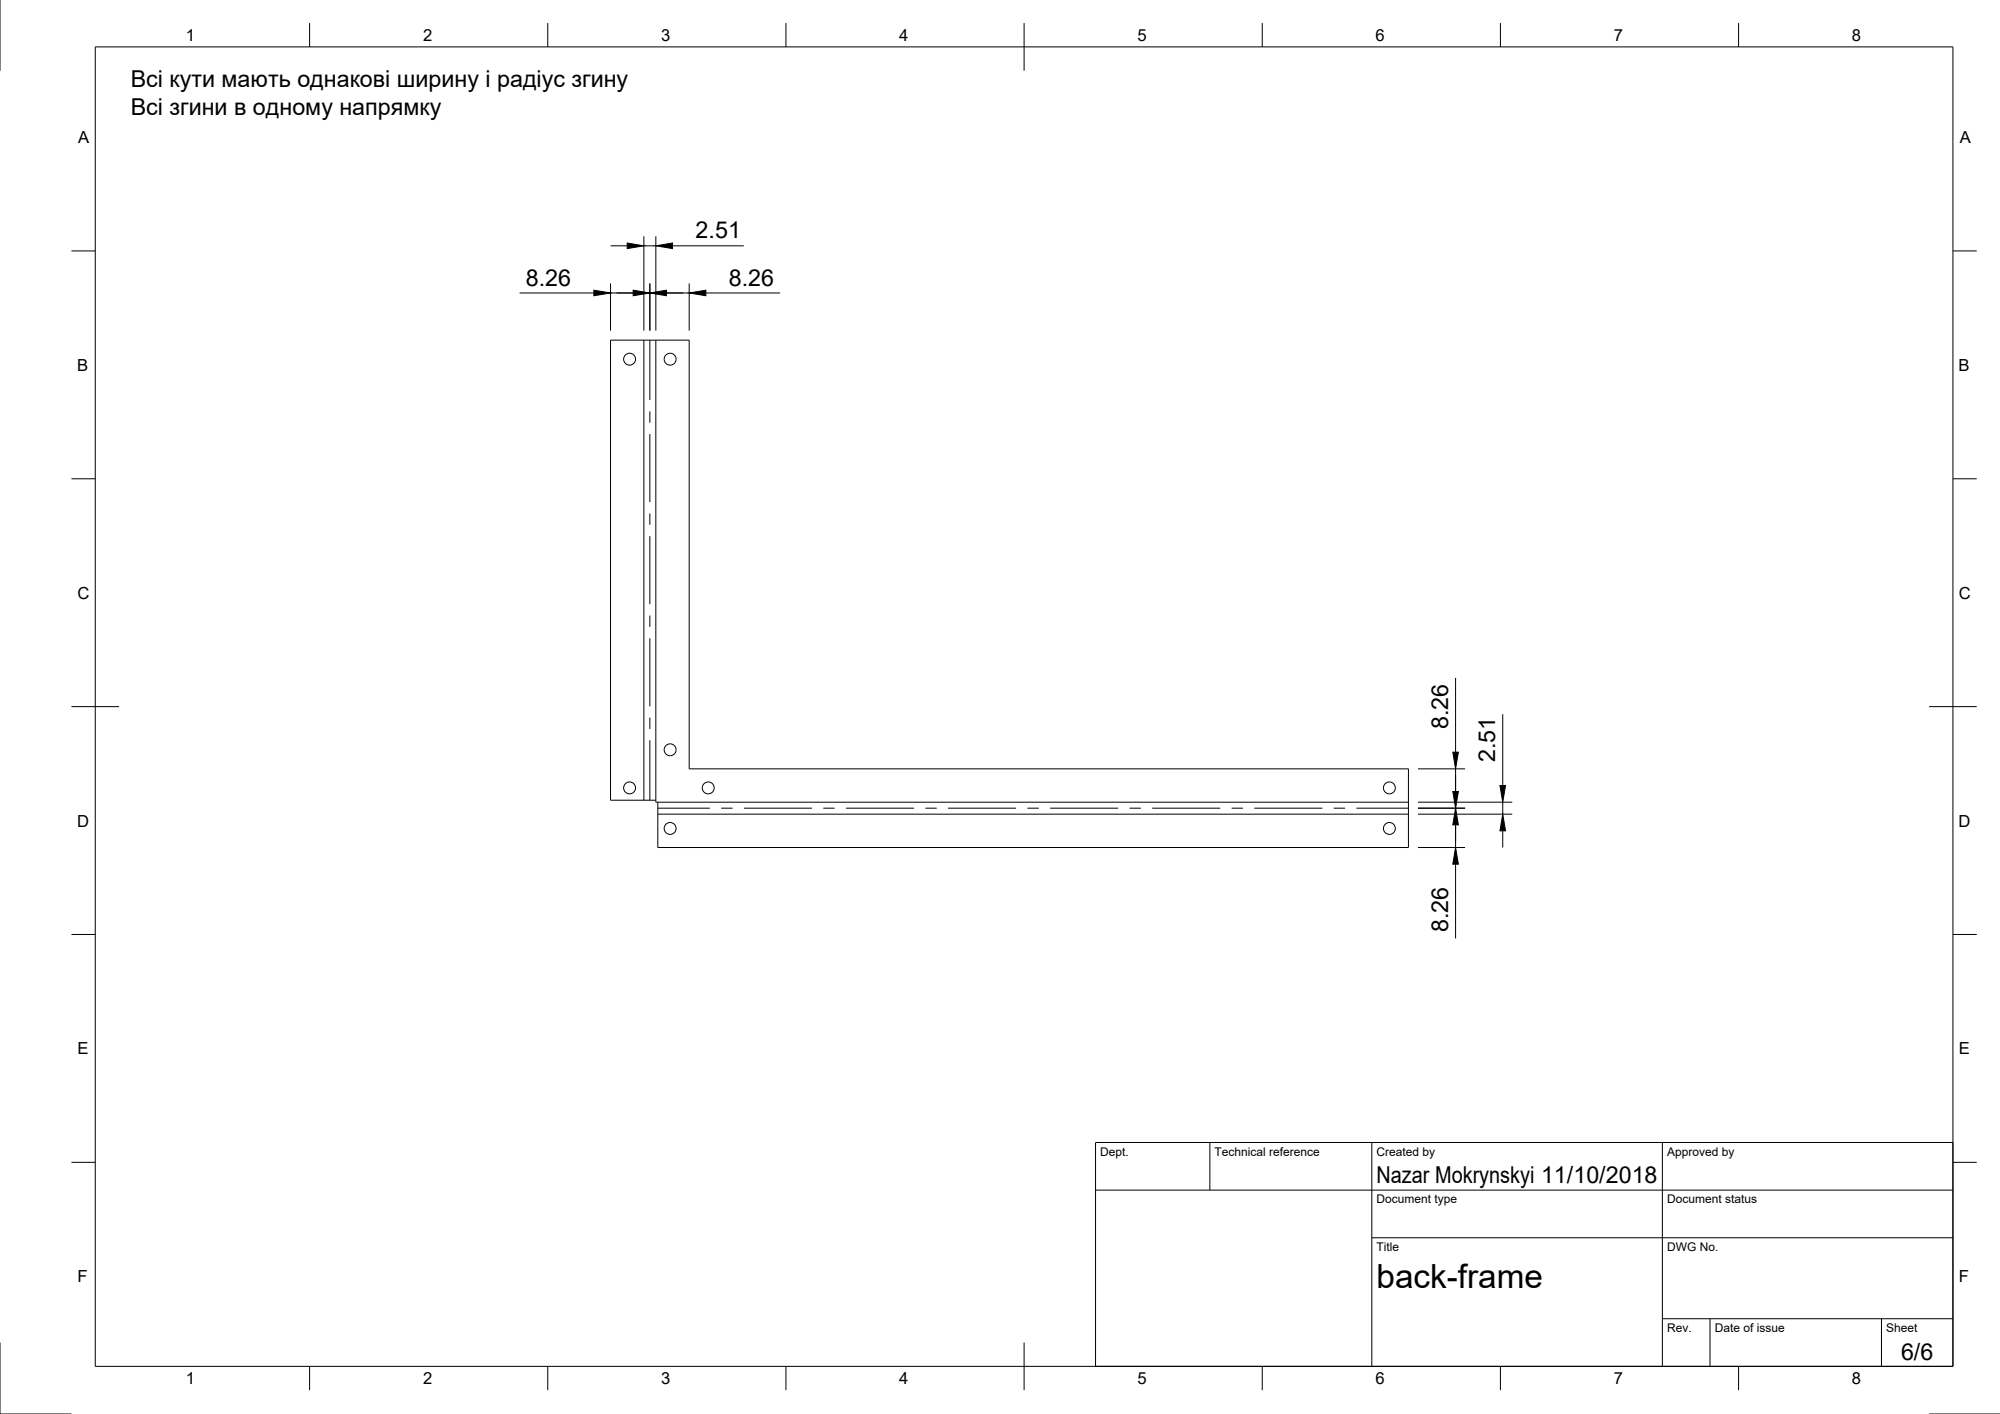
[picture p167: page 6]

Dept. | Technical reference | Created by Nazar Mokrynskyi 11/10/2018 | Approved by

Document type | Document status

Title back-frame | DWG No.
