nazar-pc/NPW-1.0/manufacturing/random-stuff/3D convertion results/right-frame.pdf

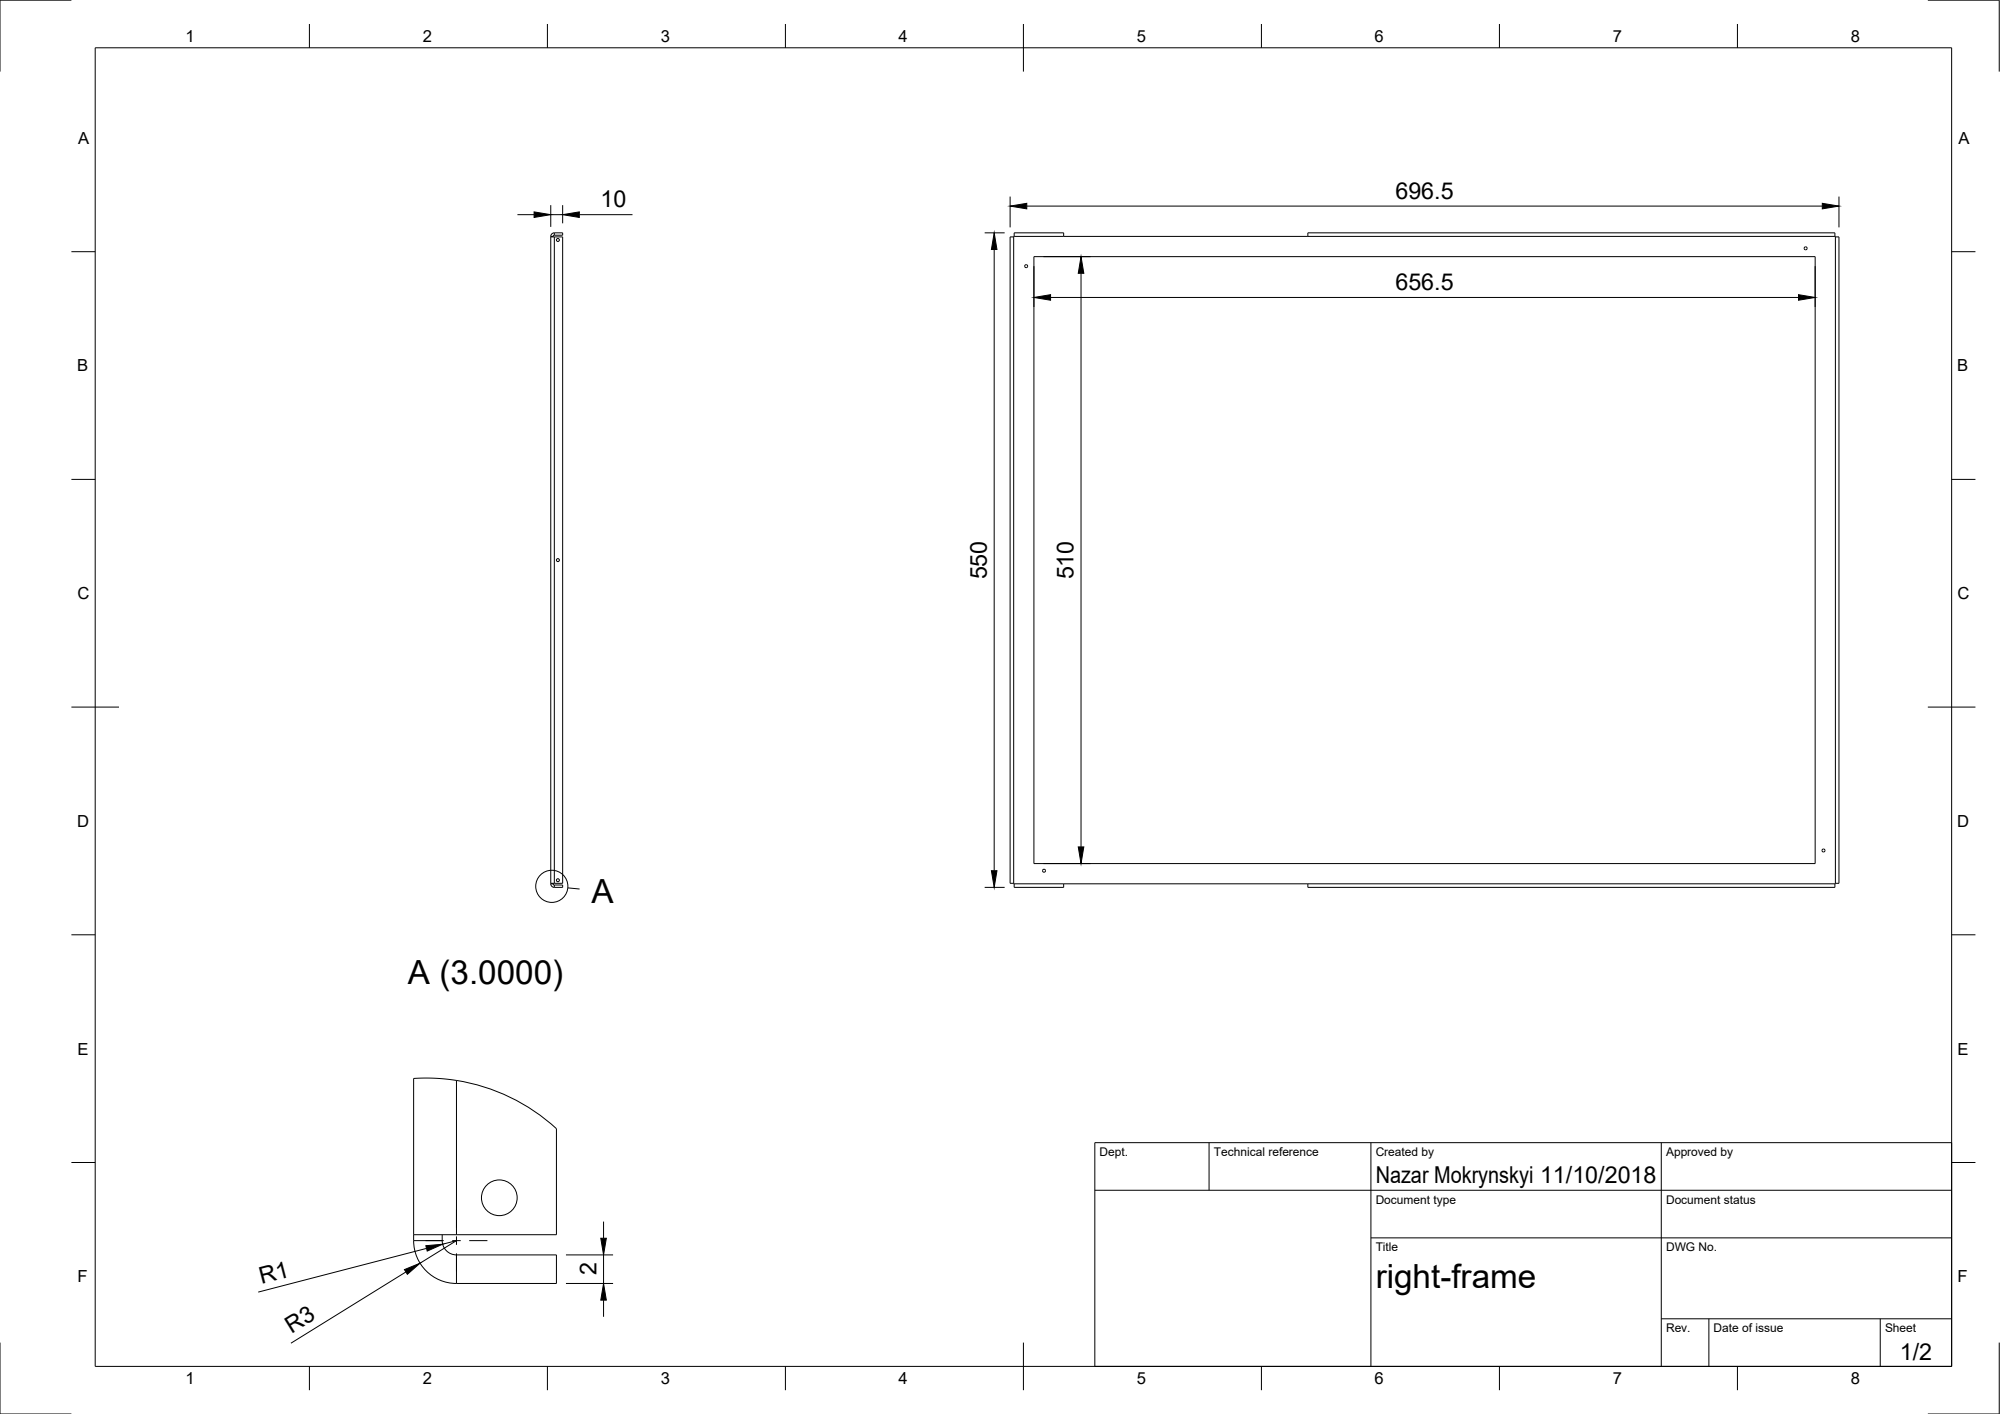
[picture p168: page 1]

Dept. | Technical reference | Created by Nazar Mokrynskyi 11/10/2018 | Approved by

Document type | Document status

Title right-frame | DWG No.

Rev. | Date of issue | Sheet 1/2

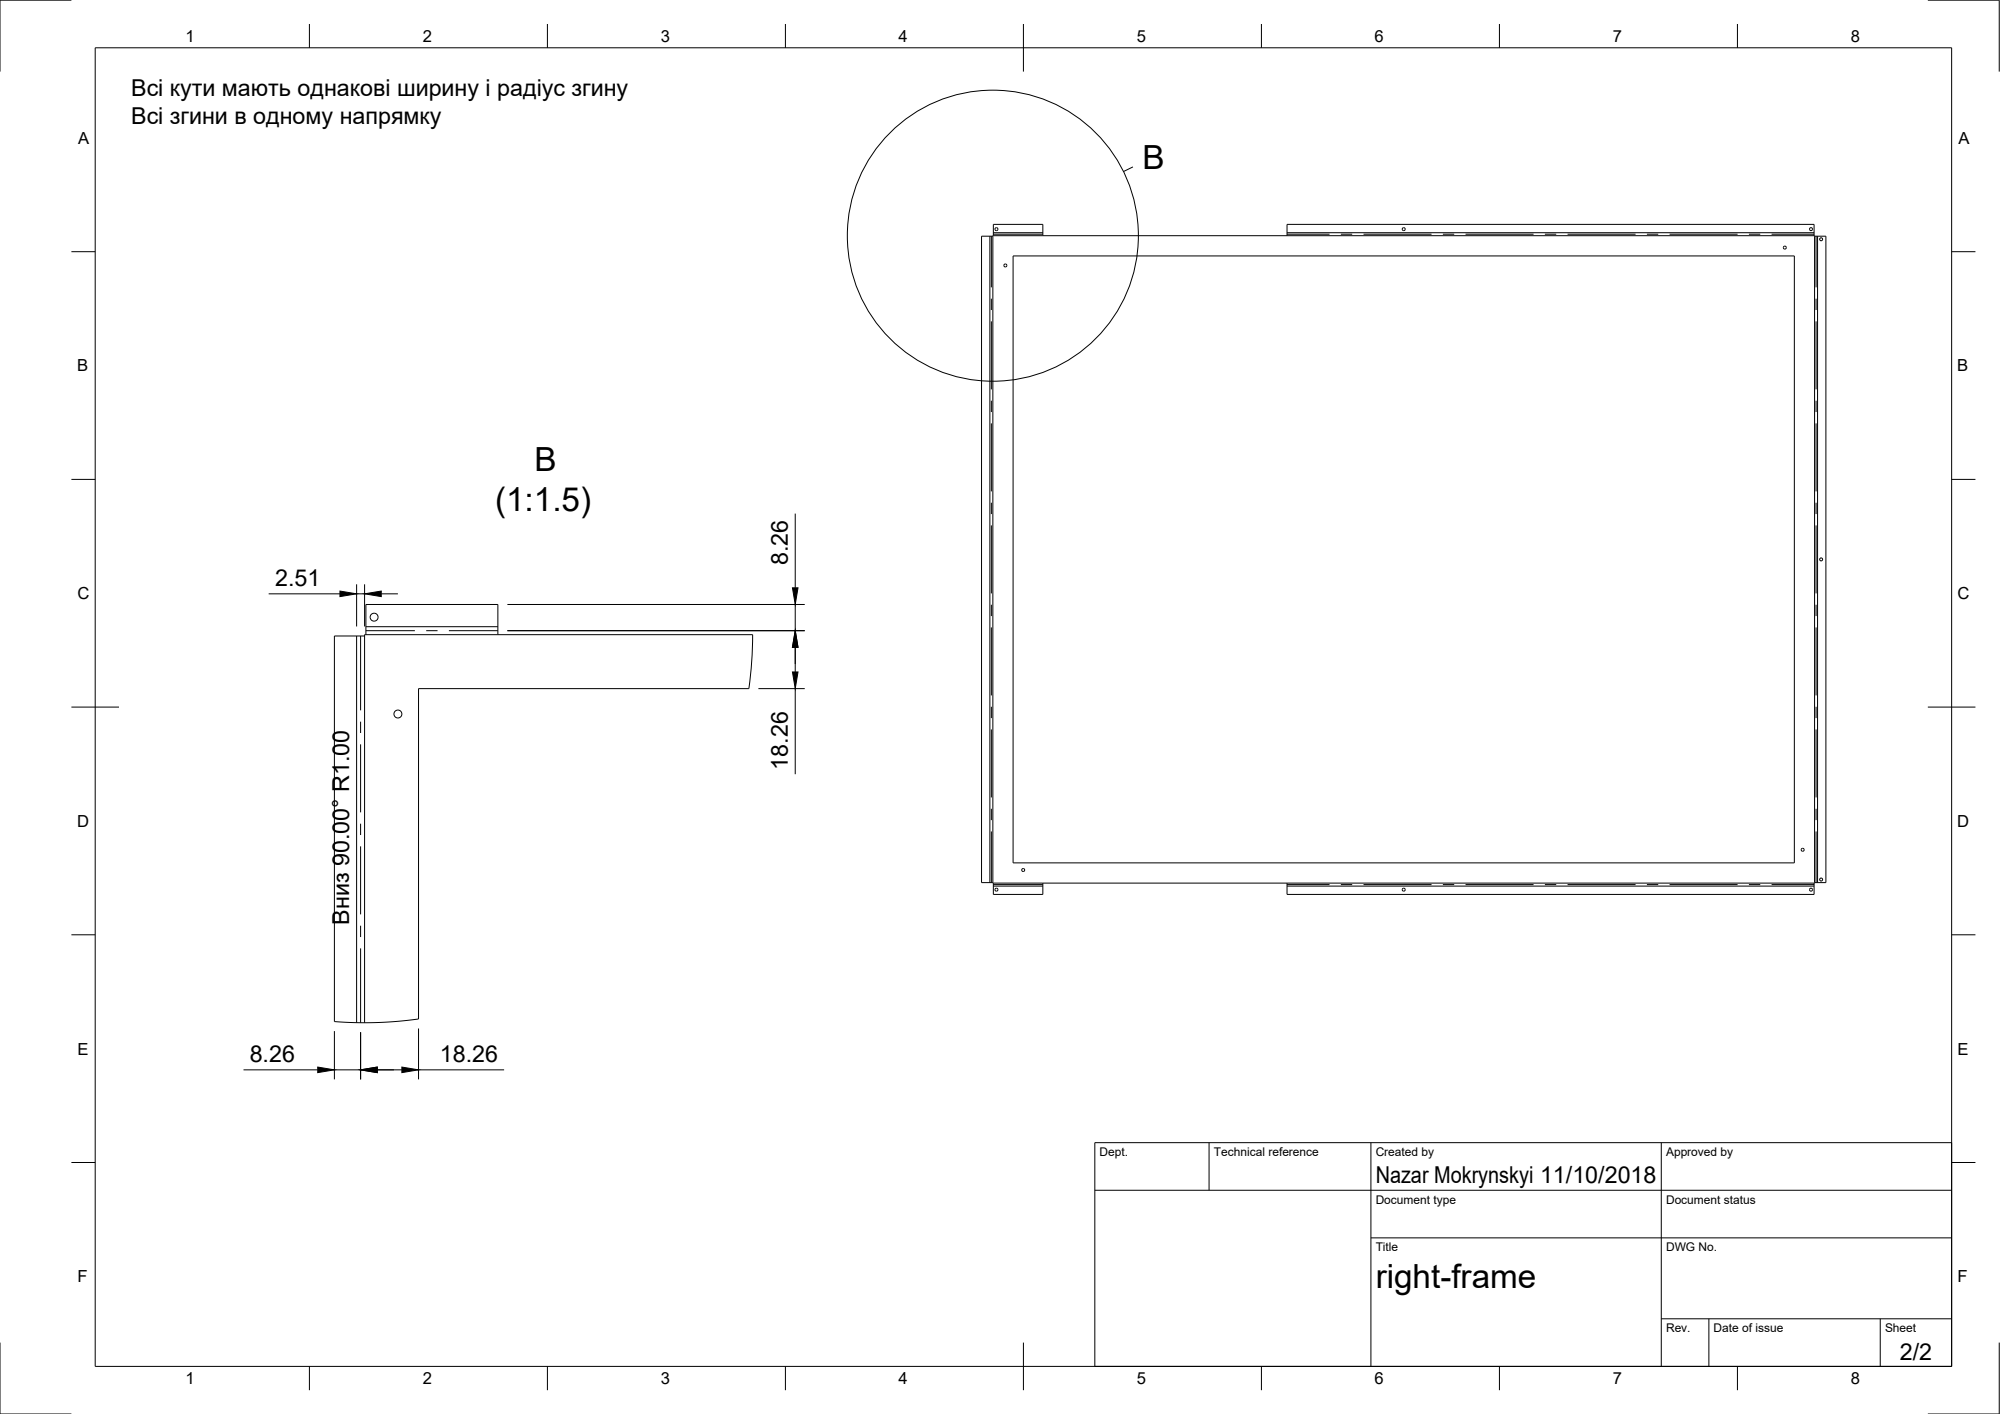
[picture p169: page 2]
2.51 Вниз 90.00° R1.00

Всі кути мають однакові ширину і радіус згину
Всі згини в одному напрямку

Dept. | Technical reference | Created by Nazar Mokrynskyi 11/10/2018 | Approved by

Document type | Document status

Title right-frame | DWG No.

Rev. | Date of issue | Sheet 2/2
