nazar-pc/NPW-1.0/manufacturing/random-stuff/Dual MB PC case sheet metal parts.PDF

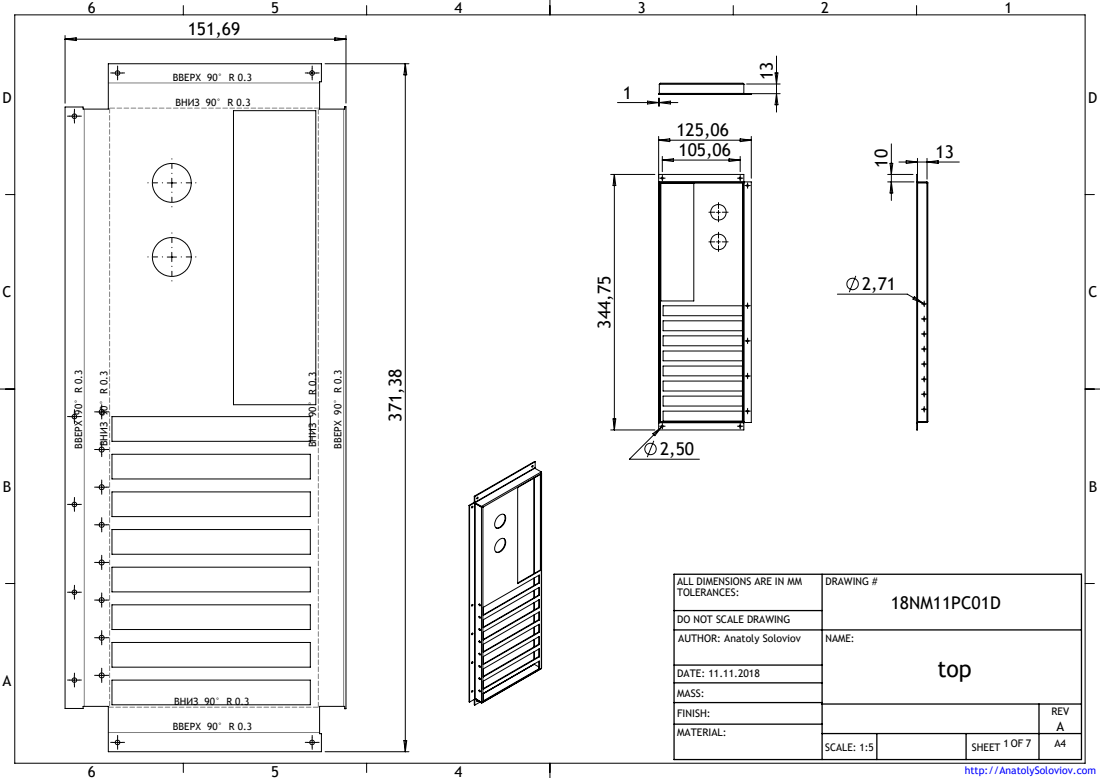
[picture p175: page 1]
ВВЕРХ 90° R 0.3; ВНИЗ 90° R 0.3; SCALE: 1:5; SHEET; DRAWING #; A MATERIAL:; DATE: 11.11.2018

ALL DIMENSIONS ARE IN MM
TOLERANCES:

DO NOT SCALE DRAWING
AUTHOR: Anatoly Soloviov

http://AnatolySoloviov.com

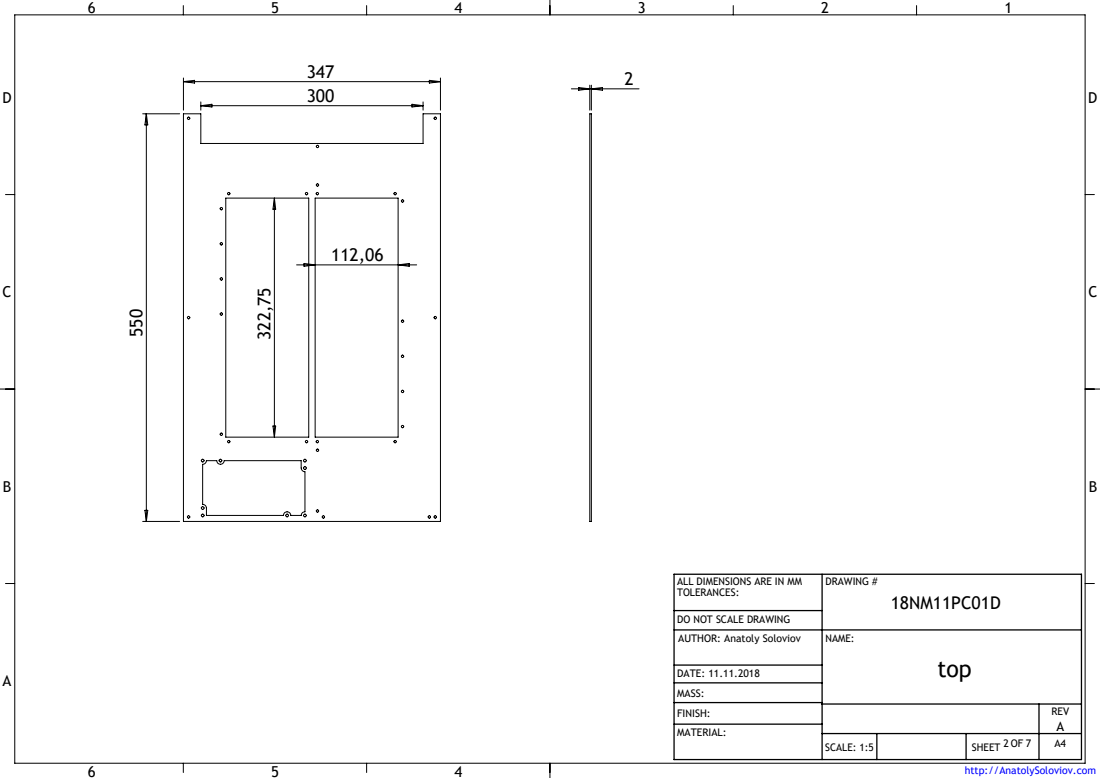
[picture p176: page 2]
DRAWING #; DATE: 11.11.2018

ALL DIMENSIONS ARE IN MM
TOLERANCES:

DO NOT SCALE DRAWING
AUTHOR: Anatoly Soloviov

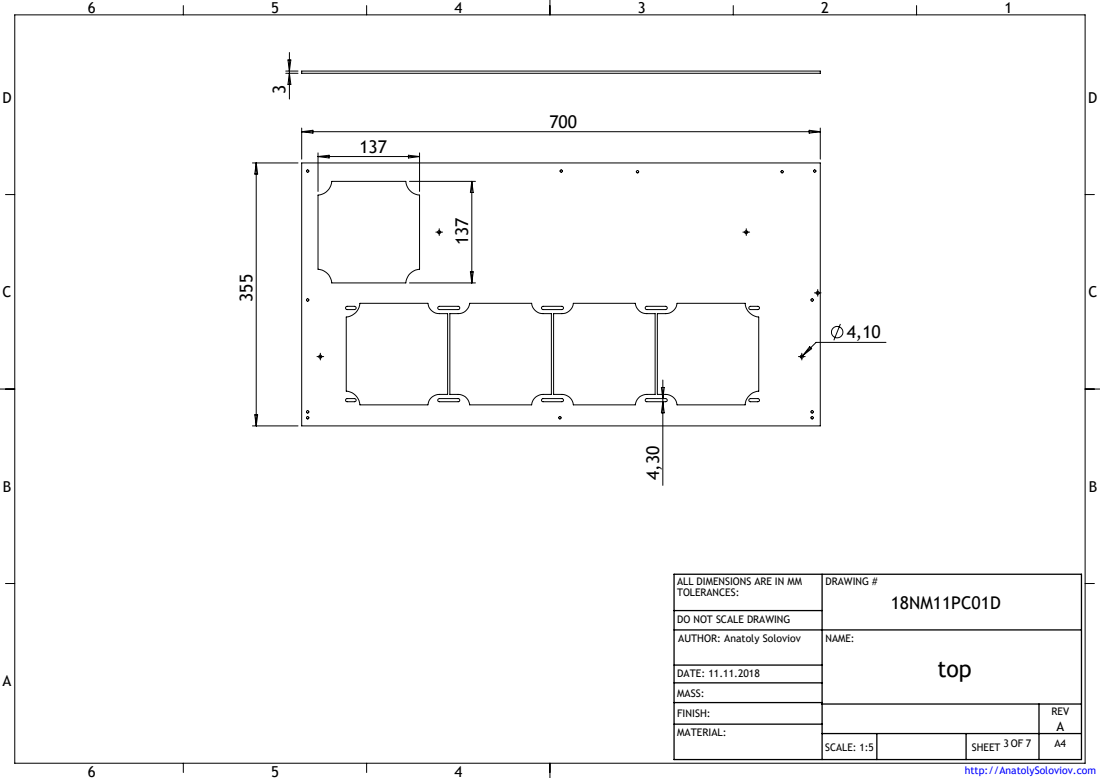
[picture p177: page 3]
DRAWING #; DATE: 11.11.2018

ALL DIMENSIONS ARE IN MM
TOLERANCES:

DO NOT SCALE DRAWING
AUTHOR: Anatoly Soloviov

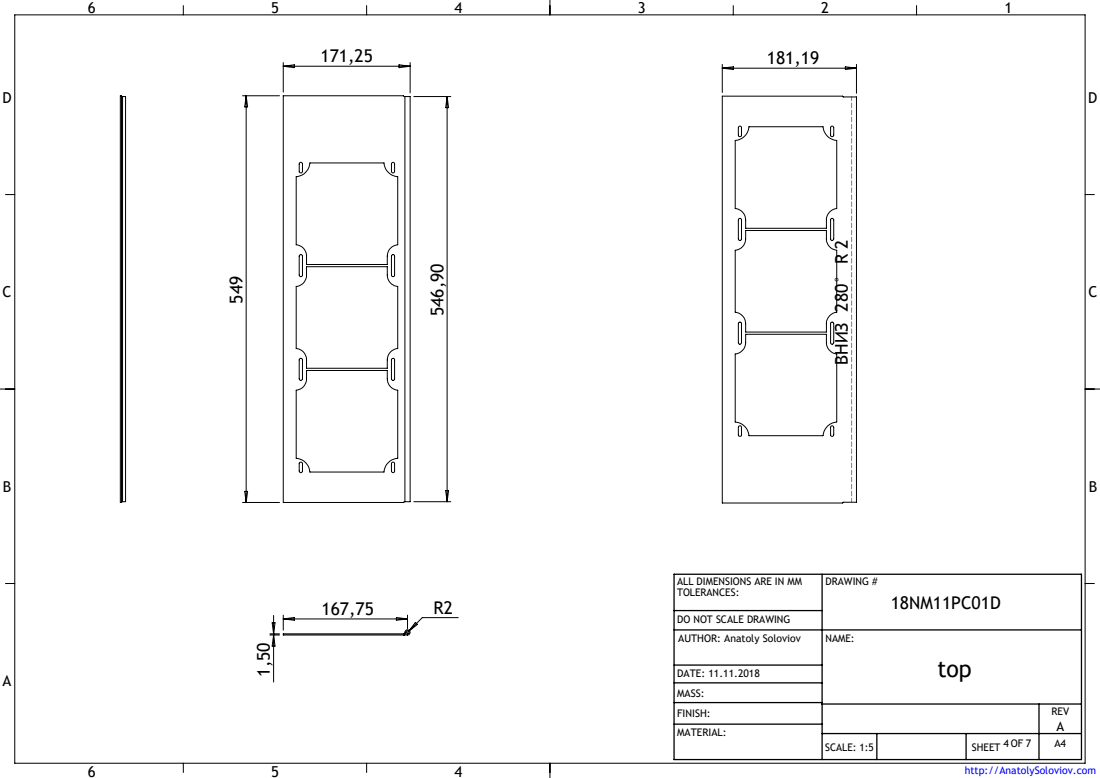
[picture p178: page 4]
ВНИЗ 280° R 2; DRAWING #; DATE: 11.11.2018

ALL DIMENSIONS ARE IN MM
TOLERANCES:

DO NOT SCALE DRAWING
AUTHOR: Anatoly Soloviov

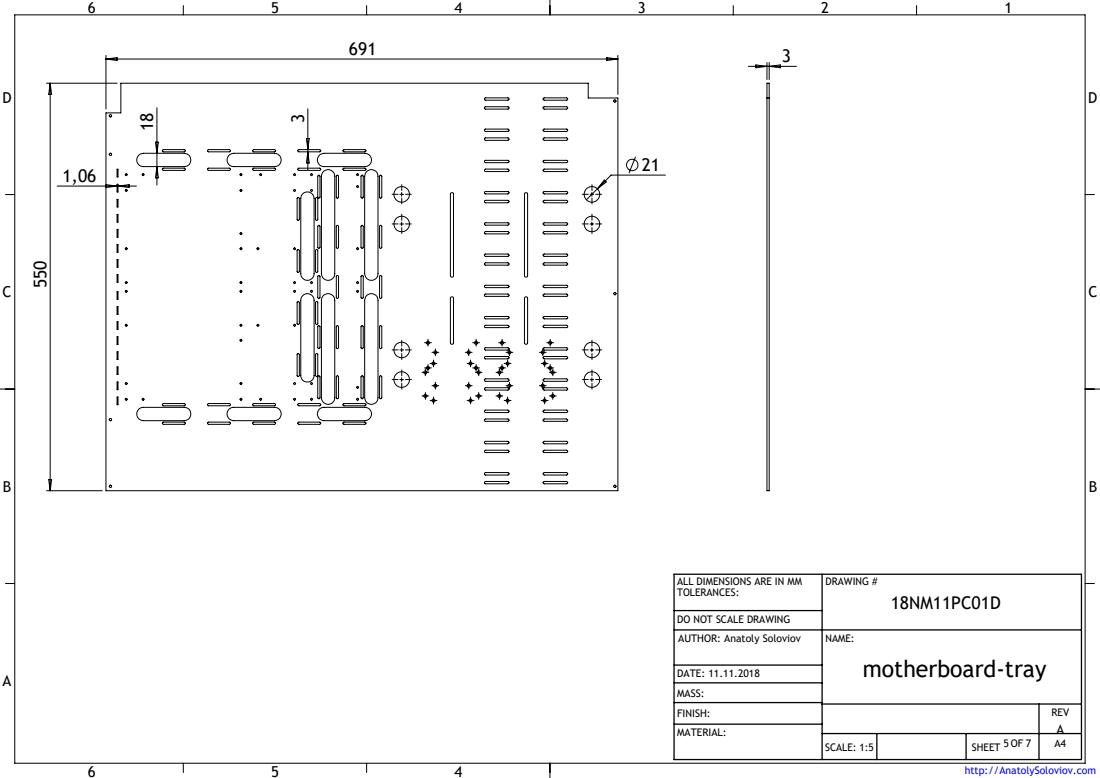
[picture p179: page 5]
DRAWING #; DATE: 11.11.2018

ALL DIMENSIONS ARE IN MM
TOLERANCES:

DO NOT SCALE DRAWING
AUTHOR: Anatoly Soloviov

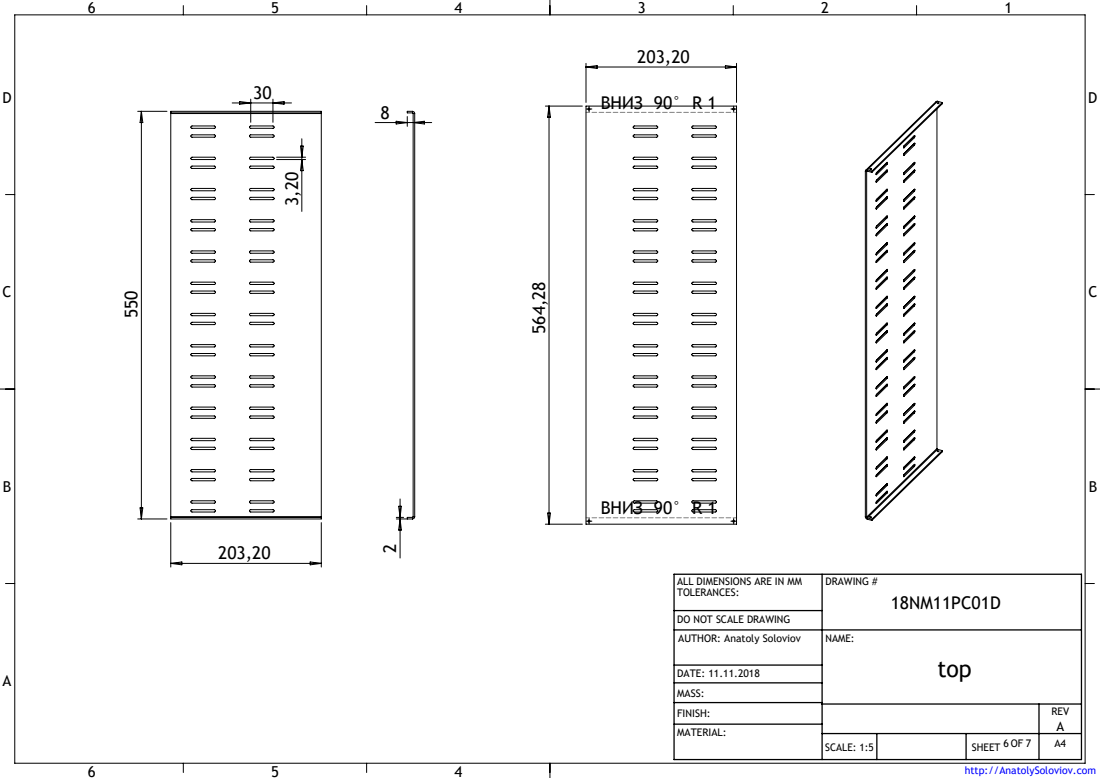
[picture p180: page 6]
ВНИЗ 90° R 1; DRAWING #; DATE: 11.11.2018

ALL DIMENSIONS ARE IN MM
TOLERANCES:

DO NOT SCALE DRAWING
AUTHOR: Anatoly Soloviov

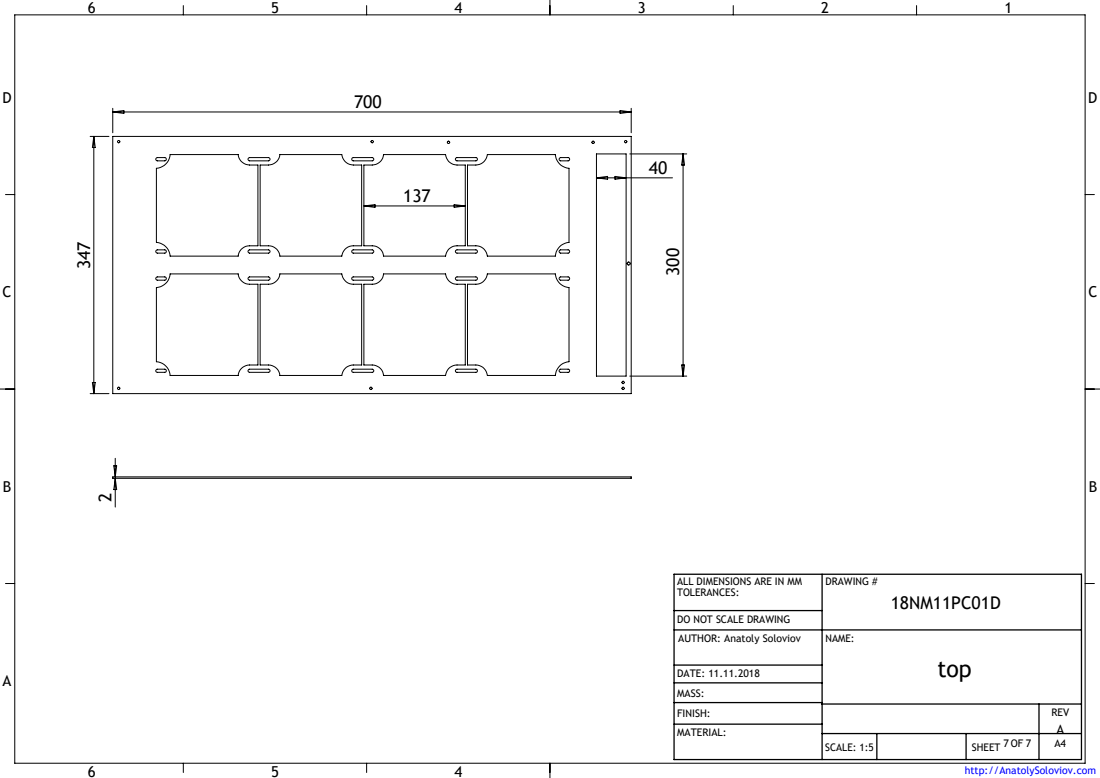
[picture p181: page 7]
DRAWING #; DATE: 11.11.2018

ALL DIMENSIONS ARE IN MM
TOLERANCES:

DO NOT SCALE DRAWING
AUTHOR: Anatoly Soloviov
