nazar-pc/NPW-1.0/manufacturing/random-stuff/Flat pattern - front-metal Drawing v0.pdf

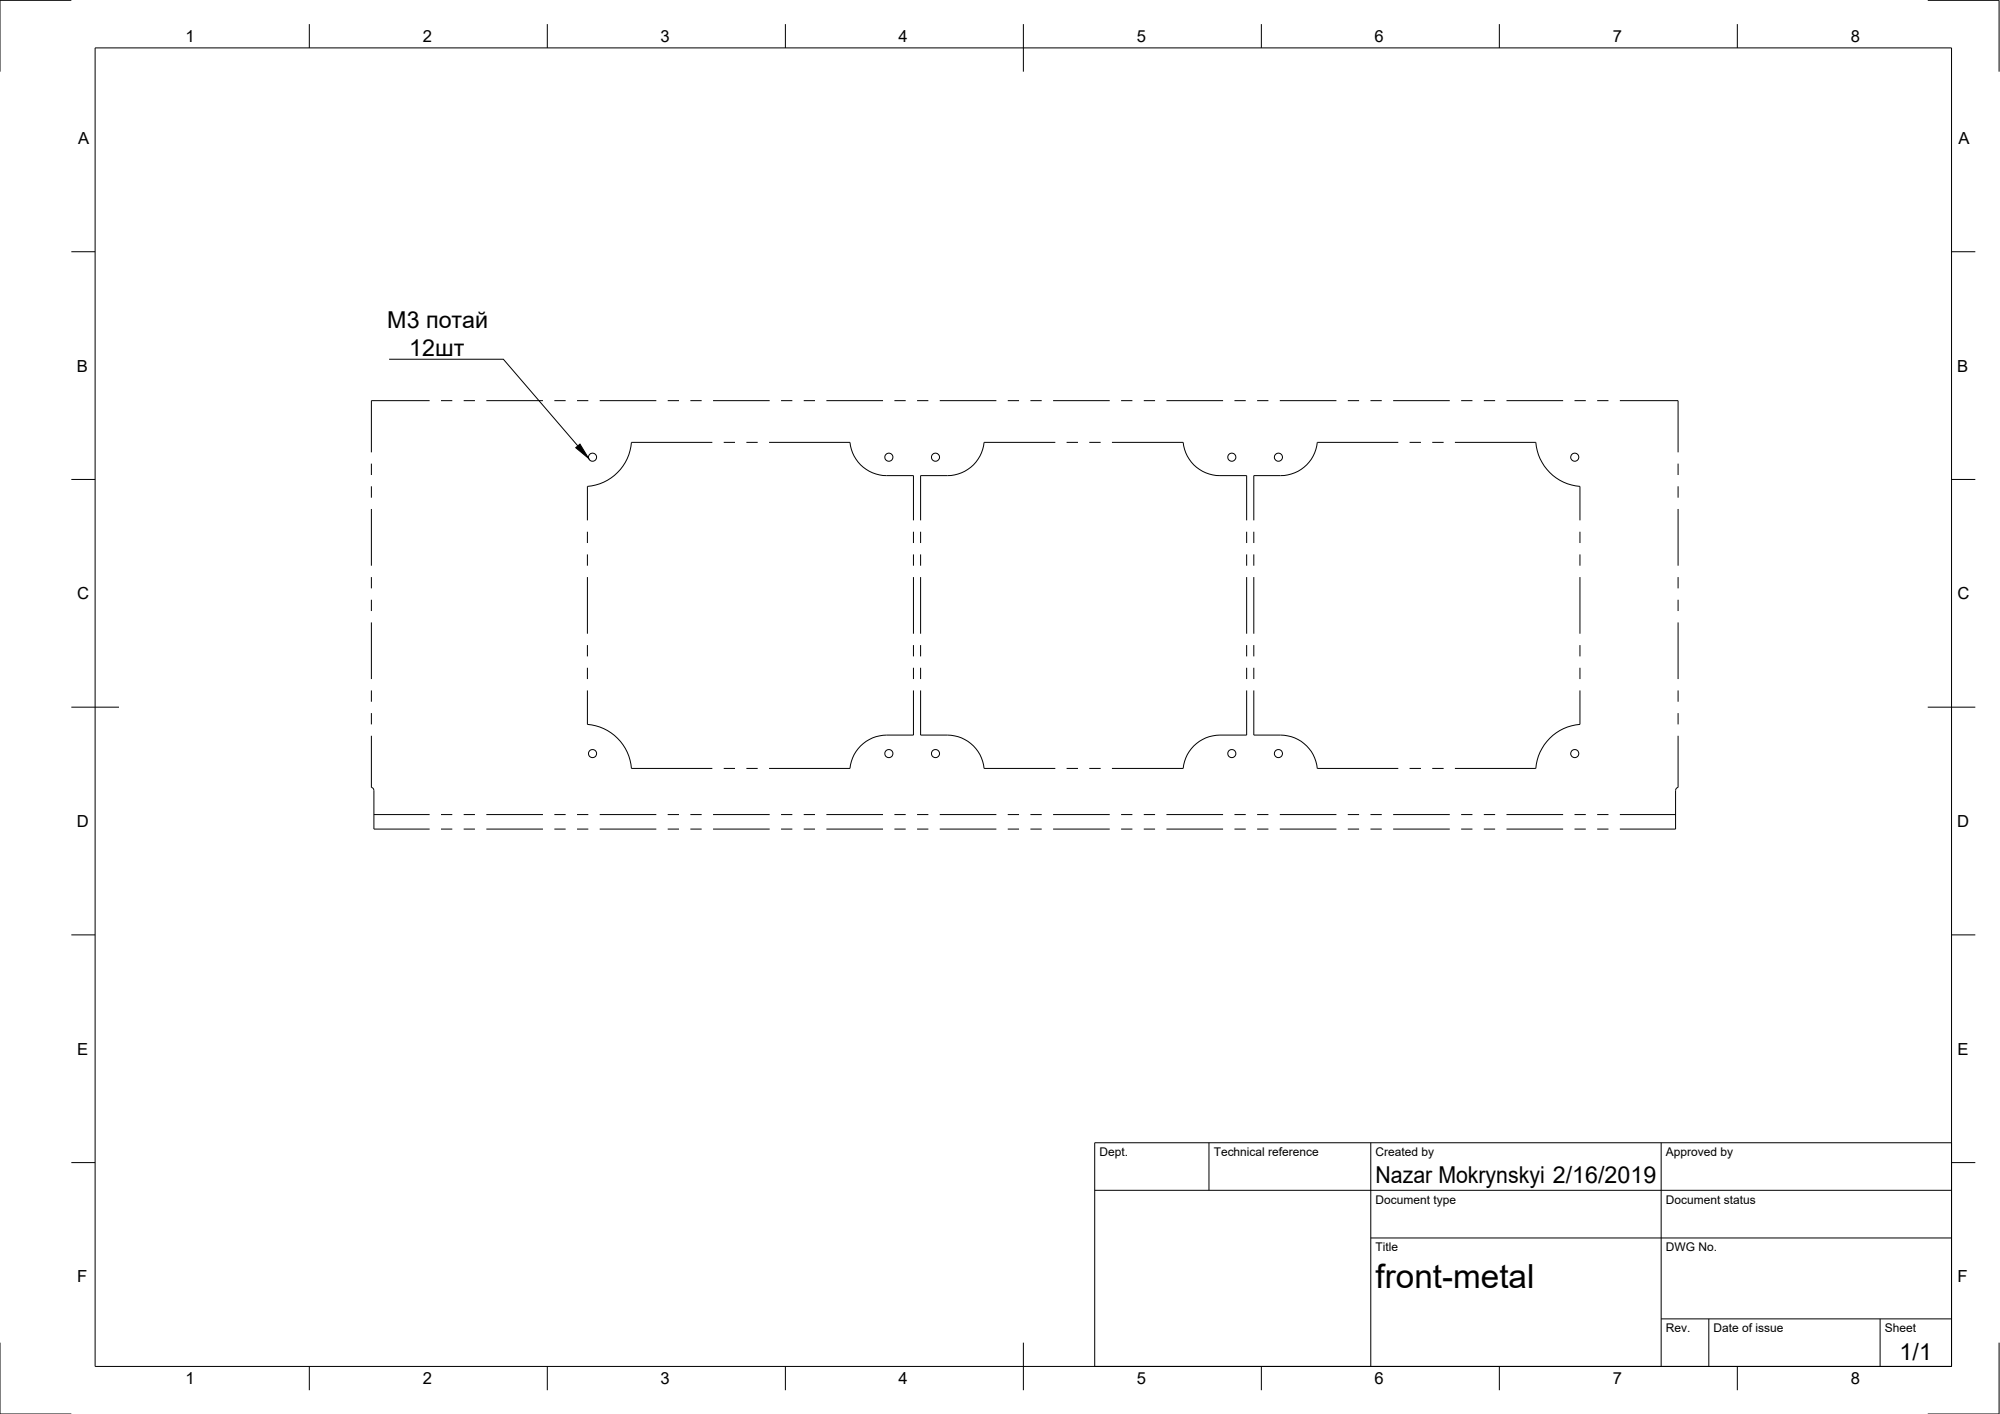
[picture p182: page 1]
М3 потай

Dept. | Technical reference | Created by Nazar Mokrynskyi 2/16/2019 | Approved by

Document type | Document status

Title front-metal | DWG No.

Rev. | Date of issue | Sheet 1/1
