nazar-pc/NPW-1.0/manufacturing/random-stuff/Flat pattern - top Drawing v1.pdf

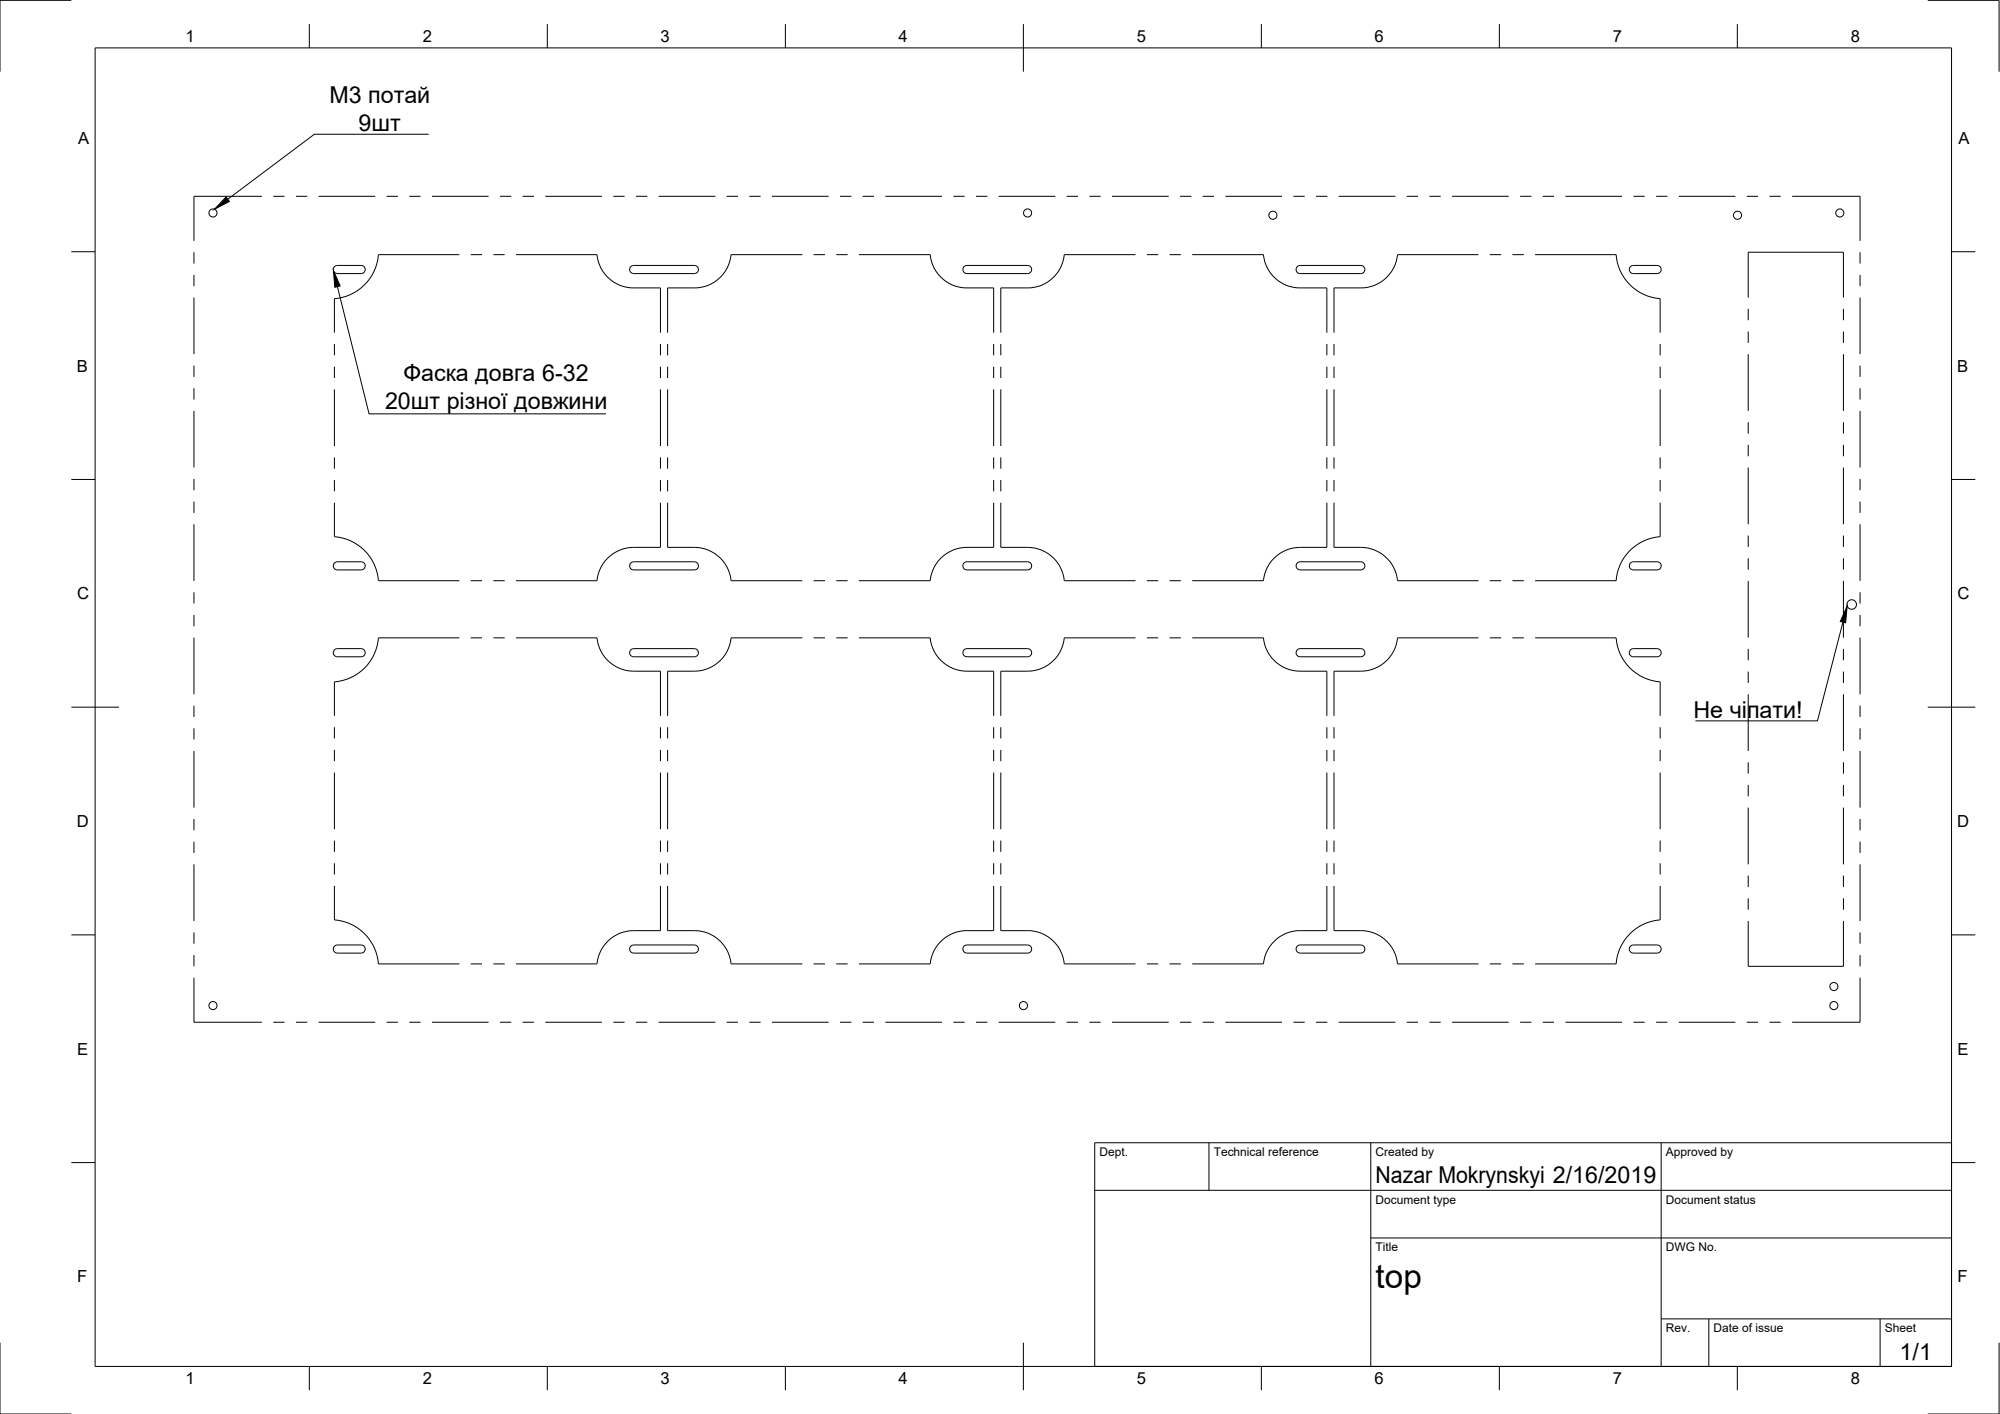
[picture p183: page 1]
Не чіпати!; М3 потай; Фаска довга 6-32 20шт різної довжини

Dept. | Technical reference | Created by Nazar Mokrynskyi 2/16/2019 | Approved by

Document type | Document status

Title top | DWG No.

Rev. | Date of issue | Sheet 1/1
