nazar-pc/NPW-1.0/manufacturing/random-stuff/3D convertion results/io-tray-x2-3d.pdf

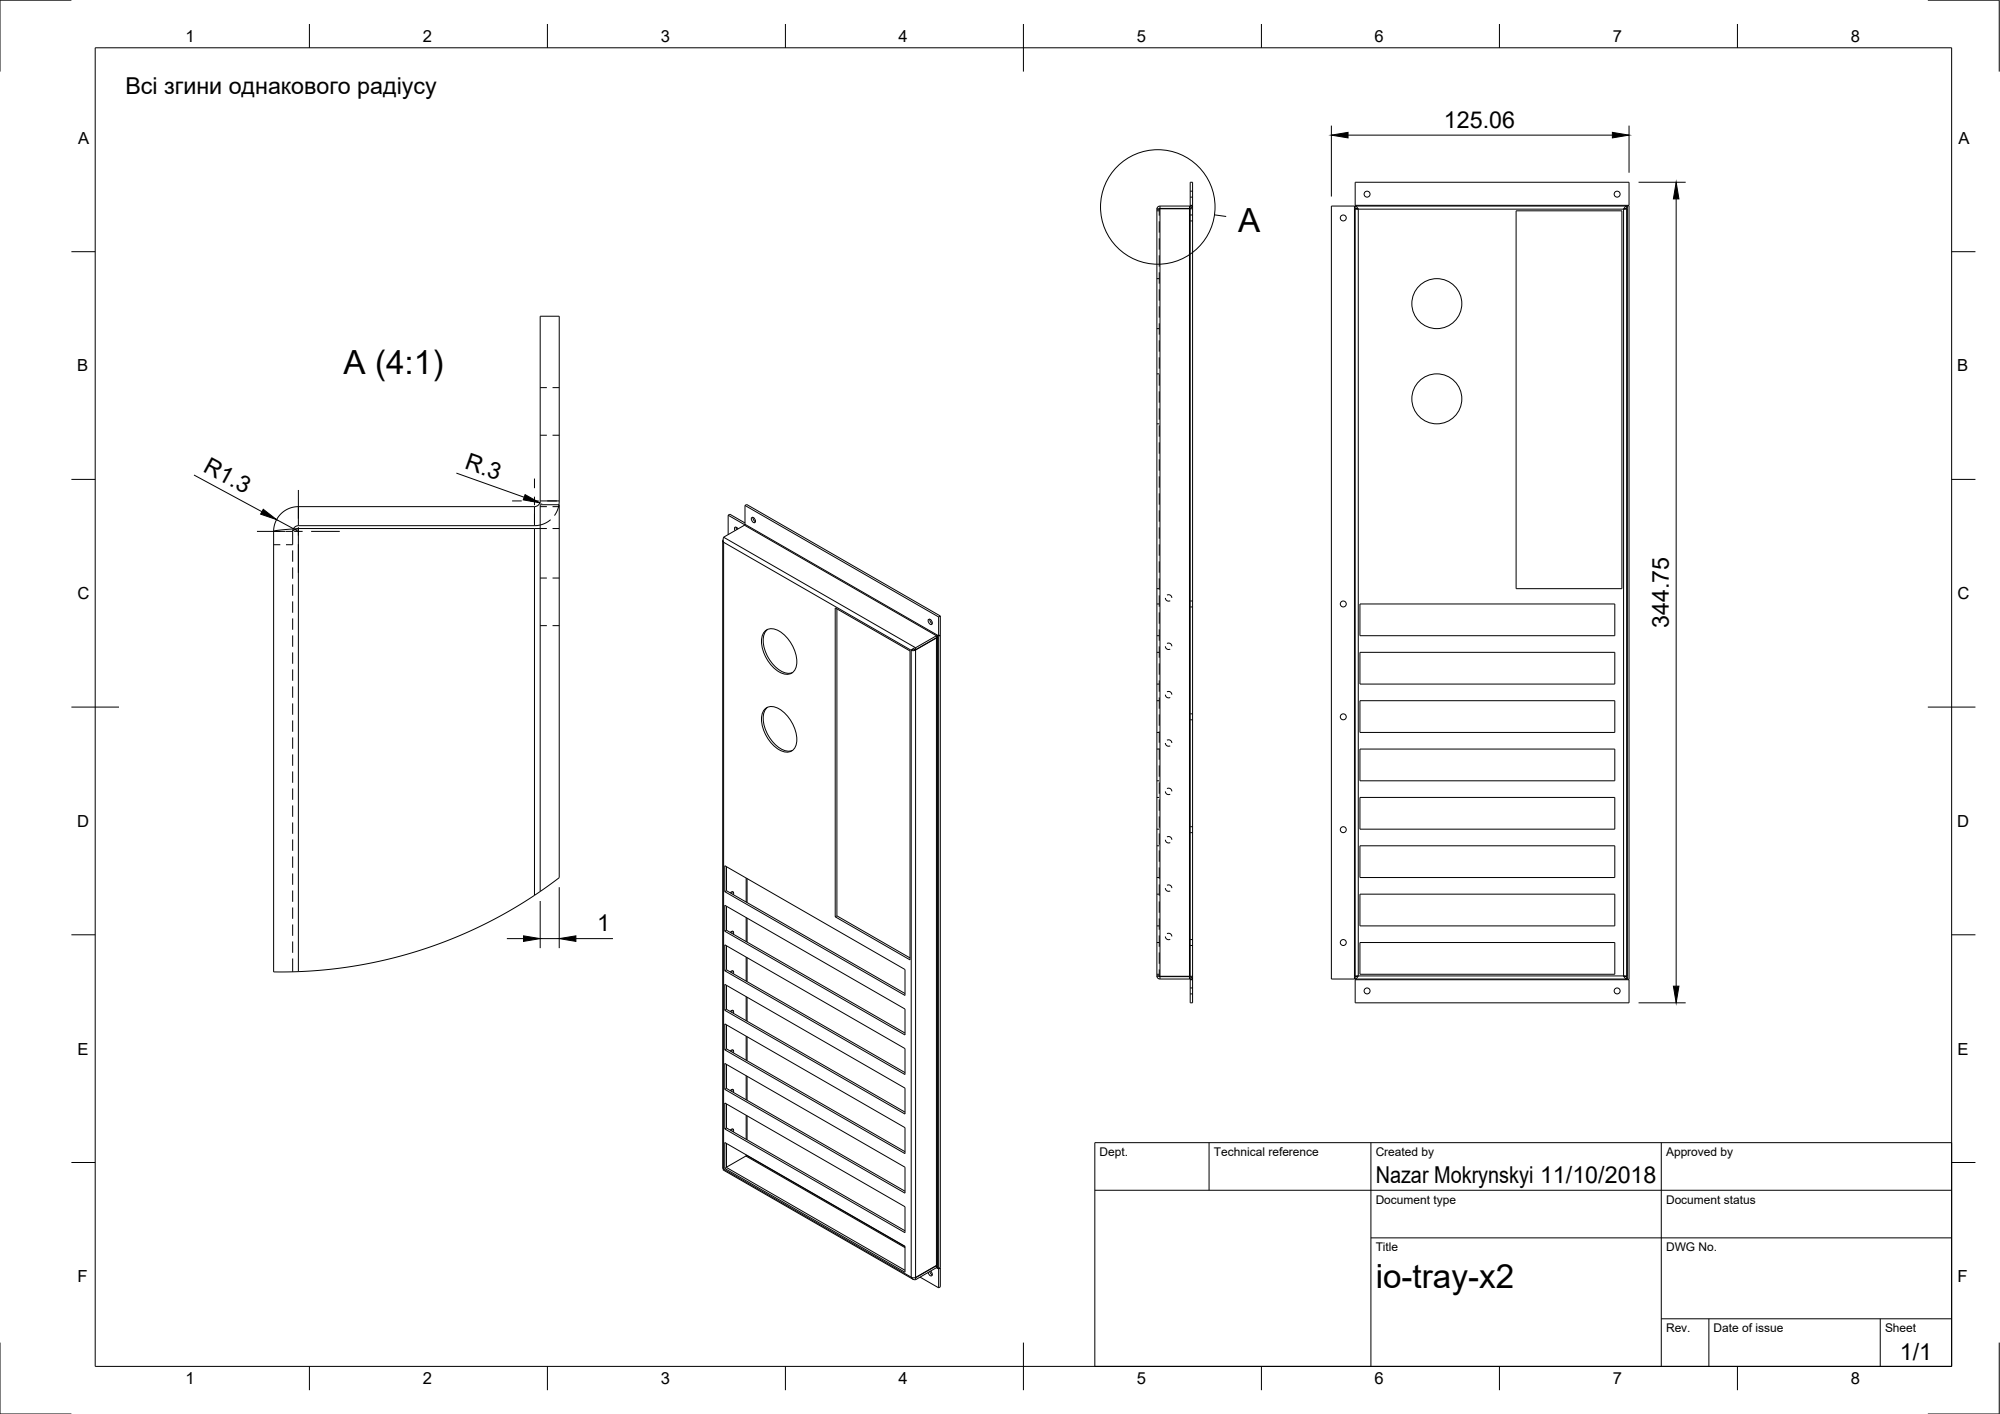
[picture p184: page 1]

Всі згини однакового радіусу

Dept. | Technical reference | Created by Nazar Mokrynskyi 11/10/2018 | Approved by

Document type | Document status

Title io-tray-x2 | DWG No.

Rev. | Date of issue | Sheet 1/1
